vrbadev/Gloves-Equipped-with-Motion-Sensors-Bachelor-Project-HW-FW-SW/Firmware/uVision/lib_sensors/src/LPS22HBSensor.c

/**
 ******************************************************************************
 * @file    LPS22HBSensor.cpp
 * @author  AST
 * @version V1.0.0
 * @date    7 September 2017
 * @brief   Implementation of a LPS22HB Pressure sensor.
 ******************************************************************************
 * @attention
 *
 * <h2><center>&copy; COPYRIGHT(c) 2017 STMicroelectronics</center></h2>
 *
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
 ******************************************************************************
 */


/* Includes ------------------------------------------------------------------*/

#include "../inc/LPS22HBSensor.h"

/* Private functions */
LPS22HBStatusTypeDef LPS22HBSensor_SetODR_When_Enabled  (float odr);
LPS22HBStatusTypeDef LPS22HBSensor_SetODR_When_Disabled (float odr);

/* Private sensor data 
[0] -> isEnabled
[1] -> Last_ODR
*/
extern uint32_t* selected_sensor_private_data;

/* Class Implementation ------------------------------------------------------*/

/** Constructor
 * @param i2c object of an helper class which handles the I2C peripheral
 * @param address the address of the component's instance
 */
LPS22HBStatusTypeDef LPS22HBSensor_Init(void)
{
  if ( LPS22HB_Set_PowerMode( LPS22HB_LowPower) == LPS22HB_ERROR )
  {
    return LPS22HB_STATUS_ERROR;
  }

  /* Power down the device */
  if ( LPS22HB_Set_Odr( LPS22HB_ODR_ONE_SHOT ) == LPS22HB_ERROR )
  {
    return LPS22HB_STATUS_ERROR;
  }

  /* Disable low-pass filter on LPS22HB pressure data */
  if( LPS22HB_Set_LowPassFilter( LPS22HB_DISABLE) == LPS22HB_ERROR )
  {
    return LPS22HB_STATUS_ERROR;
  }

  /* Set low-pass filter cutoff configuration*/
  if( LPS22HB_Set_LowPassFilterCutoff( LPS22HB_ODR_9) == LPS22HB_ERROR )
  {
    return LPS22HB_STATUS_ERROR;
  }

  /* Set block data update mode */
  if ( LPS22HB_Set_Bdu( LPS22HB_BDU_NO_UPDATE ) == LPS22HB_ERROR )
  {
    return LPS22HB_STATUS_ERROR;
  }

  /* Set automatic increment for multi-byte read/write */
  if( LPS22HB_Set_AutomaticIncrementRegAddress( LPS22HB_ENABLE) == LPS22HB_ERROR )
  {
    return LPS22HB_STATUS_ERROR;
  }

  selected_sensor_private_data[0] = 0;
  *((float*) &(selected_sensor_private_data[1])) = 25.0f;
  
  /* Enable the sensor */
  return LPS22HBSensor_Enable();
};



/**
 * @brief  Enable LPS22HB
 * @retval LPS22HB_STATUS_OK in case of success, an error code otherwise
 */
LPS22HBStatusTypeDef LPS22HBSensor_Enable(void)
{
  /* Check if the component is already enabled */
  if ( selected_sensor_private_data[0] == 1 )
  {
    return LPS22HB_STATUS_OK;
  }

  if(LPS22HBSensor_SetODR_When_Enabled(*((float*) &(selected_sensor_private_data[1]))) == LPS22HB_STATUS_ERROR)
  {
    return LPS22HB_STATUS_ERROR;
  }

  selected_sensor_private_data[0] = 1;

  return LPS22HB_STATUS_OK;
}

/**
 * @brief  Disable LPS22HB
 * @retval LPS22HB_STATUS_OK in case of success, an error code otherwise
 */
LPS22HBStatusTypeDef LPS22HBSensor_Disable(void)
{
  /* Check if the component is already disabled */
  if ( selected_sensor_private_data[0] == 0 )
  {
    return LPS22HB_STATUS_OK;
  }

  /* Power down the device */
  if ( LPS22HB_Set_Odr( LPS22HB_ODR_ONE_SHOT ) == LPS22HB_ERROR )
  {
    return LPS22HB_STATUS_ERROR;
  }

  selected_sensor_private_data[0] = 0;

  return LPS22HB_STATUS_OK;
}

/**
 * @brief  Read ID address of LPS22HB
 * @param  ht_id the pointer where the ID of the device is stored
 * @retval LPS22HB_STATUS_OK in case of success, an error code otherwise
 */
LPS22HBStatusTypeDef LPS22HBSensor_ReadID(uint8_t *p_id)
{
  if(!p_id)
  {
    return LPS22HB_STATUS_ERROR;
  }

  /* Read WHO AM I register */
  if ( LPS22HB_Get_DeviceID( p_id ) == LPS22HB_ERROR )
  {
    return LPS22HB_STATUS_ERROR;
  }

  return LPS22HB_STATUS_OK;
}

/**
 * @brief  Reboot memory content of LPS22HB
 * @param  None
 * @retval LPS22HB_STATUS_OK in case of success, an error code otherwise
 */
LPS22HBStatusTypeDef LPS22HBSensor_Reset(void)
{
  /* Read WHO AM I register */
  if ( LPS22HB_MemoryBoot() == LPS22HB_ERROR )
  {
    return LPS22HB_STATUS_ERROR;
  }

  return LPS22HB_STATUS_OK;
}

/**
 * @brief  Read LPS22HB output register, and calculate the pressure in mbar
 * @param  pfData the pressure value in mbar
 * @retval LPS22HB_STATUS_OK in case of success, an error code otherwise
 */
LPS22HBStatusTypeDef LPS22HBSensor_GetPressure(float* pfData)
{
  int32_t int32data = 0;

  /* Read data from LPS22HB. */
  if ( LPS22HB_Get_Pressure( &int32data ) == LPS22HB_ERROR )
  {
    return LPS22HB_STATUS_ERROR;
  }

  *pfData = ( float )int32data / 100.0f;

  return LPS22HB_STATUS_OK;
}

/**
 * @brief  Read LPS22HB output register, and calculate the temperature
 * @param  pfData the temperature value
 * @retval LPS22HB_STATUS_OK in case of success, an error code otherwise
 */
LPS22HBStatusTypeDef LPS22HBSensor_GetTemperature(float *pfData)
{
  int16_t int16data = 0;

  /* Read data from LPS22HB. */
  if ( LPS22HB_Get_Temperature( &int16data ) == LPS22HB_ERROR )
  {
    return LPS22HB_STATUS_ERROR;
  }

  *pfData = ( float )int16data / 10.0f;

  return LPS22HB_STATUS_OK;
}

/**
 * @brief  Read LPS22HB output data rate
 * @param  odr the pointer to the output data rate
 * @retval LPS22HB_STATUS_OK in case of success, an error code otherwise
 */
LPS22HBStatusTypeDef LPS22HBSensor_GetODR(float* odr)
{
  LPS22HB_Odr_et odr_low_level;

  if ( LPS22HB_Get_Odr( &odr_low_level ) == LPS22HB_ERROR )
  {
    return LPS22HB_STATUS_ERROR;
  }

  switch( odr_low_level )
  {
    case LPS22HB_ODR_ONE_SHOT:
      *odr = 0.0f;
      break;
    case LPS22HB_ODR_1HZ:
      *odr = 1.0f;
      break;
    case LPS22HB_ODR_10HZ:
      *odr = 10.0f;
      break;
    case LPS22HB_ODR_25HZ:
      *odr = 25.0f;
      break;
    case LPS22HB_ODR_50HZ:
      *odr = 50.0f;
      break;
    case LPS22HB_ODR_75HZ:
      *odr = 75.0f;
      break;
    default:
      *odr = -1.0f;
      return LPS22HB_STATUS_ERROR;
  }

  return LPS22HB_STATUS_OK;
}

/**
 * @brief  Set ODR
 * @param  odr the output data rate to be set
 * @retval LPS22HB_STATUS_OK in case of success, an error code otherwise
 */
LPS22HBStatusTypeDef LPS22HBSensor_SetODR(float odr)
{
  if(selected_sensor_private_data[0] == 1)
  {
    if(LPS22HBSensor_SetODR_When_Enabled(odr) == LPS22HB_STATUS_ERROR)
    {
      return LPS22HB_STATUS_ERROR;
    }
  }
  else
  {
    if(LPS22HBSensor_SetODR_When_Disabled(odr) == LPS22HB_STATUS_ERROR)
    {
      return LPS22HB_STATUS_ERROR;
    }
  }

  return LPS22HB_STATUS_OK;
}


/**
 * @brief Set the LPS22HB sensor output data rate when enabled
 * @param odr the functional output data rate to be set
 * @retval LPS22HB_STATUS_OK in case of success
 * @retval LPS22HB_STATUS_ERROR in case of failure
 */
LPS22HBStatusTypeDef LPS22HBSensor_SetODR_When_Enabled( float odr )
{
  LPS22HB_Odr_et new_odr;

  new_odr = ( odr <=  1.0f ) ? LPS22HB_ODR_1HZ
          : ( odr <= 10.0f ) ? LPS22HB_ODR_10HZ
          : ( odr <= 25.0f ) ? LPS22HB_ODR_25HZ
          : ( odr <= 50.0f ) ? LPS22HB_ODR_50HZ
          :                    LPS22HB_ODR_75HZ;

  if ( LPS22HB_Set_Odr( new_odr ) == LPS22HB_ERROR )
  {
    return LPS22HB_STATUS_ERROR;
  }

  if ( LPS22HBSensor_GetODR( &*((float*) &(selected_sensor_private_data[1])) ) == LPS22HB_STATUS_ERROR )
  {
    return LPS22HB_STATUS_ERROR;
  }

  return LPS22HB_STATUS_OK;
}

/**
 * @brief Set the LPS22HB sensor output data rate when disabled
 * @param odr the functional output data rate to be set
 * @retval LPS22HB_STATUS_OK in case of success
 * @retval LPS22HB_STATUS_ERROR in case of failure
 */
LPS22HBStatusTypeDef LPS22HBSensor_SetODR_When_Disabled( float odr )
{
  *((float*) &(selected_sensor_private_data[1])) = ( odr <=  1.0f ) ? 1.0f
           : ( odr <= 10.0f ) ? 10.0f
           : ( odr <= 25.0f ) ? 25.0f
           : ( odr <= 50.0f ) ? 50.0f
           :                    75.0f;

  return LPS22HB_STATUS_OK;
}


/**
 * @brief Read the data from register
 * @param reg register address
 * @param data register data
 * @retval LPS22HB_STATUS_OK in case of success
 * @retval LPS22HB_STATUS_ERROR in case of failure
 */
LPS22HBStatusTypeDef LPS22HBSensor_ReadReg( uint8_t reg, uint8_t *data )
{

  if ( LPS22HB_ReadReg( reg, 1, data ) == LPS22HB_ERROR )
  {
    return LPS22HB_STATUS_ERROR;
  }

  return LPS22HB_STATUS_OK;
}

/**
 * @brief Write the data to register
 * @param reg register address
 * @param data register data
 * @retval LPS22HB_STATUS_OK in case of success
 * @retval LPS22HB_STATUS_ERROR in case of failure
 */
LPS22HBStatusTypeDef LPS22HBSensor_WriteReg( uint8_t reg, uint8_t data )
{

  if ( LPS22HB_WriteReg( reg, 1, &data ) == LPS22HB_ERROR )
  {
    return LPS22HB_STATUS_ERROR;
  }

  return LPS22HB_STATUS_OK;
}
