vrbadev/Gloves-Equipped-with-Motion-Sensors-Bachelor-Project-HW-FW-SW/Firmware/uVision/lib_sensors/src/LSM6DSL_ACC_GYRO_Driver.c

/**
 ******************************************************************************
 * @file    LSM6DSL_ACC_GYRO_driver.c
 * @author  MEMS Application Team
 * @version V1.5
 * @date    17-May-2016
 * @brief   LSM6DSL driver file
 ******************************************************************************
 * @attention
 *
 * <h2><center>&copy; COPYRIGHT(c) 2017 STMicroelectronics</center></h2>
 *
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
 ******************************************************************************
 */

/* Includes ------------------------------------------------------------------*/
#include "../inc/LSM6DSL_ACC_GYRO_Driver.h"   

/* Imported function prototypes ----------------------------------------------*/
extern int i2c_write(uint8_t reg, uint8_t* data, uint8_t len);
extern int i2c_read(uint8_t reg, uint8_t* data, uint8_t len);

/* Private typedef -----------------------------------------------------------*/

/* Private define ------------------------------------------------------------*/

/* Private macro -------------------------------------------------------------*/

/* Private variables ---------------------------------------------------------*/

/* Private functions ---------------------------------------------------------*/

/* Exported functions ---------------------------------------------------------*/

/************** Generic Function  *******************/

/*******************************************************************************
* Function Name		: LSM6DSL_ACC_GYRO_ReadReg
* Description		: Generic Reading function. It must be fullfilled with either
*					: I2C or SPI reading functions
* Input				: Register Address, length of buffer
* Output			: Data REad
* Return			: None
*******************************************************************************/
mems_status_t LSM6DSL_ACC_GYRO_ReadReg(uint8_t Reg, uint8_t* Data, uint16_t len)
{
  if (i2c_read(Reg, Data, len))
  {
    return MEMS_ERROR;
  }
  else
  {
    return MEMS_SUCCESS;
  }
}

/*******************************************************************************
* Function Name		: LSM6DSL_ACC_GYRO_WriteReg
* Description		: Generic Writing function. It must be fullfilled with either
*					: I2C or SPI writing function
* Input				: Register Address, Data to be written, length of buffer
* Output			: None
* Return			: None
*******************************************************************************/
mems_status_t LSM6DSL_ACC_GYRO_WriteReg(uint8_t Reg, uint8_t *Data, uint16_t len)
{
  if (i2c_write(Reg, Data, len))
  {
    return MEMS_ERROR;
  }
  else
  {
    return MEMS_SUCCESS;
  }
}

/**************** Base Function  *******************/

/*******************************************************************************
* Function Name  : LSM6DSL_ACC_GYRO_R_WHO_AM_I
* Description    : Read WHO_AM_I_BIT
* Input          : Pointer to uint8_t
* Output         : Status of WHO_AM_I_BIT
* Return         : Status [MEMS_ERROR, MEMS_SUCCESS]
*******************************************************************************/
mems_status_t LSM6DSL_ACC_GYRO_R_WHO_AM_I(uint8_t *value)
{
 if( !LSM6DSL_ACC_GYRO_ReadReg(LSM6DSL_ACC_GYRO_WHO_AM_I_REG, (uint8_t *)value, 1))
    return MEMS_ERROR;

  *value &= LSM6DSL_ACC_GYRO_WHO_AM_I_BIT_MASK; //coerce
  *value = *value >> LSM6DSL_ACC_GYRO_WHO_AM_I_BIT_POSITION; //mask

  return MEMS_SUCCESS;
}

/*******************************************************************************
* Function Name  : LSM6DSL_ACC_GYRO_W_BDU
* Description    : Write BDU
* Input          : LSM6DSL_ACC_GYRO_BDU_t
* Output         : None
* Return         : Status [MEMS_ERROR, MEMS_SUCCESS]
*******************************************************************************/
mems_status_t  LSM6DSL_ACC_GYRO_W_BDU(LSM6DSL_ACC_GYRO_BDU_t newValue)
{
  uint8_t value;

  if( !LSM6DSL_ACC_GYRO_ReadReg(LSM6DSL_ACC_GYRO_CTRL3_C, &value, 1))
    return MEMS_ERROR;

  value &= ~LSM6DSL_ACC_GYRO_BDU_MASK;
  value |= newValue;

  if( !LSM6DSL_ACC_GYRO_WriteReg(LSM6DSL_ACC_GYRO_CTRL3_C, &value, 1) )
    return MEMS_ERROR;

  return MEMS_SUCCESS;
}

/*******************************************************************************
* Function Name  : LSM6DSL_ACC_GYRO_R_BDU
* Description    : Read BDU
* Input          : Pointer to LSM6DSL_ACC_GYRO_BDU_t
* Output         : Status of BDU see LSM6DSL_ACC_GYRO_BDU_t
* Return         : Status [MEMS_ERROR, MEMS_SUCCESS]
*******************************************************************************/
mems_status_t LSM6DSL_ACC_GYRO_R_BDU(LSM6DSL_ACC_GYRO_BDU_t *value)
{
 if( !LSM6DSL_ACC_GYRO_ReadReg(LSM6DSL_ACC_GYRO_CTRL3_C, (uint8_t *)value, 1))
    return MEMS_ERROR;

  *value &= LSM6DSL_ACC_GYRO_BDU_MASK; //mask

  return MEMS_SUCCESS;
}

/*******************************************************************************
* Function Name  : LSM6DSL_ACC_GYRO_W_FS_XL
* Description    : Write FS_XL
* Input          : LSM6DSL_ACC_GYRO_FS_XL_t
* Output         : None
* Return         : Status [MEMS_ERROR, MEMS_SUCCESS]
*******************************************************************************/
mems_status_t  LSM6DSL_ACC_GYRO_W_FS_XL(LSM6DSL_ACC_GYRO_FS_XL_t newValue)
{
  uint8_t value;

  if( !LSM6DSL_ACC_GYRO_ReadReg(LSM6DSL_ACC_GYRO_CTRL1_XL, &value, 1))
    return MEMS_ERROR;

  value &= ~LSM6DSL_ACC_GYRO_FS_XL_MASK;
  value |= newValue;

  if( !LSM6DSL_ACC_GYRO_WriteReg(LSM6DSL_ACC_GYRO_CTRL1_XL, &value, 1) )
    return MEMS_ERROR;

  return MEMS_SUCCESS;
}

/*******************************************************************************
* Function Name  : LSM6DSL_ACC_GYRO_R_FS_XL
* Description    : Read FS_XL
* Input          : Pointer to LSM6DSL_ACC_GYRO_FS_XL_t
* Output         : Status of FS_XL see LSM6DSL_ACC_GYRO_FS_XL_t
* Return         : Status [MEMS_ERROR, MEMS_SUCCESS]
*******************************************************************************/
mems_status_t LSM6DSL_ACC_GYRO_R_FS_XL(LSM6DSL_ACC_GYRO_FS_XL_t *value)
{
 if( !LSM6DSL_ACC_GYRO_ReadReg(LSM6DSL_ACC_GYRO_CTRL1_XL, (uint8_t *)value, 1))
    return MEMS_ERROR;

  *value &= LSM6DSL_ACC_GYRO_FS_XL_MASK; //mask

  return MEMS_SUCCESS;
}

/*******************************************************************************
* Function Name  : mems_status_t LSM6DSL_ACC_GYRO_GetRawAccData(uint8_t *buff)
* Description    : Read GetAccData output register
* Input          : pointer to [uint8_t]
* Output         : GetAccData buffer uint8_t
* Return         : Status [MEMS_ERROR, MEMS_SUCCESS]
*******************************************************************************/
mems_status_t LSM6DSL_ACC_GYRO_GetRawAccData(uint8_t *buff)
{
  uint8_t i, j, k;
  uint8_t numberOfByteForDimension;

  numberOfByteForDimension=6/3;

  k=0;
  for (i=0; i<3;i++ )
  {
	for (j=0; j<numberOfByteForDimension;j++ )
	{
		if( !LSM6DSL_ACC_GYRO_ReadReg(LSM6DSL_ACC_GYRO_OUTX_L_XL+k, &buff[k], 1))
		  return MEMS_ERROR;
		k++;
	}
  }

  return MEMS_SUCCESS;
}

/*******************************************************************************
* Function Name  : mems_status_t LSM6DSL_ACC_Get_Acceleration(int *buff, uint8_t from_fifo)
* Description    : Read GetAccData output register
* Input          : pointer to [uint8_t]
* Output         : values are expressed in mg
* Return         : Status [MEMS_ERROR, MEMS_SUCCESS]
*******************************************************************************/
/*
 * Following is the table of sensitivity values for each case.
 * Values are expressed in ug/digit.
 */
static const long long LSM6DSL_ACC_Sensitivity_List[4] = {
      61,	/* FS @2g */
      122,	/* FS @4g */
      244,	/* FS @8g */
      488,	/* FS @16g */
};
mems_status_t LSM6DSL_ACC_Get_Acceleration(int *buff, uint8_t from_fifo)
{
  LSM6DSL_ACC_GYRO_FS_XL_t fs;
  long long sensitivity = 0;
  Type3Axis16bit_U raw_data_tmp;

  /* Read out current odr, fs, hf setting */
  LSM6DSL_ACC_GYRO_R_FS_XL(&fs);

  /* Determine the sensitivity according to fs */
  switch(fs) {
  case LSM6DSL_ACC_GYRO_FS_XL_2g:
    sensitivity = LSM6DSL_ACC_Sensitivity_List[0];
    break;

  case LSM6DSL_ACC_GYRO_FS_XL_4g:
    sensitivity = LSM6DSL_ACC_Sensitivity_List[1];
    break;

  case LSM6DSL_ACC_GYRO_FS_XL_8g:
    sensitivity = LSM6DSL_ACC_Sensitivity_List[2];
    break;

  case LSM6DSL_ACC_GYRO_FS_XL_16g:
    sensitivity = LSM6DSL_ACC_Sensitivity_List[3];
    break;
  }

  /* Read out raw accelerometer samples */
  if (from_fifo) {
    uint8_t i;

    /* read all 3 axis from FIFO */
    for(i = 0; i < 3; i++)
      LSM6DSL_ACC_GYRO_Get_GetFIFOData(raw_data_tmp.u8bit + 2*i);
  } else
    LSM6DSL_ACC_GYRO_GetRawAccData(raw_data_tmp.u8bit);

  /* Apply proper shift and sensitivity */
  buff[0] = (raw_data_tmp.i16bit[0] * sensitivity + 500)/1000;
  buff[1] = (raw_data_tmp.i16bit[1] * sensitivity + 500)/1000;
  buff[2] = (raw_data_tmp.i16bit[2] * sensitivity + 500)/1000;

  return MEMS_SUCCESS;
}

/*******************************************************************************
* Function Name  : LSM6DSL_ACC_GYRO_W_ODR_XL
* Description    : Write ODR_XL
* Input          : LSM6DSL_ACC_GYRO_ODR_XL_t
* Output         : None
* Return         : Status [MEMS_ERROR, MEMS_SUCCESS]
*******************************************************************************/
mems_status_t  LSM6DSL_ACC_GYRO_W_ODR_XL(LSM6DSL_ACC_GYRO_ODR_XL_t newValue)
{
  uint8_t value;

  if( !LSM6DSL_ACC_GYRO_ReadReg(LSM6DSL_ACC_GYRO_CTRL1_XL, &value, 1))
    return MEMS_ERROR;

  value &= ~LSM6DSL_ACC_GYRO_ODR_XL_MASK;
  value |= newValue;

  if( !LSM6DSL_ACC_GYRO_WriteReg(LSM6DSL_ACC_GYRO_CTRL1_XL, &value, 1) )
    return MEMS_ERROR;

  return MEMS_SUCCESS;
}

/*******************************************************************************
* Function Name  : LSM6DSL_ACC_GYRO_R_ODR_XL
* Description    : Read ODR_XL
* Input          : Pointer to LSM6DSL_ACC_GYRO_ODR_XL_t
* Output         : Status of ODR_XL see LSM6DSL_ACC_GYRO_ODR_XL_t
* Return         : Status [MEMS_ERROR, MEMS_SUCCESS]
*******************************************************************************/
mems_status_t LSM6DSL_ACC_GYRO_R_ODR_XL(LSM6DSL_ACC_GYRO_ODR_XL_t *value)
{
 if( !LSM6DSL_ACC_GYRO_ReadReg(LSM6DSL_ACC_GYRO_CTRL1_XL, (uint8_t *)value, 1))
    return MEMS_ERROR;

  *value &= LSM6DSL_ACC_GYRO_ODR_XL_MASK; //mask

  return MEMS_SUCCESS;
}

/*******************************************************************************
* Function Name  : LSM6DSL_ACC_GYRO_translate_ODR_XL
* Description    : Read ODR_XL
* Input          : LSM6DSL_ACC_GYRO_ODR_XL_t
* Output         : The ODR value in Hz
* Return         : Status [MEMS_ERROR, MEMS_SUCCESS]
*******************************************************************************/
mems_status_t LSM6DSL_ACC_GYRO_translate_ODR_XL(LSM6DSL_ACC_GYRO_ODR_XL_t value, uint16_t *odr_hz_val)
{
  switch(value) {
  case LSM6DSL_ACC_GYRO_ODR_XL_POWER_DOWN:
    *odr_hz_val = 0;
    break;

  case LSM6DSL_ACC_GYRO_ODR_XL_13Hz:
    *odr_hz_val = 13;
    break;

  case LSM6DSL_ACC_GYRO_ODR_XL_26Hz:
    *odr_hz_val = 26;
    break;

  case LSM6DSL_ACC_GYRO_ODR_XL_52Hz:
    *odr_hz_val = 52;
    break;

  case LSM6DSL_ACC_GYRO_ODR_XL_104Hz:
    *odr_hz_val = 104;
    break;

  case LSM6DSL_ACC_GYRO_ODR_XL_208Hz:
    *odr_hz_val = 208;
    break;

  case LSM6DSL_ACC_GYRO_ODR_XL_416Hz:
    *odr_hz_val = 416;
    break;

  case LSM6DSL_ACC_GYRO_ODR_XL_833Hz:
    *odr_hz_val = 833;
    break;

  case LSM6DSL_ACC_GYRO_ODR_XL_1660Hz:
    *odr_hz_val = 1660;
    break;

  default:
    return MEMS_ERROR;
  }

  return MEMS_SUCCESS;
}

/*******************************************************************************
* Function Name  : LSM6DSL_ACC_GYRO_W_FS_G
* Description    : Write FS_G
* Input          : LSM6DSL_ACC_GYRO_FS_G_t
* Output         : None
* Return         : Status [MEMS_ERROR, MEMS_SUCCESS]
*******************************************************************************/
mems_status_t  LSM6DSL_ACC_GYRO_W_FS_G(LSM6DSL_ACC_GYRO_FS_G_t newValue)
{
  uint8_t value;

  if( !LSM6DSL_ACC_GYRO_ReadReg(LSM6DSL_ACC_GYRO_CTRL2_G, &value, 1))
    return MEMS_ERROR;

  value &= ~LSM6DSL_ACC_GYRO_FS_G_MASK;
  value |= newValue;

  if( !LSM6DSL_ACC_GYRO_WriteReg(LSM6DSL_ACC_GYRO_CTRL2_G, &value, 1) )
    return MEMS_ERROR;

  return MEMS_SUCCESS;
}

/*******************************************************************************
* Function Name  : LSM6DSL_ACC_GYRO_R_FS_G
* Description    : Read FS_G
* Input          : Pointer to LSM6DSL_ACC_GYRO_FS_G_t
* Output         : Status of FS_G see LSM6DSL_ACC_GYRO_FS_G_t
* Return         : Status [MEMS_ERROR, MEMS_SUCCESS]
*******************************************************************************/
mems_status_t LSM6DSL_ACC_GYRO_R_FS_G(LSM6DSL_ACC_GYRO_FS_G_t *value)
{
 if( !LSM6DSL_ACC_GYRO_ReadReg(LSM6DSL_ACC_GYRO_CTRL2_G, (uint8_t *)value, 1))
    return MEMS_ERROR;

  *value &= LSM6DSL_ACC_GYRO_FS_G_MASK; //mask

  return MEMS_SUCCESS;
}

/*******************************************************************************
* Function Name  : mems_status_t LSM6DSL_ACC_GYRO_GetRawGyroData(uint8_t *buff)
* Description    : Read GetGyroData output register
* Input          : pointer to [uint8_t]
* Output         : GetGyroData buffer uint8_t
* Return         : Status [MEMS_ERROR, MEMS_SUCCESS]
*******************************************************************************/
mems_status_t LSM6DSL_ACC_GYRO_GetRawGyroData(uint8_t *buff)
{
  uint8_t i, j, k;
  uint8_t numberOfByteForDimension;

  numberOfByteForDimension=6/3;

  k=0;
  for (i=0; i<3;i++ )
  {
	for (j=0; j<numberOfByteForDimension;j++ )
	{
		if( !LSM6DSL_ACC_GYRO_ReadReg(LSM6DSL_ACC_GYRO_OUTX_L_G+k, &buff[k], 1))
		  return MEMS_ERROR;
		k++;
	}
  }

  return MEMS_SUCCESS;
}

/*******************************************************************************
* Function Name  : mems_status_t LSM6DSL_ACC_Get_AngularRate(uint8_t *buff)
* Description    : Read GetGyroData output register
* Input          : pointer to [uint8_t]
* Output         : Returned values are espressed in mdps
* Return         : Status [MEMS_ERROR, MEMS_SUCCESS]
*******************************************************************************/
/*
 * Following is the table of sensitivity values for each case.
 * Values are espressed in udps/digit.
 */
static const long long LSM6DSL_GYRO_Sensitivity_List[5] = {
      4375,	/* FS @125 */
      8750,	/* FS @245 */
      17500,	/* FS @500 */
      35000,	/* FS @1000 */
      70000,	/* FS @2000 */
};
mems_status_t LSM6DSL_ACC_Get_AngularRate(int *buff, uint8_t from_fifo)
{
  LSM6DSL_ACC_GYRO_FS_125_t fs_125;
  LSM6DSL_ACC_GYRO_FS_G_t fs;
  long long sensitivity = 0;
  Type3Axis16bit_U raw_data_tmp;

  /* Read out current odr, fs, hf setting */
  LSM6DSL_ACC_GYRO_R_FS_125(&fs_125);
  if (fs_125 == LSM6DSL_ACC_GYRO_FS_125_ENABLED) {
    sensitivity = LSM6DSL_GYRO_Sensitivity_List[0];
  } else {
    LSM6DSL_ACC_GYRO_R_FS_G(&fs);

    /* Determine the sensitivity according to fs */
    switch(fs) {
    case LSM6DSL_ACC_GYRO_FS_G_245dps:
      sensitivity = LSM6DSL_GYRO_Sensitivity_List[1];
      break;

    case LSM6DSL_ACC_GYRO_FS_G_500dps:
      sensitivity = LSM6DSL_GYRO_Sensitivity_List[2];
      break;

    case LSM6DSL_ACC_GYRO_FS_G_1000dps:
      sensitivity = LSM6DSL_GYRO_Sensitivity_List[3];
      break;

    case LSM6DSL_ACC_GYRO_FS_G_2000dps:
      sensitivity = LSM6DSL_GYRO_Sensitivity_List[4];
      break;
    }
  }

  /* Read out raw accelerometer samples */
  if (from_fifo) {
    uint8_t i;

    /* read all 3 axis from FIFO */
    for(i = 0; i < 3; i++)
      LSM6DSL_ACC_GYRO_Get_GetFIFOData(raw_data_tmp.u8bit + 2*i);
  } else
    LSM6DSL_ACC_GYRO_GetRawGyroData(raw_data_tmp.u8bit);

  /* Apply proper shift and sensitivity */
  buff[0] = (raw_data_tmp.i16bit[0] * sensitivity + 500)/1000;
  buff[1] = (raw_data_tmp.i16bit[1] * sensitivity + 500)/1000;
  buff[2] = (raw_data_tmp.i16bit[2] * sensitivity + 500)/1000;

  return MEMS_SUCCESS;
}

/*******************************************************************************
* Function Name  : LSM6DSL_ACC_GYRO_W_ODR_G
* Description    : Write ODR_G
* Input          : LSM6DSL_ACC_GYRO_ODR_G_t
* Output         : None
* Return         : Status [MEMS_ERROR, MEMS_SUCCESS]
*******************************************************************************/
mems_status_t  LSM6DSL_ACC_GYRO_W_ODR_G(LSM6DSL_ACC_GYRO_ODR_G_t newValue)
{
  uint8_t value;

  if( !LSM6DSL_ACC_GYRO_ReadReg(LSM6DSL_ACC_GYRO_CTRL2_G, &value, 1))
    return MEMS_ERROR;

  value &= ~LSM6DSL_ACC_GYRO_ODR_G_MASK;
  value |= newValue;

  if( !LSM6DSL_ACC_GYRO_WriteReg(LSM6DSL_ACC_GYRO_CTRL2_G, &value, 1) )
    return MEMS_ERROR;

  return MEMS_SUCCESS;
}

/*******************************************************************************
* Function Name  : LSM6DSL_ACC_GYRO_R_ODR_G
* Description    : Read ODR_G
* Input          : Pointer to LSM6DSL_ACC_GYRO_ODR_G_t
* Output         : Status of ODR_G see LSM6DSL_ACC_GYRO_ODR_G_t
* Return         : Status [MEMS_ERROR, MEMS_SUCCESS]
*******************************************************************************/
mems_status_t LSM6DSL_ACC_GYRO_R_ODR_G(LSM6DSL_ACC_GYRO_ODR_G_t *value)
{
 if( !LSM6DSL_ACC_GYRO_ReadReg(LSM6DSL_ACC_GYRO_CTRL2_G, (uint8_t *)value, 1))
    return MEMS_ERROR;

  *value &= LSM6DSL_ACC_GYRO_ODR_G_MASK; //mask

  return MEMS_SUCCESS;
}

/*******************************************************************************
* Function Name  : LSM6DSL_ACC_GYRO_translate_ODR_G
* Description    : Read ODR_G
* Input          : LSM6DSL_ACC_GYRO_ODR_G_t
* Output         : The ODR value in Hz
* Return         : Status [MEMS_ERROR, MEMS_SUCCESS]
*******************************************************************************/
mems_status_t LSM6DSL_ACC_GYRO_translate_ODR_G(LSM6DSL_ACC_GYRO_ODR_G_t value, uint16_t *odr_hz_val)
{
  switch(value) {
  case LSM6DSL_ACC_GYRO_ODR_G_POWER_DOWN:
    *odr_hz_val = 0;
    break;

  case LSM6DSL_ACC_GYRO_ODR_G_13Hz:
    *odr_hz_val = 13;
    break;

  case LSM6DSL_ACC_GYRO_ODR_G_26Hz:
    *odr_hz_val = 26;
    break;

  case LSM6DSL_ACC_GYRO_ODR_G_52Hz:
    *odr_hz_val = 52;
    break;

  case LSM6DSL_ACC_GYRO_ODR_G_104Hz:
    *odr_hz_val = 104;
    break;

  case LSM6DSL_ACC_GYRO_ODR_G_208Hz:
    *odr_hz_val = 208;
    break;

  case LSM6DSL_ACC_GYRO_ODR_G_416Hz:
    *odr_hz_val = 416;
    break;

  case LSM6DSL_ACC_GYRO_ODR_G_833Hz:
    *odr_hz_val = 833;
    break;

  case LSM6DSL_ACC_GYRO_ODR_G_1660Hz:
    *odr_hz_val = 1660;
    break;

  default:
    return MEMS_ERROR;
  }

  return MEMS_SUCCESS;
}

/*******************************************************************************
* Function Name  : LSM6DSL_ACC_GYRO_W_FS_125
* Description    : Write FS_125
* Input          : LSM6DSL_ACC_GYRO_FS_125_t
* Output         : None
* Return         : Status [MEMS_ERROR, MEMS_SUCCESS]
*******************************************************************************/
mems_status_t  LSM6DSL_ACC_GYRO_W_FS_125(LSM6DSL_ACC_GYRO_FS_125_t newValue)
{
  uint8_t value;

  if( !LSM6DSL_ACC_GYRO_ReadReg(LSM6DSL_ACC_GYRO_CTRL2_G, &value, 1))
    return MEMS_ERROR;

  value &= ~LSM6DSL_ACC_GYRO_FS_125_MASK;
  value |= newValue;

  if( !LSM6DSL_ACC_GYRO_WriteReg(LSM6DSL_ACC_GYRO_CTRL2_G, &value, 1) )
    return MEMS_ERROR;

  return MEMS_SUCCESS;
}

/*******************************************************************************
* Function Name  : LSM6DSL_ACC_GYRO_R_FS_125
* Description    : Read FS_125
* Input          : Pointer to LSM6DSL_ACC_GYRO_FS_125_t
* Output         : Status of FS_125 see LSM6DSL_ACC_GYRO_FS_125_t
* Return         : Status [MEMS_ERROR, MEMS_SUCCESS]
*******************************************************************************/
mems_status_t LSM6DSL_ACC_GYRO_R_FS_125(LSM6DSL_ACC_GYRO_FS_125_t *value)
{
 if( !LSM6DSL_ACC_GYRO_ReadReg(LSM6DSL_ACC_GYRO_CTRL2_G, (uint8_t *)value, 1))
    return MEMS_ERROR;

  *value &= LSM6DSL_ACC_GYRO_FS_125_MASK; //mask

  return MEMS_SUCCESS;
}

/**************** Advanced Function  *******************/

/*******************************************************************************
* Function Name  : LSM6DSL_ACC_GYRO_W_BW_SEL
* Description    : Write BW_SEL
* Input          : LSM6DSL_ACC_GYRO_BW_SEL_t
* Output         : None
* Return         : Status [MEMS_ERROR, MEMS_SUCCESS]
*******************************************************************************/
mems_status_t  LSM6DSL_ACC_GYRO_W_BW_SEL(LSM6DSL_ACC_GYRO_BW_SEL_t newValue)
{
  uint8_t value;

  if( !LSM6DSL_ACC_GYRO_ReadReg(LSM6DSL_ACC_GYRO_CTRL1_XL, &value, 1))
    return MEMS_ERROR;

  value &= ~LSM6DSL_ACC_GYRO_BW_SEL_MASK;
  value |= newValue;

  if( !LSM6DSL_ACC_GYRO_WriteReg(LSM6DSL_ACC_GYRO_CTRL1_XL, &value, 1) )
    return MEMS_ERROR;

  return MEMS_SUCCESS;
}

/*******************************************************************************
* Function Name  : LSM6DSL_ACC_GYRO_R_BW_SEL
* Description    : Read BW_SEL
* Input          : Pointer to LSM6DSL_ACC_GYRO_BW_SEL_t
* Output         : Status of BW_SEL see LSM6DSL_ACC_GYRO_BW_SEL_t
* Return         : Status [MEMS_ERROR, MEMS_SUCCESS]
*******************************************************************************/
mems_status_t LSM6DSL_ACC_GYRO_R_BW_SEL(LSM6DSL_ACC_GYRO_BW_SEL_t *value)
{
 if( !LSM6DSL_ACC_GYRO_ReadReg(LSM6DSL_ACC_GYRO_CTRL1_XL, (uint8_t *)value, 1))
    return MEMS_ERROR;

  *value &= LSM6DSL_ACC_GYRO_BW_SEL_MASK; //mask

  return MEMS_SUCCESS;
}

/*******************************************************************************
* Function Name  : LSM6DSL_ACC_GYRO_W_BLE
* Description    : Write BLE
* Input          : LSM6DSL_ACC_GYRO_BLE_t
* Output         : None
* Return         : Status [MEMS_ERROR, MEMS_SUCCESS]
*******************************************************************************/
mems_status_t  LSM6DSL_ACC_GYRO_W_BLE(LSM6DSL_ACC_GYRO_BLE_t newValue)
{
  uint8_t value;

  if( !LSM6DSL_ACC_GYRO_ReadReg(LSM6DSL_ACC_GYRO_CTRL3_C, &value, 1))
    return MEMS_ERROR;

  value &= ~LSM6DSL_ACC_GYRO_BLE_MASK;
  value |= newValue;

  if( !LSM6DSL_ACC_GYRO_WriteReg(LSM6DSL_ACC_GYRO_CTRL3_C, &value, 1) )
    return MEMS_ERROR;

  return MEMS_SUCCESS;
}

/*******************************************************************************
* Function Name  : LSM6DSL_ACC_GYRO_R_BLE
* Description    : Read BLE
* Input          : Pointer to LSM6DSL_ACC_GYRO_BLE_t
* Output         : Status of BLE see LSM6DSL_ACC_GYRO_BLE_t
* Return         : Status [MEMS_ERROR, MEMS_SUCCESS]
*******************************************************************************/
mems_status_t LSM6DSL_ACC_GYRO_R_BLE(LSM6DSL_ACC_GYRO_BLE_t *value)
{
 if( !LSM6DSL_ACC_GYRO_ReadReg(LSM6DSL_ACC_GYRO_CTRL3_C, (uint8_t *)value, 1))
    return MEMS_ERROR;

  *value &= LSM6DSL_ACC_GYRO_BLE_MASK; //mask

  return MEMS_SUCCESS;
}

/*******************************************************************************
* Function Name  : LSM6DSL_ACC_GYRO_W_EmbeddedAccess
* Description    : Write EMB_ACC
* Input          : LSM6DSL_ACC_GYRO_EMB_ACC_t
* Output         : None
* Return         : Status [MEMS_ERROR, MEMS_SUCCESS]
*******************************************************************************/
mems_status_t  LSM6DSL_ACC_GYRO_W_EmbeddedAccess(LSM6DSL_ACC_GYRO_EMB_ACC_t newValue)
{
  uint8_t value;

  if( !LSM6DSL_ACC_GYRO_ReadReg(LSM6DSL_ACC_GYRO_FUNC_CFG_ACCESS, &value, 1) )
    return MEMS_ERROR;

  value &= ~LSM6DSL_ACC_GYRO_EMB_ACC_MASK;
  value |= newValue;

  if( !LSM6DSL_ACC_GYRO_WriteReg(LSM6DSL_ACC_GYRO_FUNC_CFG_ACCESS, &value, 1) )
    return MEMS_ERROR;

  return MEMS_SUCCESS;
}

/*******************************************************************************
* Function Name  : LSM6DSL_ACC_GYRO_R_EmbeddedAccess
* Description    : Read EMB_ACC
* Input          : Pointer to LSM6DSL_ACC_GYRO_EMB_ACC_t
* Output         : Status of EMB_ACC see LSM6DSL_ACC_GYRO_EMB_ACC_t
* Return         : Status [MEMS_ERROR, MEMS_SUCCESS]
*******************************************************************************/
mems_status_t LSM6DSL_ACC_GYRO_R_EmbeddedAccess(LSM6DSL_ACC_GYRO_EMB_ACC_t *value)
{
 if( !LSM6DSL_ACC_GYRO_ReadReg(LSM6DSL_ACC_GYRO_FUNC_CFG_ACCESS, (uint8_t *)value, 1) )
    return MEMS_ERROR;

  *value &= LSM6DSL_ACC_GYRO_EMB_ACC_MASK; //mask

  return MEMS_SUCCESS;
}

/*******************************************************************************
* Function Name  : LSM6DSL_ACC_GYRO_W_SYNC_RES_RATIO
* Description    : Write RR
* Input          : LSM6DSL_ACC_GYRO_SYNC_RES_RATIO_t
* Output         : None
* Return         : Status [MEMS_ERROR, MEMS_SUCCESS]
*******************************************************************************/
mems_status_t  LSM6DSL_ACC_GYRO_W_SYNC_RES_RATIO(LSM6DSL_ACC_GYRO_SYNC_RES_RATIO_t newValue)
{
  uint8_t value;

  if( !LSM6DSL_ACC_GYRO_ReadReg(LSM6DSL_ACC_GYRO_SENSOR_RES_RATIO, &value, 1) )
    return MEMS_ERROR;

  value &= ~LSM6DSL_ACC_GYRO_SYNC_RES_RATIO_MASK;
  value |= newValue;

  if( !LSM6DSL_ACC_GYRO_WriteReg(LSM6DSL_ACC_GYRO_SENSOR_RES_RATIO, &value, 1) )
    return MEMS_ERROR;

  return MEMS_SUCCESS;
}

/*******************************************************************************
* Function Name  : LSM6DSL_ACC_GYRO_R_SYNC_RES_RATIO
* Description    : Read RR
* Input          : Pointer to LSM6DSL_ACC_GYRO_SYNC_RES_RATIO_t
* Output         : Status of RR see LSM6DSL_ACC_GYRO_SYNC_RES_RATIO_t
* Return         : Status [MEMS_ERROR, MEMS_SUCCESS]
*******************************************************************************/
mems_status_t LSM6DSL_ACC_GYRO_R_SYNC_RES_RATIO(LSM6DSL_ACC_GYRO_SYNC_RES_RATIO_t *value)
{
 if( !LSM6DSL_ACC_GYRO_ReadReg(LSM6DSL_ACC_GYRO_SENSOR_RES_RATIO, (uint8_t *)value, 1) )
    return MEMS_ERROR;

  *value &= LSM6DSL_ACC_GYRO_SYNC_RES_RATIO_MASK; //mask

  return MEMS_SUCCESS;
}

/*******************************************************************************
* Function Name  : LSM6DSL_ACC_GYRO_W_Stamping_Time_Frame
* Description    : Write TPH
* Input          : uint8_t
* Output         : None
* Return         : Status [MEMS_ERROR, MEMS_SUCCESS]
*******************************************************************************/
mems_status_t  LSM6DSL_ACC_GYRO_W_Stamping_Time_Frame(uint8_t newValue)
{
  uint8_t value;

  newValue = newValue << LSM6DSL_ACC_GYRO_TPH_POSITION; //mask
  newValue &= LSM6DSL_ACC_GYRO_TPH_MASK; //coerce

  if( !LSM6DSL_ACC_GYRO_ReadReg(LSM6DSL_ACC_GYRO_SENSOR_SYNC_TIME, &value, 1) )
    return MEMS_ERROR;

  value &= (uint8_t)~LSM6DSL_ACC_GYRO_TPH_MASK;
  value |= newValue;

  if( !LSM6DSL_ACC_GYRO_WriteReg(LSM6DSL_ACC_GYRO_SENSOR_SYNC_TIME, &value, 1) )
    return MEMS_ERROR;

  return MEMS_SUCCESS;
}

/*******************************************************************************
* Function Name  : LSM6DSL_ACC_GYRO_R_Stamping_Time_Frame
* Description    : Read TPH
* Input          : Pointer to uint8_t
* Output         : Status of TPH
* Return         : Status [MEMS_ERROR, MEMS_SUCCESS]
*******************************************************************************/
mems_status_t LSM6DSL_ACC_GYRO_R_Stamping_Time_Frame(uint8_t *value)
{
 if( !LSM6DSL_ACC_GYRO_ReadReg(LSM6DSL_ACC_GYRO_SENSOR_SYNC_TIME, (uint8_t *)value, 1) )
    return MEMS_ERROR;

  *value &= LSM6DSL_ACC_GYRO_TPH_MASK; //coerce
  *value = *value >> LSM6DSL_ACC_GYRO_TPH_POSITION; //mask

  return MEMS_SUCCESS;
}

/*******************************************************************************
* Function Name  : LSM6DSL_ACC_GYRO_W_FIFO_Watermark
* Description    : Write WTM_FIFO
* Input          : uint16_t
* Output         : None
* Return         : Status [MEMS_ERROR, MEMS_SUCCESS]
*******************************************************************************/
mems_status_t  LSM6DSL_ACC_GYRO_W_FIFO_Watermark(uint16_t newValue)
{
  uint8_t valueH, valueL;
  uint8_t value;

  valueL = newValue & 0xFF;
  valueH = (newValue >> 8) & 0xFF;

  /* Low part goes in FIFO_CTRL1 */
  valueL = valueL << LSM6DSL_ACC_GYRO_WTM_FIFO_CTRL1_POSITION; //mask
  valueL &= LSM6DSL_ACC_GYRO_WTM_FIFO_CTRL1_MASK; //coerce

  if( !LSM6DSL_ACC_GYRO_ReadReg(LSM6DSL_ACC_GYRO_FIFO_CTRL1, &value, 1) )
    return MEMS_ERROR;

  value &= (uint8_t)~LSM6DSL_ACC_GYRO_WTM_FIFO_CTRL1_MASK;
  value |= valueL;

  if( !LSM6DSL_ACC_GYRO_WriteReg(LSM6DSL_ACC_GYRO_FIFO_CTRL1, &value, 1) )
    return MEMS_ERROR;

  /* High part goes in FIFO_CTRL2 */
  valueH = valueH << LSM6DSL_ACC_GYRO_WTM_FIFO_CTRL2_POSITION; //mask
  valueH &= LSM6DSL_ACC_GYRO_WTM_FIFO_CTRL2_MASK; //coerce

  if( !LSM6DSL_ACC_GYRO_ReadReg(LSM6DSL_ACC_GYRO_FIFO_CTRL2, &value, 1) )
    return MEMS_ERROR;

  value &= ~LSM6DSL_ACC_GYRO_WTM_FIFO_CTRL2_MASK;
  value |= valueH;

  if( !LSM6DSL_ACC_GYRO_WriteReg(LSM6DSL_ACC_GYRO_FIFO_CTRL2, &value, 1) )
    return MEMS_ERROR;

  return MEMS_SUCCESS;
}

/*******************************************************************************
* Function Name  : LSM6DSL_ACC_GYRO_R_FIFO_Watermark
* Description    : Read WTM_FIFO
* Input          : Pointer to uint16_t
* Output         : Status of WTM_FIFO
* Return         : Status [MEMS_ERROR, MEMS_SUCCESS]
*******************************************************************************/
mems_status_t LSM6DSL_ACC_GYRO_R_FIFO_Watermark(uint16_t *value)
{
  uint8_t valueH, valueL;

  /* Low part from FIFO_CTRL1 */
 if( !LSM6DSL_ACC_GYRO_ReadReg(LSM6DSL_ACC_GYRO_FIFO_CTRL1, (uint8_t *)&valueL, 1) )
    return MEMS_ERROR;

  valueL &= LSM6DSL_ACC_GYRO_WTM_FIFO_CTRL1_MASK; //coerce
  valueL = valueL >> LSM6DSL_ACC_GYRO_WTM_FIFO_CTRL1_POSITION; //mask

  /* High part from FIFO_CTRL2 */
 if( !LSM6DSL_ACC_GYRO_ReadReg(LSM6DSL_ACC_GYRO_FIFO_CTRL2, (uint8_t *)&valueH, 1) )
    return MEMS_ERROR;

  valueH &= LSM6DSL_ACC_GYRO_WTM_FIFO_CTRL2_MASK; //coerce
  valueH = valueH >> LSM6DSL_ACC_GYRO_WTM_FIFO_CTRL2_POSITION; //mask

  *value = ((valueH << 8) & 0xFF00) | valueL;

  return MEMS_SUCCESS;
}

/*******************************************************************************
* Function Name  : LSM6DSL_ACC_GYRO_W_FIFO_TEMP
* Description    : Write FIFO_TEMP_EN
* Input          : LSM6DSL_ACC_GYRO_FIFO_TEMP_t
* Output         : None
* Return         : Status [MEMS_ERROR, MEMS_SUCCESS]
*******************************************************************************/
mems_status_t  LSM6DSL_ACC_GYRO_W_FIFO_TEMP(LSM6DSL_ACC_GYRO_FIFO_TEMP_t newValue)
{
  uint8_t value;

  if( !LSM6DSL_ACC_GYRO_ReadReg(LSM6DSL_ACC_GYRO_FIFO_CTRL2, &value, 1) )
    return MEMS_ERROR;

  value &= ~LSM6DSL_ACC_GYRO_FIFO_TEMP_MASK;
  value |= newValue;

  if( !LSM6DSL_ACC_GYRO_WriteReg(LSM6DSL_ACC_GYRO_FIFO_CTRL2, &value, 1) )
    return MEMS_ERROR;

  return MEMS_SUCCESS;
}

/*******************************************************************************
* Function Name  : LSM6DSL_ACC_GYRO_R_FIFO_TEMP
* Description    : Read FIFO_TEMP_EN
* Input          : Pointer to LSM6DSL_ACC_GYRO_FIFO_TEMP_t
* Output         : Status of FIFO_TEMP_EN see LSM6DSL_ACC_GYRO_FIFO_TEMP_t
* Return         : Status [MEMS_ERROR, MEMS_SUCCESS]
*******************************************************************************/
mems_status_t LSM6DSL_ACC_GYRO_R_FIFO_TEMP(LSM6DSL_ACC_GYRO_FIFO_TEMP_t *value)
{
 if( !LSM6DSL_ACC_GYRO_ReadReg(LSM6DSL_ACC_GYRO_FIFO_CTRL2, (uint8_t *)value, 1) )
    return MEMS_ERROR;

  *value &= LSM6DSL_ACC_GYRO_FIFO_TEMP_MASK; //mask

  return MEMS_SUCCESS;
}

/*******************************************************************************
* Function Name  : LSM6DSL_ACC_GYRO_W_TIM_PEDO_FIFO_Write_En
* Description    : Write TIM_PEDO_FIFO_DRDY
* Input          : LSM6DSL_ACC_GYRO_TIM_PEDO_FIFO_DRDY_t
* Output         : None
* Return         : Status [MEMS_ERROR, MEMS_SUCCESS]
*******************************************************************************/
mems_status_t  LSM6DSL_ACC_GYRO_W_TIM_PEDO_FIFO_Write_En(LSM6DSL_ACC_GYRO_TIM_PEDO_FIFO_DRDY_t newValue)
{
  uint8_t value;

  if( !LSM6DSL_ACC_GYRO_ReadReg(LSM6DSL_ACC_GYRO_FIFO_CTRL2, &value, 1) )
    return MEMS_ERROR;

  value &= ~LSM6DSL_ACC_GYRO_TIM_PEDO_FIFO_DRDY_MASK;
  value |= newValue;

  if( !LSM6DSL_ACC_GYRO_WriteReg(LSM6DSL_ACC_GYRO_FIFO_CTRL2, &value, 1) )
    return MEMS_ERROR;

  return MEMS_SUCCESS;
}

/*******************************************************************************
* Function Name  : LSM6DSL_ACC_GYRO_R_TIM_PEDO_FIFO_Write_En
* Description    : Read TIM_PEDO_FIFO_DRDY
* Input          : Pointer to LSM6DSL_ACC_GYRO_TIM_PEDO_FIFO_DRDY_t
* Output         : Status of TIM_PEDO_FIFO_DRDY see LSM6DSL_ACC_GYRO_TIM_PEDO_FIFO_DRDY_t
* Return         : Status [MEMS_ERROR, MEMS_SUCCESS]
*******************************************************************************/
mems_status_t LSM6DSL_ACC_GYRO_R_TIM_PEDO_FIFO_Write_En(LSM6DSL_ACC_GYRO_TIM_PEDO_FIFO_DRDY_t *value)
{
 if( !LSM6DSL_ACC_GYRO_ReadReg(LSM6DSL_ACC_GYRO_FIFO_CTRL2, (uint8_t *)value, 1) )
    return MEMS_ERROR;

  *value &= LSM6DSL_ACC_GYRO_TIM_PEDO_FIFO_DRDY_MASK; //mask

  return MEMS_SUCCESS;
}

/*******************************************************************************
* Function Name  : LSM6DSL_ACC_GYRO_W_TIM_PEDO_FIFO_En
* Description    : Write TIM_PEDO_FIFO_EN
* Input          : LSM6DSL_ACC_GYRO_TIM_PEDO_FIFO_EN_t
* Output         : None
* Return         : Status [MEMS_ERROR, MEMS_SUCCESS]
*******************************************************************************/
mems_status_t  LSM6DSL_ACC_GYRO_W_TIM_PEDO_FIFO_En(LSM6DSL_ACC_GYRO_TIM_PEDO_FIFO_EN_t newValue)
{
  uint8_t value;

  if( !LSM6DSL_ACC_GYRO_ReadReg(LSM6DSL_ACC_GYRO_FIFO_CTRL2, &value, 1) )
    return MEMS_ERROR;

  value &= ~LSM6DSL_ACC_GYRO_TIM_PEDO_FIFO_EN_MASK;
  value |= newValue;

  if( !LSM6DSL_ACC_GYRO_WriteReg(LSM6DSL_ACC_GYRO_FIFO_CTRL2, &value, 1) )
    return MEMS_ERROR;

  return MEMS_SUCCESS;
}

/*******************************************************************************
* Function Name  : LSM6DSL_ACC_GYRO_R_TIM_PEDO_FIFO_En
* Description    : Read TIM_PEDO_FIFO_EN
* Input          : Pointer to LSM6DSL_ACC_GYRO_TIM_PEDO_FIFO_EN_t
* Output         : Status of TIM_PEDO_FIFO_EN see LSM6DSL_ACC_GYRO_TIM_PEDO_FIFO_EN_t
* Return         : Status [MEMS_ERROR, MEMS_SUCCESS]
*******************************************************************************/
mems_status_t LSM6DSL_ACC_GYRO_R_TIM_PEDO_FIFO_En(LSM6DSL_ACC_GYRO_TIM_PEDO_FIFO_EN_t *value)
{
 if( !LSM6DSL_ACC_GYRO_ReadReg(LSM6DSL_ACC_GYRO_FIFO_CTRL2, (uint8_t *)value, 1) )
    return MEMS_ERROR;

  *value &= LSM6DSL_ACC_GYRO_TIM_PEDO_FIFO_EN_MASK; //mask

  return MEMS_SUCCESS;
}
/*******************************************************************************
* Function Name  : LSM6DSL_ACC_GYRO_W_DEC_FIFO_XL
* Description    : Write DEC_FIFO_XL
* Input          : LSM6DSL_ACC_GYRO_DEC_FIFO_XL_t
* Output         : None
* Return         : Status [MEMS_ERROR, MEMS_SUCCESS]
*******************************************************************************/
mems_status_t  LSM6DSL_ACC_GYRO_W_DEC_FIFO_XL(LSM6DSL_ACC_GYRO_DEC_FIFO_XL_t newValue)
{
  uint8_t value;

  if( !LSM6DSL_ACC_GYRO_ReadReg(LSM6DSL_ACC_GYRO_FIFO_CTRL3, &value, 1) )
    return MEMS_ERROR;

  value &= ~LSM6DSL_ACC_GYRO_DEC_FIFO_XL_MASK;
  value |= newValue;

  if( !LSM6DSL_ACC_GYRO_WriteReg(LSM6DSL_ACC_GYRO_FIFO_CTRL3, &value, 1) )
    return MEMS_ERROR;

  return MEMS_SUCCESS;
}

/*******************************************************************************
* Function Name  : LSM6DSL_ACC_GYRO_W_DEC_FIFO_XL_val
* Description    : Write DEC_FIFO_XL
* Input          : uint16_t
* Output         : Program XL decimation value from unsigned short
* Return         : Status [MEMS_ERROR, MEMS_SUCCESS]
*******************************************************************************/
mems_status_t  LSM6DSL_ACC_GYRO_W_DEC_FIFO_XL_val(uint16_t newValue)
{
  switch(newValue) {
  case 0:
    LSM6DSL_ACC_GYRO_W_DEC_FIFO_XL(LSM6DSL_ACC_GYRO_DEC_FIFO_XL_DATA_NOT_IN_FIFO);
    break;

  case 1:
    LSM6DSL_ACC_GYRO_W_DEC_FIFO_XL(LSM6DSL_ACC_GYRO_DEC_FIFO_XL_NO_DECIMATION);
    break;

  case 2:
    LSM6DSL_ACC_GYRO_W_DEC_FIFO_XL(LSM6DSL_ACC_GYRO_DEC_FIFO_XL_DECIMATION_BY_2);
    break;

  case 3:
    LSM6DSL_ACC_GYRO_W_DEC_FIFO_XL(LSM6DSL_ACC_GYRO_DEC_FIFO_XL_DECIMATION_BY_3);
    break;

  case 4:
    LSM6DSL_ACC_GYRO_W_DEC_FIFO_XL(LSM6DSL_ACC_GYRO_DEC_FIFO_XL_DECIMATION_BY_4);
    break;

  case 8:
    LSM6DSL_ACC_GYRO_W_DEC_FIFO_XL(LSM6DSL_ACC_GYRO_DEC_FIFO_XL_DECIMATION_BY_8);
    break;

  case 16:
    LSM6DSL_ACC_GYRO_W_DEC_FIFO_XL(LSM6DSL_ACC_GYRO_DEC_FIFO_XL_DECIMATION_BY_16);
    break;

  case 32:
    LSM6DSL_ACC_GYRO_W_DEC_FIFO_XL(LSM6DSL_ACC_GYRO_DEC_FIFO_XL_DECIMATION_BY_32);
    break;

  default:
    return MEMS_ERROR;
  }

  return MEMS_SUCCESS;
}

/*******************************************************************************
* Function Name  : LSM6DSL_ACC_GYRO_R_DEC_FIFO_XL
* Description    : Read DEC_FIFO_XL
* Input          : Pointer to LSM6DSL_ACC_GYRO_DEC_FIFO_XL_t
* Output         : Status of DEC_FIFO_XL see LSM6DSL_ACC_GYRO_DEC_FIFO_XL_t
* Return         : Status [MEMS_ERROR, MEMS_SUCCESS]
*******************************************************************************/
mems_status_t LSM6DSL_ACC_GYRO_R_DEC_FIFO_XL(LSM6DSL_ACC_GYRO_DEC_FIFO_XL_t *value)
{
 if( !LSM6DSL_ACC_GYRO_ReadReg(LSM6DSL_ACC_GYRO_FIFO_CTRL3, (uint8_t *)value, 1) )
    return MEMS_ERROR;

  *value &= LSM6DSL_ACC_GYRO_DEC_FIFO_XL_MASK; //mask

  return MEMS_SUCCESS;
}

/*******************************************************************************
* Function Name  : LSM6DSL_ACC_GYRO_W_DEC_FIFO_G
* Description    : Write DEC_FIFO_G
* Input          : LSM6DSL_ACC_GYRO_DEC_FIFO_G_t
* Output         : None
* Return         : Status [MEMS_ERROR, MEMS_SUCCESS]
*******************************************************************************/
mems_status_t  LSM6DSL_ACC_GYRO_W_DEC_FIFO_G(LSM6DSL_ACC_GYRO_DEC_FIFO_G_t newValue)
{
  uint8_t value;

  if( !LSM6DSL_ACC_GYRO_ReadReg(LSM6DSL_ACC_GYRO_FIFO_CTRL3, &value, 1))
    return MEMS_ERROR;

  value &= ~LSM6DSL_ACC_GYRO_DEC_FIFO_G_MASK;
  value |= newValue;

  if( !LSM6DSL_ACC_GYRO_WriteReg(LSM6DSL_ACC_GYRO_FIFO_CTRL3, &value, 1) )
    return MEMS_ERROR;

  return MEMS_SUCCESS;
}

/*******************************************************************************
* Function Name  : LSM6DSL_ACC_GYRO_W_DEC_FIFO_G_val
* Description    : Write DEC_FIFO_G
* Input          : uint16_t
* Output         : Program G decimation value from unsigned short
* Return         : Status [MEMS_ERROR, MEMS_SUCCESS]
*******************************************************************************/
mems_status_t  LSM6DSL_ACC_GYRO_W_DEC_FIFO_G_val(uint16_t newValue)
{
  switch(newValue) {
  case 0:
    LSM6DSL_ACC_GYRO_W_DEC_FIFO_G(LSM6DSL_ACC_GYRO_DEC_FIFO_G_DATA_NOT_IN_FIFO);
    break;

  case 1:
    LSM6DSL_ACC_GYRO_W_DEC_FIFO_G(LSM6DSL_ACC_GYRO_DEC_FIFO_G_NO_DECIMATION);
    break;

  case 2:
    LSM6DSL_ACC_GYRO_W_DEC_FIFO_G(LSM6DSL_ACC_GYRO_DEC_FIFO_G_DECIMATION_BY_2);
    break;

  case 3:
    LSM6DSL_ACC_GYRO_W_DEC_FIFO_G(LSM6DSL_ACC_GYRO_DEC_FIFO_G_DECIMATION_BY_3);
    break;

  case 4:
    LSM6DSL_ACC_GYRO_W_DEC_FIFO_G(LSM6DSL_ACC_GYRO_DEC_FIFO_G_DECIMATION_BY_4);
    break;

  case 8:
    LSM6DSL_ACC_GYRO_W_DEC_FIFO_G(LSM6DSL_ACC_GYRO_DEC_FIFO_G_DECIMATION_BY_8);
    break;

  case 16:
    LSM6DSL_ACC_GYRO_W_DEC_FIFO_G(LSM6DSL_ACC_GYRO_DEC_FIFO_G_DECIMATION_BY_16);
    break;

  case 32:
    LSM6DSL_ACC_GYRO_W_DEC_FIFO_G(LSM6DSL_ACC_GYRO_DEC_FIFO_G_DECIMATION_BY_32);
    break;

  default:
    return MEMS_ERROR;
  }

  return MEMS_SUCCESS;
}

/*******************************************************************************
* Function Name  : LSM6DSL_ACC_GYRO_R_DEC_FIFO_G
* Description    : Read DEC_FIFO_G
* Input          : Pointer to LSM6DSL_ACC_GYRO_DEC_FIFO_G_t
* Output         : Status of DEC_FIFO_G see LSM6DSL_ACC_GYRO_DEC_FIFO_G_t
* Return         : Status [MEMS_ERROR, MEMS_SUCCESS]
*******************************************************************************/
mems_status_t LSM6DSL_ACC_GYRO_R_DEC_FIFO_G(LSM6DSL_ACC_GYRO_DEC_FIFO_G_t *value)
{
 if( !LSM6DSL_ACC_GYRO_ReadReg(LSM6DSL_ACC_GYRO_FIFO_CTRL3, (uint8_t *)value, 1))
    return MEMS_ERROR;

  *value &= LSM6DSL_ACC_GYRO_DEC_FIFO_G_MASK; //mask

  return MEMS_SUCCESS;
}

/*******************************************************************************
* Function Name  : LSM6DSL_ACC_GYRO_W_DEC_FIFO_DS3
* Description    : Write DEC_DS3_FIFO
* Input          : LSM6DSL_ACC_GYRO_DEC_FIFO_DS3_t
* Output         : None
* Return         : Status [MEMS_ERROR, MEMS_SUCCESS]
*******************************************************************************/
mems_status_t  LSM6DSL_ACC_GYRO_W_DEC_FIFO_DS3(LSM6DSL_ACC_GYRO_DEC_FIFO_DS3_t newValue)
{
  uint8_t value;

  if( !LSM6DSL_ACC_GYRO_ReadReg(LSM6DSL_ACC_GYRO_FIFO_CTRL4, &value, 1))
    return MEMS_ERROR;

  value &= ~LSM6DSL_ACC_GYRO_DEC_FIFO_DS3_MASK;
  value |= newValue;

  if( !LSM6DSL_ACC_GYRO_WriteReg(LSM6DSL_ACC_GYRO_FIFO_CTRL4, &value, 1) )
    return MEMS_ERROR;

  return MEMS_SUCCESS;
}

/*******************************************************************************
* Function Name  : LSM6DSL_ACC_GYRO_R_DEC_FIFO_DS3
* Description    : Read DEC_DS3_FIFO
* Input          : Pointer to LSM6DSL_ACC_GYRO_DEC_FIFO_DS3_t
* Output         : Status of DEC_DS3_FIFO see LSM6DSL_ACC_GYRO_DEC_FIFO_DS3_t
* Return         : Status [MEMS_ERROR, MEMS_SUCCESS]
*******************************************************************************/
mems_status_t LSM6DSL_ACC_GYRO_R_DEC_FIFO_DS3(LSM6DSL_ACC_GYRO_DEC_FIFO_DS3_t *value)
{
 if( !LSM6DSL_ACC_GYRO_ReadReg(LSM6DSL_ACC_GYRO_FIFO_CTRL4, (uint8_t *)value, 1))
    return MEMS_ERROR;

  *value &= LSM6DSL_ACC_GYRO_DEC_FIFO_DS3_MASK; //mask

  return MEMS_SUCCESS;
}

/*******************************************************************************
* Function Name  : LSM6DSL_ACC_GYRO_W_DEC_FIFO_DS4
* Description    : Write DEC_DS4_FIFO
* Input          : LSM6DSL_ACC_GYRO_DEC_FIFO_DS4_t
* Output         : None
* Return         : Status [MEMS_ERROR, MEMS_SUCCESS]
*******************************************************************************/
mems_status_t  LSM6DSL_ACC_GYRO_W_DEC_FIFO_DS4(LSM6DSL_ACC_GYRO_DEC_FIFO_DS4_t newValue)
{
  uint8_t value;

  if( !LSM6DSL_ACC_GYRO_ReadReg(LSM6DSL_ACC_GYRO_FIFO_CTRL4, &value, 1))
    return MEMS_ERROR;

  value &= ~LSM6DSL_ACC_GYRO_DEC_FIFO_DS4_MASK;
  value |= newValue;

  if( !LSM6DSL_ACC_GYRO_WriteReg(LSM6DSL_ACC_GYRO_FIFO_CTRL4, &value, 1) )
    return MEMS_ERROR;

  return MEMS_SUCCESS;
}

/*******************************************************************************
* Function Name  : LSM6DSL_ACC_GYRO_R_DEC_FIFO_DS4
* Description    : Read DEC_DS4_FIFO
* Input          : Pointer to LSM6DSL_ACC_GYRO_DEC_FIFO_DS4_t
* Output         : Status of DEC_DS4_FIFO see LSM6DSL_ACC_GYRO_DEC_FIFO_DS4_t
* Return         : Status [MEMS_ERROR, MEMS_SUCCESS]
*******************************************************************************/
mems_status_t LSM6DSL_ACC_GYRO_R_DEC_FIFO_DS4(LSM6DSL_ACC_GYRO_DEC_FIFO_DS4_t *value)
{
 if( !LSM6DSL_ACC_GYRO_ReadReg(LSM6DSL_ACC_GYRO_FIFO_CTRL4, (uint8_t *)value, 1))
    return MEMS_ERROR;

  *value &= LSM6DSL_ACC_GYRO_DEC_FIFO_DS4_MASK; //mask

  return MEMS_SUCCESS;
}

/*******************************************************************************
* Function Name  : LSM6DSL_ACC_GYRO_W_HI_DATA_ONLY
* Description    : Write HI_DATA_ONLY
* Input          : LSM6DSL_ACC_GYRO_HI_DATA_ONLY_t
* Output         : None
* Return         : Status [MEMS_ERROR, MEMS_SUCCESS]
*******************************************************************************/
mems_status_t  LSM6DSL_ACC_GYRO_W_HI_DATA_ONLY(LSM6DSL_ACC_GYRO_HI_DATA_ONLY_t newValue)
{
  uint8_t value;

  if( !LSM6DSL_ACC_GYRO_ReadReg(LSM6DSL_ACC_GYRO_FIFO_CTRL4, &value, 1))
    return MEMS_ERROR;

  value &= ~LSM6DSL_ACC_GYRO_HI_DATA_ONLY_MASK;
  value |= newValue;

  if( !LSM6DSL_ACC_GYRO_WriteReg(LSM6DSL_ACC_GYRO_FIFO_CTRL4, &value, 1) )
    return MEMS_ERROR;

  return MEMS_SUCCESS;
}

/*******************************************************************************
* Function Name  : LSM6DSL_ACC_GYRO_R_HI_DATA_ONLY
* Description    : Read HI_DATA_ONLY
* Input          : Pointer to LSM6DSL_ACC_GYRO_HI_DATA_ONLY_t
* Output         : Status of HI_DATA_ONLY see LSM6DSL_ACC_GYRO_HI_DATA_ONLY_t
* Return         : Status [MEMS_ERROR, MEMS_SUCCESS]
*******************************************************************************/
mems_status_t LSM6DSL_ACC_GYRO_R_HI_DATA_ONLY(LSM6DSL_ACC_GYRO_HI_DATA_ONLY_t *value)
{
 if( !LSM6DSL_ACC_GYRO_ReadReg(LSM6DSL_ACC_GYRO_FIFO_CTRL4, (uint8_t *)value, 1))
    return MEMS_ERROR;

  *value &= LSM6DSL_ACC_GYRO_HI_DATA_ONLY_MASK; //mask

  return MEMS_SUCCESS;
}

/*******************************************************************************
* Function Name  : LSM6DSL_ACC_GYRO_W_STOP_ON_FTH
* Description    : Write STOP_ON_FTH
* Input          : LSM6DSL_ACC_GYRO_STOP_ON_FTH_t
* Output         : None
* Return         : Status [MEMS_ERROR, MEMS_SUCCESS]
*******************************************************************************/
mems_status_t  LSM6DSL_ACC_GYRO_W_STOP_ON_FTH(LSM6DSL_ACC_GYRO_STOP_ON_FTH_t newValue)
{
  uint8_t value;

  if( !LSM6DSL_ACC_GYRO_ReadReg(LSM6DSL_ACC_GYRO_FIFO_CTRL4, &value, 1))
    return MEMS_ERROR;

  value &= ~LSM6DSL_ACC_GYRO_STOP_ON_FTH_MASK;
  value |= newValue;

  if( !LSM6DSL_ACC_GYRO_WriteReg(LSM6DSL_ACC_GYRO_FIFO_CTRL4, &value, 1) )
    return MEMS_ERROR;

  return MEMS_SUCCESS;
}

/*******************************************************************************
* Function Name  : LSM6DSL_ACC_GYRO_R_STOP_ON_FTH
* Description    : Read STOP_ON_FTH
* Input          : Pointer to LSM6DSL_ACC_GYRO_STOP_ON_FTH_t
* Output         : Status of STOP_ON_FTH see LSM6DSL_ACC_GYRO_STOP_ON_FTH_t
* Return         : Status [MEMS_ERROR, MEMS_SUCCESS]
*******************************************************************************/
mems_status_t LSM6DSL_ACC_GYRO_R_STOP_ON_FTH(LSM6DSL_ACC_GYRO_STOP_ON_FTH_t *value)
{
 if( !LSM6DSL_ACC_GYRO_ReadReg(LSM6DSL_ACC_GYRO_FIFO_CTRL4, (uint8_t *)value, 1))
    return MEMS_ERROR;

  *value &= LSM6DSL_ACC_GYRO_STOP_ON_FTH_MASK; //mask

  return MEMS_SUCCESS;
}

/*******************************************************************************
* Function Name  : LSM6DSL_ACC_GYRO_W_FIFO_MODE
* Description    : Write FIFO_MODE
* Input          : LSM6DSL_ACC_GYRO_FIFO_MODE_t
* Output         : None
* Return         : Status [MEMS_ERROR, MEMS_SUCCESS]
*******************************************************************************/
mems_status_t  LSM6DSL_ACC_GYRO_W_FIFO_MODE(LSM6DSL_ACC_GYRO_FIFO_MODE_t newValue)
{
  uint8_t value;

  if( !LSM6DSL_ACC_GYRO_ReadReg(LSM6DSL_ACC_GYRO_FIFO_CTRL5, &value, 1))
    return MEMS_ERROR;

  value &= ~LSM6DSL_ACC_GYRO_FIFO_MODE_MASK;
  value |= newValue;

  if( !LSM6DSL_ACC_GYRO_WriteReg(LSM6DSL_ACC_GYRO_FIFO_CTRL5, &value, 1) )
    return MEMS_ERROR;

  return MEMS_SUCCESS;
}

/*******************************************************************************
* Function Name  : LSM6DSL_ACC_GYRO_R_FIFO_MODE
* Description    : Read FIFO_MODE
* Input          : Pointer to LSM6DSL_ACC_GYRO_FIFO_MODE_t
* Output         : Status of FIFO_MODE see LSM6DSL_ACC_GYRO_FIFO_MODE_t
* Return         : Status [MEMS_ERROR, MEMS_SUCCESS]
*******************************************************************************/
mems_status_t LSM6DSL_ACC_GYRO_R_FIFO_MODE(LSM6DSL_ACC_GYRO_FIFO_MODE_t *value)
{
 if( !LSM6DSL_ACC_GYRO_ReadReg(LSM6DSL_ACC_GYRO_FIFO_CTRL5, (uint8_t *)value, 1))
    return MEMS_ERROR;

  *value &= LSM6DSL_ACC_GYRO_FIFO_MODE_MASK; //mask

  return MEMS_SUCCESS;
}

/*******************************************************************************
* Function Name  : LSM6DSL_ACC_GYRO_W_ODR_FIFO
* Description    : Write ODR_FIFO
* Input          : LSM6DSL_ACC_GYRO_ODR_FIFO_t
* Output         : None
* Return         : Status [MEMS_ERROR, MEMS_SUCCESS]
*******************************************************************************/
mems_status_t  LSM6DSL_ACC_GYRO_W_ODR_FIFO(LSM6DSL_ACC_GYRO_ODR_FIFO_t newValue)
{
  uint8_t value;

  if( !LSM6DSL_ACC_GYRO_ReadReg(LSM6DSL_ACC_GYRO_FIFO_CTRL5, &value, 1))
    return MEMS_ERROR;

  value &= ~LSM6DSL_ACC_GYRO_ODR_FIFO_MASK;
  value |= newValue;

  if( !LSM6DSL_ACC_GYRO_WriteReg(LSM6DSL_ACC_GYRO_FIFO_CTRL5, &value, 1) )
    return MEMS_ERROR;

  return MEMS_SUCCESS;
}

/*******************************************************************************
* Function Name  : LSM6DSL_ACC_GYRO_R_ODR_FIFO
* Description    : Read ODR_FIFO
* Input          : Pointer to LSM6DSL_ACC_GYRO_ODR_FIFO_t
* Output         : Status of ODR_FIFO see LSM6DSL_ACC_GYRO_ODR_FIFO_t
* Return         : Status [MEMS_ERROR, MEMS_SUCCESS]
*******************************************************************************/
mems_status_t LSM6DSL_ACC_GYRO_R_ODR_FIFO(LSM6DSL_ACC_GYRO_ODR_FIFO_t *value)
{
 if( !LSM6DSL_ACC_GYRO_ReadReg(LSM6DSL_ACC_GYRO_FIFO_CTRL5, (uint8_t *)value, 1))
    return MEMS_ERROR;

  *value &= LSM6DSL_ACC_GYRO_ODR_FIFO_MASK; //mask

  return MEMS_SUCCESS;
}

/*******************************************************************************
* Function Name  : LSM6DSL_ACC_GYRO_W_DRDY_PULSE
* Description    : Write DRDY_PULSE
* Input          : LSM6DSL_ACC_GYRO_DRDY_PULSE_t
* Output         : None
* Return         : Status [MEMS_ERROR, MEMS_SUCCESS]
*******************************************************************************/
mems_status_t  LSM6DSL_ACC_GYRO_W_DRDY_PULSE(LSM6DSL_ACC_GYRO_DRDY_PULSE_t newValue)
{
  uint8_t value;

  if( !LSM6DSL_ACC_GYRO_ReadReg(LSM6DSL_ACC_GYRO_DRDY_PULSE_CFG_G, &value, 1))
    return MEMS_ERROR;

  value &= ~LSM6DSL_ACC_GYRO_DRDY_PULSE_MASK;
  value |= newValue;

  if( !LSM6DSL_ACC_GYRO_WriteReg(LSM6DSL_ACC_GYRO_DRDY_PULSE_CFG_G, &value, 1) )
    return MEMS_ERROR;

  return MEMS_SUCCESS;
}

/*******************************************************************************
* Function Name  : LSM6DSL_ACC_GYRO_R_DRDY_PULSE
* Description    : Read DRDY_PULSE
* Input          : Pointer to LSM6DSL_ACC_GYRO_DRDY_PULSE_t
* Output         : Status of DRDY_PULSE see LSM6DSL_ACC_GYRO_DRDY_PULSE_t
* Return         : Status [MEMS_ERROR, MEMS_SUCCESS]
*******************************************************************************/
mems_status_t LSM6DSL_ACC_GYRO_R_DRDY_PULSE(LSM6DSL_ACC_GYRO_DRDY_PULSE_t *value)
{
 if( !LSM6DSL_ACC_GYRO_ReadReg(LSM6DSL_ACC_GYRO_DRDY_PULSE_CFG_G, (uint8_t *)value, 1))
    return MEMS_ERROR;

  *value &= LSM6DSL_ACC_GYRO_DRDY_PULSE_MASK; //mask

  return MEMS_SUCCESS;
}

/*******************************************************************************
* Function Name  : LSM6DSL_ACC_GYRO_W_DRDY_XL_on_INT1
* Description    : Write INT1_DRDY_XL
* Input          : LSM6DSL_ACC_GYRO_INT1_DRDY_XL_t
* Output         : None
* Return         : Status [MEMS_ERROR, MEMS_SUCCESS]
*******************************************************************************/
mems_status_t  LSM6DSL_ACC_GYRO_W_DRDY_XL_on_INT1(LSM6DSL_ACC_GYRO_INT1_DRDY_XL_t newValue)
{
  uint8_t value;

  if( !LSM6DSL_ACC_GYRO_ReadReg(LSM6DSL_ACC_GYRO_INT1_CTRL, &value, 1))
    return MEMS_ERROR;

  value &= ~LSM6DSL_ACC_GYRO_INT1_DRDY_XL_MASK;
  value |= newValue;

  if( !LSM6DSL_ACC_GYRO_WriteReg(LSM6DSL_ACC_GYRO_INT1_CTRL, &value, 1) )
    return MEMS_ERROR;

  return MEMS_SUCCESS;
}

/*******************************************************************************
* Function Name  : LSM6DSL_ACC_GYRO_R_DRDY_XL_on_INT1
* Description    : Read INT1_DRDY_XL
* Input          : Pointer to LSM6DSL_ACC_GYRO_INT1_DRDY_XL_t
* Output         : Status of INT1_DRDY_XL see LSM6DSL_ACC_GYRO_INT1_DRDY_XL_t
* Return         : Status [MEMS_ERROR, MEMS_SUCCESS]
*******************************************************************************/
mems_status_t LSM6DSL_ACC_GYRO_R_DRDY_XL_on_INT1(LSM6DSL_ACC_GYRO_INT1_DRDY_XL_t *value)
{
 if( !LSM6DSL_ACC_GYRO_ReadReg(LSM6DSL_ACC_GYRO_INT1_CTRL, (uint8_t *)value, 1))
    return MEMS_ERROR;

  *value &= LSM6DSL_ACC_GYRO_INT1_DRDY_XL_MASK; //mask

  return MEMS_SUCCESS;
}

/*******************************************************************************
* Function Name  : LSM6DSL_ACC_GYRO_W_DRDY_G_on_INT1
* Description    : Write INT1_DRDY_G
* Input          : LSM6DSL_ACC_GYRO_INT1_DRDY_G_t
* Output         : None
* Return         : Status [MEMS_ERROR, MEMS_SUCCESS]
*******************************************************************************/
mems_status_t  LSM6DSL_ACC_GYRO_W_DRDY_G_on_INT1(LSM6DSL_ACC_GYRO_INT1_DRDY_G_t newValue)
{
  uint8_t value;

  if( !LSM6DSL_ACC_GYRO_ReadReg(LSM6DSL_ACC_GYRO_INT1_CTRL, &value, 1))
    return MEMS_ERROR;

  value &= ~LSM6DSL_ACC_GYRO_INT1_DRDY_G_MASK;
  value |= newValue;

  if( !LSM6DSL_ACC_GYRO_WriteReg(LSM6DSL_ACC_GYRO_INT1_CTRL, &value, 1) )
    return MEMS_ERROR;

  return MEMS_SUCCESS;
}

/*******************************************************************************
* Function Name  : LSM6DSL_ACC_GYRO_R_DRDY_G_on_INT1
* Description    : Read INT1_DRDY_G
* Input          : Pointer to LSM6DSL_ACC_GYRO_INT1_DRDY_G_t
* Output         : Status of INT1_DRDY_G see LSM6DSL_ACC_GYRO_INT1_DRDY_G_t
* Return         : Status [MEMS_ERROR, MEMS_SUCCESS]
*******************************************************************************/
mems_status_t LSM6DSL_ACC_GYRO_R_DRDY_G_on_INT1(LSM6DSL_ACC_GYRO_INT1_DRDY_G_t *value)
{
 if( !LSM6DSL_ACC_GYRO_ReadReg(LSM6DSL_ACC_GYRO_INT1_CTRL, (uint8_t *)value, 1))
    return MEMS_ERROR;

  *value &= LSM6DSL_ACC_GYRO_INT1_DRDY_G_MASK; //mask

  return MEMS_SUCCESS;
}

/*******************************************************************************
* Function Name  : LSM6DSL_ACC_GYRO_W_BOOT_on_INT1
* Description    : Write INT1_BOOT
* Input          : LSM6DSL_ACC_GYRO_INT1_BOOT_t
* Output         : None
* Return         : Status [MEMS_ERROR, MEMS_SUCCESS]
*******************************************************************************/
mems_status_t  LSM6DSL_ACC_GYRO_W_BOOT_on_INT1(LSM6DSL_ACC_GYRO_INT1_BOOT_t newValue)
{
  uint8_t value;

  if( !LSM6DSL_ACC_GYRO_ReadReg(LSM6DSL_ACC_GYRO_INT1_CTRL, &value, 1))
    return MEMS_ERROR;

  value &= ~LSM6DSL_ACC_GYRO_INT1_BOOT_MASK;
  value |= newValue;

  if( !LSM6DSL_ACC_GYRO_WriteReg(LSM6DSL_ACC_GYRO_INT1_CTRL, &value, 1) )
    return MEMS_ERROR;

  return MEMS_SUCCESS;
}

/*******************************************************************************
* Function Name  : LSM6DSL_ACC_GYRO_R_BOOT_on_INT1
* Description    : Read INT1_BOOT
* Input          : Pointer to LSM6DSL_ACC_GYRO_INT1_BOOT_t
* Output         : Status of INT1_BOOT see LSM6DSL_ACC_GYRO_INT1_BOOT_t
* Return         : Status [MEMS_ERROR, MEMS_SUCCESS]
*******************************************************************************/
mems_status_t LSM6DSL_ACC_GYRO_R_BOOT_on_INT1(LSM6DSL_ACC_GYRO_INT1_BOOT_t *value)
{
 if( !LSM6DSL_ACC_GYRO_ReadReg(LSM6DSL_ACC_GYRO_INT1_CTRL, (uint8_t *)value, 1))
    return MEMS_ERROR;

  *value &= LSM6DSL_ACC_GYRO_INT1_BOOT_MASK; //mask

  return MEMS_SUCCESS;
}

/*******************************************************************************
* Function Name  : LSM6DSL_ACC_GYRO_W_FIFO_TSHLD_on_INT1
* Description    : Write INT1_FTH
* Input          : LSM6DSL_ACC_GYRO_INT1_FTH_t
* Output         : None
* Return         : Status [MEMS_ERROR, MEMS_SUCCESS]
*******************************************************************************/
mems_status_t  LSM6DSL_ACC_GYRO_W_FIFO_TSHLD_on_INT1(LSM6DSL_ACC_GYRO_INT1_FTH_t newValue)
{
  uint8_t value;

  if( !LSM6DSL_ACC_GYRO_ReadReg(LSM6DSL_ACC_GYRO_INT1_CTRL, &value, 1) )
    return MEMS_ERROR;

  value &= ~LSM6DSL_ACC_GYRO_INT1_FTH_MASK;
  value |= newValue;

  if( !LSM6DSL_ACC_GYRO_WriteReg(LSM6DSL_ACC_GYRO_INT1_CTRL, &value, 1) )
    return MEMS_ERROR;

  return MEMS_SUCCESS;
}

/*******************************************************************************
* Function Name  : LSM6DSL_ACC_GYRO_R_FIFO_TSHLD_on_INT1
* Description    : Read INT1_FTH
* Input          : Pointer to LSM6DSL_ACC_GYRO_INT1_FTH_t
* Output         : Status of INT1_FTH see LSM6DSL_ACC_GYRO_INT1_FTH_t
* Return         : Status [MEMS_ERROR, MEMS_SUCCESS]
*******************************************************************************/
mems_status_t LSM6DSL_ACC_GYRO_R_FIFO_TSHLD_on_INT1(LSM6DSL_ACC_GYRO_INT1_FTH_t *value)
{
 if( !LSM6DSL_ACC_GYRO_ReadReg(LSM6DSL_ACC_GYRO_INT1_CTRL, (uint8_t *)value, 1))
    return MEMS_ERROR;

  *value &= LSM6DSL_ACC_GYRO_INT1_FTH_MASK; //mask

  return MEMS_SUCCESS;
}

/*******************************************************************************
* Function Name  : LSM6DSL_ACC_GYRO_W_OVERRUN_on_INT1
* Description    : Write INT1_OVR
* Input          : LSM6DSL_ACC_GYRO_INT1_OVR_t
* Output         : None
* Return         : Status [MEMS_ERROR, MEMS_SUCCESS]
*******************************************************************************/
mems_status_t  LSM6DSL_ACC_GYRO_W_OVERRUN_on_INT1(LSM6DSL_ACC_GYRO_INT1_OVR_t newValue)
{
  uint8_t value;

  if( !LSM6DSL_ACC_GYRO_ReadReg(LSM6DSL_ACC_GYRO_INT1_CTRL, &value, 1))
    return MEMS_ERROR;

  value &= ~LSM6DSL_ACC_GYRO_INT1_OVR_MASK;
  value |= newValue;

  if( !LSM6DSL_ACC_GYRO_WriteReg(LSM6DSL_ACC_GYRO_INT1_CTRL, &value, 1))
    return MEMS_ERROR;

  return MEMS_SUCCESS;
}

/*******************************************************************************
* Function Name  : LSM6DSL_ACC_GYRO_R_OVERRUN_on_INT1
* Description    : Read INT1_OVR
* Input          : Pointer to LSM6DSL_ACC_GYRO_INT1_OVR_t
* Output         : Status of INT1_OVR see LSM6DSL_ACC_GYRO_INT1_OVR_t
* Return         : Status [MEMS_ERROR, MEMS_SUCCESS]
*******************************************************************************/
mems_status_t LSM6DSL_ACC_GYRO_R_OVERRUN_on_INT1(LSM6DSL_ACC_GYRO_INT1_OVR_t *value)
{
 if( !LSM6DSL_ACC_GYRO_ReadReg(LSM6DSL_ACC_GYRO_INT1_CTRL, (uint8_t *)value, 1))
    return MEMS_ERROR;

  *value &= LSM6DSL_ACC_GYRO_INT1_OVR_MASK; //mask

  return MEMS_SUCCESS;
}

/*******************************************************************************
* Function Name  : LSM6DSL_ACC_GYRO_W_FULL_FLAG_on_INT1
* Description    : Write INT1_FULL_FLAG
* Input          : LSM6DSL_ACC_GYRO_INT1_FULL_FLAG_t
* Output         : None
* Return         : Status [MEMS_ERROR, MEMS_SUCCESS]
*******************************************************************************/
mems_status_t  LSM6DSL_ACC_GYRO_W_FULL_FLAG_on_INT1(LSM6DSL_ACC_GYRO_INT1_FULL_FLAG_t newValue)
{
  uint8_t value;

  if( !LSM6DSL_ACC_GYRO_ReadReg(LSM6DSL_ACC_GYRO_INT1_CTRL, &value, 1))
    return MEMS_ERROR;

  value &= ~LSM6DSL_ACC_GYRO_INT1_FULL_FLAG_MASK;
  value |= newValue;

  if( !LSM6DSL_ACC_GYRO_WriteReg(LSM6DSL_ACC_GYRO_INT1_CTRL, &value, 1) )
    return MEMS_ERROR;

  return MEMS_SUCCESS;
}

/*******************************************************************************
* Function Name  : LSM6DSL_ACC_GYRO_R_FULL_FLAG_on_INT1
* Description    : Read INT1_FULL_FLAG
* Input          : Pointer to LSM6DSL_ACC_GYRO_INT1_FULL_FLAG_t
* Output         : Status of INT1_FULL_FLAG see LSM6DSL_ACC_GYRO_INT1_FULL_FLAG_t
* Return         : Status [MEMS_ERROR, MEMS_SUCCESS]
*******************************************************************************/
mems_status_t LSM6DSL_ACC_GYRO_R_FULL_FLAG_on_INT1(LSM6DSL_ACC_GYRO_INT1_FULL_FLAG_t *value)
{
 if( !LSM6DSL_ACC_GYRO_ReadReg(LSM6DSL_ACC_GYRO_INT1_CTRL, (uint8_t *)value, 1))
    return MEMS_ERROR;

  *value &= LSM6DSL_ACC_GYRO_INT1_FULL_FLAG_MASK; //mask

  return MEMS_SUCCESS;
}

/*******************************************************************************
* Function Name  : LSM6DSL_ACC_GYRO_W_SIGN_MOT_on_INT1
* Description    : Write INT1_SIGN_MOT
* Input          : LSM6DSL_ACC_GYRO_INT1_SIGN_MOT_t
* Output         : None
* Return         : Status [MEMS_ERROR, MEMS_SUCCESS]
*******************************************************************************/
mems_status_t  LSM6DSL_ACC_GYRO_W_SIGN_MOT_on_INT1(LSM6DSL_ACC_GYRO_INT1_SIGN_MOT_t newValue)
{
  uint8_t value;

  if( !LSM6DSL_ACC_GYRO_ReadReg(LSM6DSL_ACC_GYRO_INT1_CTRL, &value, 1))
    return MEMS_ERROR;

  value &= ~LSM6DSL_ACC_GYRO_INT1_SIGN_MOT_MASK;
  value |= newValue;

  if( !LSM6DSL_ACC_GYRO_WriteReg(LSM6DSL_ACC_GYRO_INT1_CTRL, &value, 1) )
    return MEMS_ERROR;

  return MEMS_SUCCESS;
}

/*******************************************************************************
* Function Name  : LSM6DSL_ACC_GYRO_R_SIGN_MOT_on_INT1
* Description    : Read INT1_SIGN_MOT
* Input          : Pointer to LSM6DSL_ACC_GYRO_INT1_SIGN_MOT_t
* Output         : Status of INT1_SIGN_MOT see LSM6DSL_ACC_GYRO_INT1_SIGN_MOT_t
* Return         : Status [MEMS_ERROR, MEMS_SUCCESS]
*******************************************************************************/
mems_status_t LSM6DSL_ACC_GYRO_R_SIGN_MOT_on_INT1(LSM6DSL_ACC_GYRO_INT1_SIGN_MOT_t *value)
{
 if( !LSM6DSL_ACC_GYRO_ReadReg(LSM6DSL_ACC_GYRO_INT1_CTRL, (uint8_t *)value, 1))
    return MEMS_ERROR;

  *value &= LSM6DSL_ACC_GYRO_INT1_SIGN_MOT_MASK; //mask

  return MEMS_SUCCESS;
}

/*******************************************************************************
* Function Name  : LSM6DSL_ACC_GYRO_W_STEP_DET_on_INT1
* Description    : Write INT1_PEDO
* Input          : LSM6DSL_ACC_GYRO_INT1_PEDO_t
* Output         : None
* Return         : Status [MEMS_ERROR, MEMS_SUCCESS]
*******************************************************************************/
mems_status_t  LSM6DSL_ACC_GYRO_W_STEP_DET_on_INT1(LSM6DSL_ACC_GYRO_INT1_PEDO_t newValue)
{
  uint8_t value;

  if( !LSM6DSL_ACC_GYRO_ReadReg(LSM6DSL_ACC_GYRO_INT1_CTRL, &value, 1))
    return MEMS_ERROR;

  value &= ~LSM6DSL_ACC_GYRO_INT1_PEDO_MASK;
  value |= newValue;

  if( !LSM6DSL_ACC_GYRO_WriteReg(LSM6DSL_ACC_GYRO_INT1_CTRL, &value, 1) )
    return MEMS_ERROR;

  return MEMS_SUCCESS;
}

/*******************************************************************************
* Function Name  : LSM6DSL_ACC_GYRO_R_STEP_DET_on_INT1
* Description    : Read INT1_PEDO
* Input          : Pointer to LSM6DSL_ACC_GYRO_INT1_PEDO_t
* Output         : Status of INT1_PEDO see LSM6DSL_ACC_GYRO_INT1_PEDO_t
* Return         : Status [MEMS_ERROR, MEMS_SUCCESS]
*******************************************************************************/
mems_status_t LSM6DSL_ACC_GYRO_R_STEP_DET_on_INT1(LSM6DSL_ACC_GYRO_INT1_PEDO_t *value)
{
 if( !LSM6DSL_ACC_GYRO_ReadReg(LSM6DSL_ACC_GYRO_INT1_CTRL, (uint8_t *)value, 1))
    return MEMS_ERROR;

  *value &= LSM6DSL_ACC_GYRO_INT1_PEDO_MASK; //mask

  return MEMS_SUCCESS;
}

/*******************************************************************************
* Function Name  : LSM6DSL_ACC_GYRO_W_DRDY_XL_on_INT2
* Description    : Write INT2_DRDY_XL
* Input          : LSM6DSL_ACC_GYRO_INT2_DRDY_XL_t
* Output         : None
* Return         : Status [MEMS_ERROR, MEMS_SUCCESS]
*******************************************************************************/
mems_status_t  LSM6DSL_ACC_GYRO_W_DRDY_XL_on_INT2(LSM6DSL_ACC_GYRO_INT2_DRDY_XL_t newValue)
{
  uint8_t value;

  if( !LSM6DSL_ACC_GYRO_ReadReg(LSM6DSL_ACC_GYRO_INT2_CTRL, &value, 1))
    return MEMS_ERROR;

  value &= ~LSM6DSL_ACC_GYRO_INT2_DRDY_XL_MASK;
  value |= newValue;

  if( !LSM6DSL_ACC_GYRO_WriteReg(LSM6DSL_ACC_GYRO_INT2_CTRL, &value, 1) )
    return MEMS_ERROR;

  return MEMS_SUCCESS;
}

/*******************************************************************************
* Function Name  : LSM6DSL_ACC_GYRO_R_DRDY_XL_on_INT2
* Description    : Read INT2_DRDY_XL
* Input          : Pointer to LSM6DSL_ACC_GYRO_INT2_DRDY_XL_t
* Output         : Status of INT2_DRDY_XL see LSM6DSL_ACC_GYRO_INT2_DRDY_XL_t
* Return         : Status [MEMS_ERROR, MEMS_SUCCESS]
*******************************************************************************/
mems_status_t LSM6DSL_ACC_GYRO_R_DRDY_XL_on_INT2(LSM6DSL_ACC_GYRO_INT2_DRDY_XL_t *value)
{
 if( !LSM6DSL_ACC_GYRO_ReadReg(LSM6DSL_ACC_GYRO_INT2_CTRL, (uint8_t *)value, 1))
    return MEMS_ERROR;

  *value &= LSM6DSL_ACC_GYRO_INT2_DRDY_XL_MASK; //mask

  return MEMS_SUCCESS;
}

/*******************************************************************************
* Function Name  : LSM6DSL_ACC_GYRO_W_DRDY_G_on_INT2
* Description    : Write INT2_DRDY_G
* Input          : LSM6DSL_ACC_GYRO_INT2_DRDY_G_t
* Output         : None
* Return         : Status [MEMS_ERROR, MEMS_SUCCESS]
*******************************************************************************/
mems_status_t  LSM6DSL_ACC_GYRO_W_DRDY_G_on_INT2(LSM6DSL_ACC_GYRO_INT2_DRDY_G_t newValue)
{
  uint8_t value;

  if( !LSM6DSL_ACC_GYRO_ReadReg(LSM6DSL_ACC_GYRO_INT2_CTRL, &value, 1))
    return MEMS_ERROR;

  value &= ~LSM6DSL_ACC_GYRO_INT2_DRDY_G_MASK;
  value |= newValue;

  if( !LSM6DSL_ACC_GYRO_WriteReg(LSM6DSL_ACC_GYRO_INT2_CTRL, &value, 1) )
    return MEMS_ERROR;

  return MEMS_SUCCESS;
}

/*******************************************************************************
* Function Name  : LSM6DSL_ACC_GYRO_R_DRDY_G_on_INT2
* Description    : Read INT2_DRDY_G
* Input          : Pointer to LSM6DSL_ACC_GYRO_INT2_DRDY_G_t
* Output         : Status of INT2_DRDY_G see LSM6DSL_ACC_GYRO_INT2_DRDY_G_t
* Return         : Status [MEMS_ERROR, MEMS_SUCCESS]
*******************************************************************************/
mems_status_t LSM6DSL_ACC_GYRO_R_DRDY_G_on_INT2(LSM6DSL_ACC_GYRO_INT2_DRDY_G_t *value)
{
 if( !LSM6DSL_ACC_GYRO_ReadReg(LSM6DSL_ACC_GYRO_INT2_CTRL, (uint8_t *)value, 1))
    return MEMS_ERROR;

  *value &= LSM6DSL_ACC_GYRO_INT2_DRDY_G_MASK; //mask

  return MEMS_SUCCESS;
}

/*******************************************************************************
* Function Name  : LSM6DSL_ACC_GYRO_W_DRDY_TEMP_on_INT2
* Description    : Write INT2_DRDY_TEMP
* Input          : LSM6DSL_ACC_GYRO_INT2_DRDY_TEMP_t
* Output         : None
* Return         : Status [MEMS_ERROR, MEMS_SUCCESS]
*******************************************************************************/
mems_status_t  LSM6DSL_ACC_GYRO_W_DRDY_TEMP_on_INT2(LSM6DSL_ACC_GYRO_INT2_DRDY_TEMP_t newValue)
{
  uint8_t value;

  if( !LSM6DSL_ACC_GYRO_ReadReg(LSM6DSL_ACC_GYRO_INT2_CTRL, &value, 1))
    return MEMS_ERROR;

  value &= ~LSM6DSL_ACC_GYRO_INT2_DRDY_TEMP_MASK;
  value |= newValue;

  if( !LSM6DSL_ACC_GYRO_WriteReg(LSM6DSL_ACC_GYRO_INT2_CTRL, &value, 1) )
    return MEMS_ERROR;

  return MEMS_SUCCESS;
}

/*******************************************************************************
* Function Name  : LSM6DSL_ACC_GYRO_R_DRDY_TEMP_on_INT2
* Description    : Read INT2_DRDY_TEMP
* Input          : Pointer to LSM6DSL_ACC_GYRO_INT2_DRDY_TEMP_t
* Output         : Status of INT2_DRDY_TEMP see LSM6DSL_ACC_GYRO_INT2_DRDY_TEMP_t
* Return         : Status [MEMS_ERROR, MEMS_SUCCESS]
*******************************************************************************/
mems_status_t LSM6DSL_ACC_GYRO_R_DRDY_TEMP_on_INT2(LSM6DSL_ACC_GYRO_INT2_DRDY_TEMP_t *value)
{
 if( !LSM6DSL_ACC_GYRO_ReadReg(LSM6DSL_ACC_GYRO_INT2_CTRL, (uint8_t *)value, 1))
    return MEMS_ERROR;

  *value &= LSM6DSL_ACC_GYRO_INT2_DRDY_TEMP_MASK; //mask

  return MEMS_SUCCESS;
}

/*******************************************************************************
* Function Name  : LSM6DSL_ACC_GYRO_W_FIFO_TSHLD_on_INT2
* Description    : Write INT2_FTH
* Input          : LSM6DSL_ACC_GYRO_INT2_FTH_t
* Output         : None
* Return         : Status [MEMS_ERROR, MEMS_SUCCESS]
*******************************************************************************/
mems_status_t  LSM6DSL_ACC_GYRO_W_FIFO_TSHLD_on_INT2(LSM6DSL_ACC_GYRO_INT2_FTH_t newValue)
{
  uint8_t value;

  if( !LSM6DSL_ACC_GYRO_ReadReg(LSM6DSL_ACC_GYRO_INT2_CTRL, &value, 1))
    return MEMS_ERROR;

  value &= ~LSM6DSL_ACC_GYRO_INT2_FTH_MASK;
  value |= newValue;

  if( !LSM6DSL_ACC_GYRO_WriteReg(LSM6DSL_ACC_GYRO_INT2_CTRL, &value, 1) )
    return MEMS_ERROR;

  return MEMS_SUCCESS;
}

/*******************************************************************************
* Function Name  : LSM6DSL_ACC_GYRO_R_FIFO_TSHLD_on_INT2
* Description    : Read INT2_FTH
* Input          : Pointer to LSM6DSL_ACC_GYRO_INT2_FTH_t
* Output         : Status of INT2_FTH see LSM6DSL_ACC_GYRO_INT2_FTH_t
* Return         : Status [MEMS_ERROR, MEMS_SUCCESS]
*******************************************************************************/
mems_status_t LSM6DSL_ACC_GYRO_R_FIFO_TSHLD_on_INT2(LSM6DSL_ACC_GYRO_INT2_FTH_t *value)
{
 if( !LSM6DSL_ACC_GYRO_ReadReg(LSM6DSL_ACC_GYRO_INT2_CTRL, (uint8_t *)value, 1))
    return MEMS_ERROR;

  *value &= LSM6DSL_ACC_GYRO_INT2_FTH_MASK; //mask

  return MEMS_SUCCESS;
}

/*******************************************************************************
* Function Name  : LSM6DSL_ACC_GYRO_W_OVERRUN_on_INT2
* Description    : Write INT2_OVR
* Input          : LSM6DSL_ACC_GYRO_INT2_OVR_t
* Output         : None
* Return         : Status [MEMS_ERROR, MEMS_SUCCESS]
*******************************************************************************/
mems_status_t  LSM6DSL_ACC_GYRO_W_OVERRUN_on_INT2(LSM6DSL_ACC_GYRO_INT2_OVR_t newValue)
{
  uint8_t value;

  if( !LSM6DSL_ACC_GYRO_ReadReg(LSM6DSL_ACC_GYRO_INT2_CTRL, &value, 1))
    return MEMS_ERROR;

  value &= ~LSM6DSL_ACC_GYRO_INT2_OVR_MASK;
  value |= newValue;

  if( !LSM6DSL_ACC_GYRO_WriteReg(LSM6DSL_ACC_GYRO_INT2_CTRL, &value, 1) )
    return MEMS_ERROR;

  return MEMS_SUCCESS;
}

/*******************************************************************************
* Function Name  : LSM6DSL_ACC_GYRO_R_OVERRUN_on_INT2
* Description    : Read INT2_OVR
* Input          : Pointer to LSM6DSL_ACC_GYRO_INT2_OVR_t
* Output         : Status of INT2_OVR see LSM6DSL_ACC_GYRO_INT2_OVR_t
* Return         : Status [MEMS_ERROR, MEMS_SUCCESS]
*******************************************************************************/
mems_status_t LSM6DSL_ACC_GYRO_R_OVERRUN_on_INT2(LSM6DSL_ACC_GYRO_INT2_OVR_t *value)
{
 if( !LSM6DSL_ACC_GYRO_ReadReg(LSM6DSL_ACC_GYRO_INT2_CTRL, (uint8_t *)value, 1))
    return MEMS_ERROR;

  *value &= LSM6DSL_ACC_GYRO_INT2_OVR_MASK; //mask

  return MEMS_SUCCESS;
}

/*******************************************************************************
* Function Name  : LSM6DSL_ACC_GYRO_W_FULL_FLAG_on_INT2
* Description    : Write INT2_FULL_FLAG
* Input          : LSM6DSL_ACC_GYRO_INT2_FULL_FLAG_t
* Output         : None
* Return         : Status [MEMS_ERROR, MEMS_SUCCESS]
*******************************************************************************/
mems_status_t  LSM6DSL_ACC_GYRO_W_FULL_FLAG_on_INT2(LSM6DSL_ACC_GYRO_INT2_FULL_FLAG_t newValue)
{
  uint8_t value;

  if( !LSM6DSL_ACC_GYRO_ReadReg(LSM6DSL_ACC_GYRO_INT2_CTRL, &value, 1))
    return MEMS_ERROR;

  value &= ~LSM6DSL_ACC_GYRO_INT2_FULL_FLAG_MASK;
  value |= newValue;

  if( !LSM6DSL_ACC_GYRO_WriteReg(LSM6DSL_ACC_GYRO_INT2_CTRL, &value, 1) )
    return MEMS_ERROR;

  return MEMS_SUCCESS;
}

/*******************************************************************************
* Function Name  : LSM6DSL_ACC_GYRO_R_FULL_FLAG_on_INT2
* Description    : Read INT2_FULL_FLAG
* Input          : Pointer to LSM6DSL_ACC_GYRO_INT2_FULL_FLAG_t
* Output         : Status of INT2_FULL_FLAG see LSM6DSL_ACC_GYRO_INT2_FULL_FLAG_t
* Return         : Status [MEMS_ERROR, MEMS_SUCCESS]
*******************************************************************************/
mems_status_t LSM6DSL_ACC_GYRO_R_FULL_FLAG_on_INT2(LSM6DSL_ACC_GYRO_INT2_FULL_FLAG_t *value)
{
 if( !LSM6DSL_ACC_GYRO_ReadReg(LSM6DSL_ACC_GYRO_INT2_CTRL, (uint8_t *)value, 1))
    return MEMS_ERROR;

  *value &= LSM6DSL_ACC_GYRO_INT2_FULL_FLAG_MASK; //mask

  return MEMS_SUCCESS;
}

/*******************************************************************************
* Function Name  : LSM6DSL_ACC_GYRO_W_STEP_COUNT_OV_on_INT2
* Description    : Write INT2_STEP_COUNT_OV
* Input          : LSM6DSL_ACC_GYRO_INT2_STEP_COUNT_OV_t
* Output         : None
* Return         : Status [MEMS_ERROR, MEMS_SUCCESS]
*******************************************************************************/
mems_status_t  LSM6DSL_ACC_GYRO_W_STEP_COUNT_OV_on_INT2(LSM6DSL_ACC_GYRO_INT2_STEP_COUNT_OV_t newValue)
{
  uint8_t value;

  if( !LSM6DSL_ACC_GYRO_ReadReg(LSM6DSL_ACC_GYRO_INT2_CTRL, &value, 1))
    return MEMS_ERROR;

  value &= ~LSM6DSL_ACC_GYRO_INT2_STEP_COUNT_OV_MASK;
  value |= newValue;

  if( !LSM6DSL_ACC_GYRO_WriteReg(LSM6DSL_ACC_GYRO_INT2_CTRL, &value, 1) )
    return MEMS_ERROR;

  return MEMS_SUCCESS;
}

/*******************************************************************************
* Function Name  : LSM6DSL_ACC_GYRO_R_STEP_COUNT_OV_on_INT2
* Description    : Read INT2_STEP_COUNT_OV
* Input          : Pointer to LSM6DSL_ACC_GYRO_INT2_STEP_COUNT_OV_t
* Output         : Status of INT2_STEP_COUNT_OV see LSM6DSL_ACC_GYRO_INT2_STEP_COUNT_OV_t
* Return         : Status [MEMS_ERROR, MEMS_SUCCESS]
*******************************************************************************/
mems_status_t LSM6DSL_ACC_GYRO_R_STEP_COUNT_OV_on_INT2(LSM6DSL_ACC_GYRO_INT2_STEP_COUNT_OV_t *value)
{
 if( !LSM6DSL_ACC_GYRO_ReadReg(LSM6DSL_ACC_GYRO_INT2_CTRL, (uint8_t *)value, 1))
    return MEMS_ERROR;

  *value &= LSM6DSL_ACC_GYRO_INT2_STEP_COUNT_OV_MASK; //mask

  return MEMS_SUCCESS;
}

/*******************************************************************************
* Function Name  : LSM6DSL_ACC_GYRO_W_STEP_DELTA_on_INT2
* Description    : Write INT2_STEP_DELTA
* Input          : LSM6DSL_ACC_GYRO_INT2_STEP_DELTA_t
* Output         : None
* Return         : Status [MEMS_ERROR, MEMS_SUCCESS]
*******************************************************************************/
mems_status_t  LSM6DSL_ACC_GYRO_W_STEP_DELTA_on_INT2(LSM6DSL_ACC_GYRO_INT2_STEP_DELTA_t newValue)
{
  uint8_t value;

  if( !LSM6DSL_ACC_GYRO_ReadReg(LSM6DSL_ACC_GYRO_INT2_CTRL, &value, 1))
    return MEMS_ERROR;

  value &= ~LSM6DSL_ACC_GYRO_INT2_STEP_DELTA_MASK;
  value |= newValue;

  if( !LSM6DSL_ACC_GYRO_WriteReg(LSM6DSL_ACC_GYRO_INT2_CTRL, &value, 1) )
    return MEMS_ERROR;

  return MEMS_SUCCESS;
}

/*******************************************************************************
* Function Name  : LSM6DSL_ACC_GYRO_R_STEP_DELTA_on_INT2
* Description    : Read INT2_STEP_DELTA
* Input          : Pointer to LSM6DSL_ACC_GYRO_INT2_STEP_DELTA_t
* Output         : Status of INT2_STEP_DELTA see LSM6DSL_ACC_GYRO_INT2_STEP_DELTA_t
* Return         : Status [MEMS_ERROR, MEMS_SUCCESS]
*******************************************************************************/
mems_status_t LSM6DSL_ACC_GYRO_R_STEP_DELTA_on_INT2(LSM6DSL_ACC_GYRO_INT2_STEP_DELTA_t *value)
{
 if( !LSM6DSL_ACC_GYRO_ReadReg(LSM6DSL_ACC_GYRO_INT2_CTRL, (uint8_t *)value, 1))
    return MEMS_ERROR;

  *value &= LSM6DSL_ACC_GYRO_INT2_STEP_DELTA_MASK; //mask

  return MEMS_SUCCESS;
}

/*******************************************************************************
* Function Name  : LSM6DSL_ACC_GYRO_W_SW_RESET
* Description    : Write SW_RESET
* Input          : LSM6DSL_ACC_GYRO_SW_RESET_t
* Output         : None
* Return         : Status [MEMS_ERROR, MEMS_SUCCESS]
*******************************************************************************/
mems_status_t  LSM6DSL_ACC_GYRO_W_SW_RESET(LSM6DSL_ACC_GYRO_SW_RESET_t newValue)
{
  uint8_t value;

  if( !LSM6DSL_ACC_GYRO_ReadReg(LSM6DSL_ACC_GYRO_CTRL3_C, &value, 1))
    return MEMS_ERROR;

  value &= ~LSM6DSL_ACC_GYRO_SW_RESET_MASK;
  value |= newValue;

  if( !LSM6DSL_ACC_GYRO_WriteReg(LSM6DSL_ACC_GYRO_CTRL3_C, &value, 1) )
    return MEMS_ERROR;

  return MEMS_SUCCESS;
}

/*******************************************************************************
* Function Name  : LSM6DSL_ACC_GYRO_R_SW_RESET
* Description    : Read SW_RESET
* Input          : Pointer to LSM6DSL_ACC_GYRO_SW_RESET_t
* Output         : Status of SW_RESET see LSM6DSL_ACC_GYRO_SW_RESET_t
* Return         : Status [MEMS_ERROR, MEMS_SUCCESS]
*******************************************************************************/
mems_status_t LSM6DSL_ACC_GYRO_R_SW_RESET(LSM6DSL_ACC_GYRO_SW_RESET_t *value)
{
 if( !LSM6DSL_ACC_GYRO_ReadReg(LSM6DSL_ACC_GYRO_CTRL3_C, (uint8_t *)value, 1))
    return MEMS_ERROR;

  *value &= LSM6DSL_ACC_GYRO_SW_RESET_MASK; //mask

  return MEMS_SUCCESS;
}

/*******************************************************************************
* Function Name  : LSM6DSL_ACC_GYRO_W_IF_Addr_Incr
* Description    : Write IF_INC
* Input          : LSM6DSL_ACC_GYRO_IF_INC_t
* Output         : None
* Return         : Status [MEMS_ERROR, MEMS_SUCCESS]
*******************************************************************************/
mems_status_t  LSM6DSL_ACC_GYRO_W_IF_Addr_Incr(LSM6DSL_ACC_GYRO_IF_INC_t newValue)
{
  uint8_t value;

  if( !LSM6DSL_ACC_GYRO_ReadReg(LSM6DSL_ACC_GYRO_CTRL3_C, &value, 1))
    return MEMS_ERROR;

  value &= ~LSM6DSL_ACC_GYRO_IF_INC_MASK;
  value |= newValue;

  if( !LSM6DSL_ACC_GYRO_WriteReg(LSM6DSL_ACC_GYRO_CTRL3_C, &value, 1) )
    return MEMS_ERROR;

  return MEMS_SUCCESS;
}

/*******************************************************************************
* Function Name  : LSM6DSL_ACC_GYRO_R_IF_Addr_Incr
* Description    : Read IF_INC
* Input          : Pointer to LSM6DSL_ACC_GYRO_IF_INC_t
* Output         : Status of IF_INC see LSM6DSL_ACC_GYRO_IF_INC_t
* Return         : Status [MEMS_ERROR, MEMS_SUCCESS]
*******************************************************************************/
mems_status_t LSM6DSL_ACC_GYRO_R_IF_Addr_Incr(LSM6DSL_ACC_GYRO_IF_INC_t *value)
{
 if( !LSM6DSL_ACC_GYRO_ReadReg(LSM6DSL_ACC_GYRO_CTRL3_C, (uint8_t *)value, 1) )
    return MEMS_ERROR;

  *value &= LSM6DSL_ACC_GYRO_IF_INC_MASK; //mask

  return MEMS_SUCCESS;
}

/*******************************************************************************
* Function Name  : LSM6DSL_ACC_GYRO_W_SPI_Mode
* Description    : Write SIM
* Input          : LSM6DSL_ACC_GYRO_SIM_t
* Output         : None
* Return         : Status [MEMS_ERROR, MEMS_SUCCESS]
*******************************************************************************/
mems_status_t  LSM6DSL_ACC_GYRO_W_SPI_Mode(LSM6DSL_ACC_GYRO_SIM_t newValue)
{
  uint8_t value;

  if( !LSM6DSL_ACC_GYRO_ReadReg(LSM6DSL_ACC_GYRO_CTRL3_C, &value, 1))
    return MEMS_ERROR;

  value &= ~LSM6DSL_ACC_GYRO_SIM_MASK;
  value |= newValue;

  if( !LSM6DSL_ACC_GYRO_WriteReg(LSM6DSL_ACC_GYRO_CTRL3_C, &value, 1) )
    return MEMS_ERROR;

  return MEMS_SUCCESS;
}

/*******************************************************************************
* Function Name  : LSM6DSL_ACC_GYRO_R_SPI_Mode
* Description    : Read SIM
* Input          : Pointer to LSM6DSL_ACC_GYRO_SIM_t
* Output         : Status of SIM see LSM6DSL_ACC_GYRO_SIM_t
* Return         : Status [MEMS_ERROR, MEMS_SUCCESS]
*******************************************************************************/
mems_status_t LSM6DSL_ACC_GYRO_R_SPI_Mode(LSM6DSL_ACC_GYRO_SIM_t *value)
{
 if( !LSM6DSL_ACC_GYRO_ReadReg(LSM6DSL_ACC_GYRO_CTRL3_C, (uint8_t *)value, 1))
    return MEMS_ERROR;

  *value &= LSM6DSL_ACC_GYRO_SIM_MASK; //mask

  return MEMS_SUCCESS;
}

/*******************************************************************************
* Function Name  : LSM6DSL_ACC_GYRO_W_PadSel
* Description    : Write PP_OD
* Input          : LSM6DSL_ACC_GYRO_PP_OD_t
* Output         : None
* Return         : Status [MEMS_ERROR, MEMS_SUCCESS]
*******************************************************************************/
mems_status_t  LSM6DSL_ACC_GYRO_W_PadSel(LSM6DSL_ACC_GYRO_PP_OD_t newValue)
{
  uint8_t value;

  if( !LSM6DSL_ACC_GYRO_ReadReg(LSM6DSL_ACC_GYRO_CTRL3_C, &value, 1))
    return MEMS_ERROR;

  value &= ~LSM6DSL_ACC_GYRO_PP_OD_MASK;
  value |= newValue;

  if( !LSM6DSL_ACC_GYRO_WriteReg(LSM6DSL_ACC_GYRO_CTRL3_C, &value, 1) )
    return MEMS_ERROR;

  return MEMS_SUCCESS;
}

/*******************************************************************************
* Function Name  : LSM6DSL_ACC_GYRO_R_PadSel
* Description    : Read PP_OD
* Input          : Pointer to LSM6DSL_ACC_GYRO_PP_OD_t
* Output         : Status of PP_OD see LSM6DSL_ACC_GYRO_PP_OD_t
* Return         : Status [MEMS_ERROR, MEMS_SUCCESS]
*******************************************************************************/
mems_status_t LSM6DSL_ACC_GYRO_R_PadSel(LSM6DSL_ACC_GYRO_PP_OD_t *value)
{
 if( !LSM6DSL_ACC_GYRO_ReadReg(LSM6DSL_ACC_GYRO_CTRL3_C, (uint8_t *)value, 1) )
    return MEMS_ERROR;

  *value &= LSM6DSL_ACC_GYRO_PP_OD_MASK; //mask

  return MEMS_SUCCESS;
}

/*******************************************************************************
* Function Name  : LSM6DSL_ACC_GYRO_W_INT_ACT_LEVEL
* Description    : Write INT_ACT_LEVEL
* Input          : LSM6DSL_ACC_GYRO_INT_ACT_LEVEL_t
* Output         : None
* Return         : Status [MEMS_ERROR, MEMS_SUCCESS]
*******************************************************************************/
mems_status_t  LSM6DSL_ACC_GYRO_W_INT_ACT_LEVEL(LSM6DSL_ACC_GYRO_INT_ACT_LEVEL_t newValue)
{
  uint8_t value;

  if( !LSM6DSL_ACC_GYRO_ReadReg(LSM6DSL_ACC_GYRO_CTRL3_C, &value, 1))
    return MEMS_ERROR;

  value &= ~LSM6DSL_ACC_GYRO_INT_ACT_LEVEL_MASK;
  value |= newValue;

  if( !LSM6DSL_ACC_GYRO_WriteReg(LSM6DSL_ACC_GYRO_CTRL3_C, &value, 1) )
    return MEMS_ERROR;

  return MEMS_SUCCESS;
}

/*******************************************************************************
* Function Name  : LSM6DSL_ACC_GYRO_R_INT_ACT_LEVEL
* Description    : Read INT_ACT_LEVEL
* Input          : Pointer to LSM6DSL_ACC_GYRO_INT_ACT_LEVEL_t
* Output         : Status of INT_ACT_LEVEL see LSM6DSL_ACC_GYRO_INT_ACT_LEVEL_t
* Return         : Status [MEMS_ERROR, MEMS_SUCCESS]
*******************************************************************************/
mems_status_t LSM6DSL_ACC_GYRO_R_INT_ACT_LEVEL(LSM6DSL_ACC_GYRO_INT_ACT_LEVEL_t *value)
{
 if( !LSM6DSL_ACC_GYRO_ReadReg(LSM6DSL_ACC_GYRO_CTRL3_C, (uint8_t *)value, 1))
    return MEMS_ERROR;

  *value &= LSM6DSL_ACC_GYRO_INT_ACT_LEVEL_MASK; //mask

  return MEMS_SUCCESS;
}

/*******************************************************************************
* Function Name  : LSM6DSL_ACC_GYRO_W_BOOT
* Description    : Write BOOT
* Input          : LSM6DSL_ACC_GYRO_BOOT_t
* Output         : None
* Return         : Status [MEMS_ERROR, MEMS_SUCCESS]
*******************************************************************************/
mems_status_t  LSM6DSL_ACC_GYRO_W_BOOT(LSM6DSL_ACC_GYRO_BOOT_t newValue)
{
  uint8_t value;

  if( !LSM6DSL_ACC_GYRO_ReadReg(LSM6DSL_ACC_GYRO_CTRL3_C, &value, 1))
    return MEMS_ERROR;

  value &= ~LSM6DSL_ACC_GYRO_BOOT_MASK;
  value |= newValue;

  if( !LSM6DSL_ACC_GYRO_WriteReg(LSM6DSL_ACC_GYRO_CTRL3_C, &value, 1) )
    return MEMS_ERROR;

  return MEMS_SUCCESS;
}

/*******************************************************************************
* Function Name  : LSM6DSL_ACC_GYRO_R_BOOT
* Description    : Read BOOT
* Input          : Pointer to LSM6DSL_ACC_GYRO_BOOT_t
* Output         : Status of BOOT see LSM6DSL_ACC_GYRO_BOOT_t
* Return         : Status [MEMS_ERROR, MEMS_SUCCESS]
*******************************************************************************/
mems_status_t LSM6DSL_ACC_GYRO_R_BOOT(LSM6DSL_ACC_GYRO_BOOT_t *value)
{
 if( !LSM6DSL_ACC_GYRO_ReadReg(LSM6DSL_ACC_GYRO_CTRL3_C, (uint8_t *)value, 1) )
    return MEMS_ERROR;

  *value &= LSM6DSL_ACC_GYRO_BOOT_MASK; //mask

  return MEMS_SUCCESS;
}

/*******************************************************************************
* Function Name  : LSM6DSL_ACC_GYRO_LPF1_SEL_G
* Description    : Write LPF1_SEL_G
* Input          : LSM6DSL_ACC_GYRO_LPF1_SEL_G_t
* Output         : None
* Return         : Status [MEMS_ERROR, MEMS_SUCCESS]
*******************************************************************************/
mems_status_t  LSM6DSL_ACC_GYRO_W_LPF1_SEL_G(LSM6DSL_ACC_GYRO_LPF1_SEL_G_t newValue)
{
  uint8_t value;

  if( !LSM6DSL_ACC_GYRO_ReadReg(LSM6DSL_ACC_GYRO_CTRL4_C, &value, 1))
    return MEMS_ERROR;

  value &= ~LSM6DSL_ACC_GYRO_LPF1_SEL_G_MASK;
  value |= newValue;

  if( !LSM6DSL_ACC_GYRO_WriteReg(LSM6DSL_ACC_GYRO_CTRL4_C, &value, 1) )
    return MEMS_ERROR;

  return MEMS_SUCCESS;
}

/*******************************************************************************
* Function Name  : LSM6DSL_ACC_GYRO_LPF1_SEL_G
* Description    : Read LPF1_SEL_G
* Input          : Pointer to LSM6DSL_ACC_GYRO_LPF1_SEL_G_t
* Output         : Status of LPF1_SEL_G see LSM6DSL_ACC_GYRO_LPF1_SEL_G_t
* Return         : Status [MEMS_ERROR, MEMS_SUCCESS]
*******************************************************************************/
mems_status_t LSM6DSL_ACC_GYRO_R_LPF1_SEL_G(LSM6DSL_ACC_GYRO_LPF1_SEL_G_t *value)
{
 if( !LSM6DSL_ACC_GYRO_ReadReg(LSM6DSL_ACC_GYRO_CTRL4_C, (uint8_t *)value, 1) )
    return MEMS_ERROR;

  *value &= LSM6DSL_ACC_GYRO_LPF1_SEL_G_MASK; //mask

  return MEMS_SUCCESS;
}

/*******************************************************************************
* Function Name  : LSM6DSL_ACC_GYRO_W_I2C_DISABLE
* Description    : Write I2C_DISABLE
* Input          : LSM6DSL_ACC_GYRO_I2C_DISABLE_t
* Output         : None
* Return         : Status [MEMS_ERROR, MEMS_SUCCESS]
*******************************************************************************/
mems_status_t  LSM6DSL_ACC_GYRO_W_I2C_DISABLE(LSM6DSL_ACC_GYRO_I2C_DISABLE_t newValue)
{
  uint8_t value;

  if( !LSM6DSL_ACC_GYRO_ReadReg(LSM6DSL_ACC_GYRO_CTRL4_C, &value, 1))
    return MEMS_ERROR;

  value &= ~LSM6DSL_ACC_GYRO_I2C_DISABLE_MASK;
  value |= newValue;

  if( !LSM6DSL_ACC_GYRO_WriteReg(LSM6DSL_ACC_GYRO_CTRL4_C, &value, 1) )
    return MEMS_ERROR;

  return MEMS_SUCCESS;
}

/*******************************************************************************
* Function Name  : LSM6DSL_ACC_GYRO_R_I2C_DISABLE
* Description    : Read I2C_DISABLE
* Input          : Pointer to LSM6DSL_ACC_GYRO_I2C_DISABLE_t
* Output         : Status of I2C_DISABLE see LSM6DSL_ACC_GYRO_I2C_DISABLE_t
* Return         : Status [MEMS_ERROR, MEMS_SUCCESS]
*******************************************************************************/
mems_status_t LSM6DSL_ACC_GYRO_R_I2C_DISABLE(LSM6DSL_ACC_GYRO_I2C_DISABLE_t *value)
{
 if( !LSM6DSL_ACC_GYRO_ReadReg(LSM6DSL_ACC_GYRO_CTRL4_C, (uint8_t *)value, 1) )
    return MEMS_ERROR;

  *value &= LSM6DSL_ACC_GYRO_I2C_DISABLE_MASK; //mask

  return MEMS_SUCCESS;
}

/*******************************************************************************
* Function Name  : LSM6DSL_ACC_GYRO_W_DRDY_MSK
* Description    : Write DRDY_MSK
* Input          : LSM6DSL_ACC_GYRO_DRDY_MSK_t
* Output         : None
* Return         : Status [MEMS_ERROR, MEMS_SUCCESS]
*******************************************************************************/
mems_status_t  LSM6DSL_ACC_GYRO_W_DRDY_MSK(LSM6DSL_ACC_GYRO_DRDY_MSK_t newValue)
{
  uint8_t value;

  if( !LSM6DSL_ACC_GYRO_ReadReg(LSM6DSL_ACC_GYRO_CTRL4_C, &value, 1))
    return MEMS_ERROR;

  value &= ~LSM6DSL_ACC_GYRO_DRDY_MSK_MASK;
  value |= newValue;

  if( !LSM6DSL_ACC_GYRO_WriteReg(LSM6DSL_ACC_GYRO_CTRL4_C, &value, 1) )
    return MEMS_ERROR;

  return MEMS_SUCCESS;
}

/*******************************************************************************
* Function Name  : LSM6DSL_ACC_GYRO_R_DRDY_MSK
* Description    : Read DRDY_MSK
* Input          : Pointer to LSM6DSL_ACC_GYRO_DRDY_MSK_t
* Output         : Status of DRDY_MSK see LSM6DSL_ACC_GYRO_DRDY_MSK_t
* Return         : Status [MEMS_ERROR, MEMS_SUCCESS]
*******************************************************************************/
mems_status_t LSM6DSL_ACC_GYRO_R_DRDY_MSK(LSM6DSL_ACC_GYRO_DRDY_MSK_t *value)
{
 if( !LSM6DSL_ACC_GYRO_ReadReg(LSM6DSL_ACC_GYRO_CTRL4_C, (uint8_t *)value, 1))
    return MEMS_ERROR;

  *value &= LSM6DSL_ACC_GYRO_DRDY_MSK_MASK; //mask

  return MEMS_SUCCESS;
}

/*******************************************************************************
* Function Name  : LSM6DSL_ACC_GYRO_W_INT2_ON_INT1
* Description    : Write INT2_ON_INT1
* Input          : LSM6DSL_ACC_GYRO_INT2_ON_INT1_t
* Output         : None
* Return         : Status [MEMS_ERROR, MEMS_SUCCESS]
*******************************************************************************/
mems_status_t  LSM6DSL_ACC_GYRO_W_INT2_ON_INT1(LSM6DSL_ACC_GYRO_INT2_ON_INT1_t newValue)
{
  uint8_t value;

  if( !LSM6DSL_ACC_GYRO_ReadReg(LSM6DSL_ACC_GYRO_CTRL4_C, &value, 1))
    return MEMS_ERROR;

  value &= ~LSM6DSL_ACC_GYRO_INT2_ON_INT1_MASK;
  value |= newValue;

  if( !LSM6DSL_ACC_GYRO_WriteReg(LSM6DSL_ACC_GYRO_CTRL4_C, &value, 1) )
    return MEMS_ERROR;

  return MEMS_SUCCESS;
}

/*******************************************************************************
* Function Name  : LSM6DSL_ACC_GYRO_R_INT2_ON_INT1
* Description    : Read INT2_ON_INT1
* Input          : Pointer to LSM6DSL_ACC_GYRO_INT2_ON_INT1_t
* Output         : Status of INT2_ON_INT1 see LSM6DSL_ACC_GYRO_INT2_ON_INT1_t
* Return         : Status [MEMS_ERROR, MEMS_SUCCESS]
*******************************************************************************/
mems_status_t LSM6DSL_ACC_GYRO_R_INT2_ON_INT1(LSM6DSL_ACC_GYRO_INT2_ON_INT1_t *value)
{
 if( !LSM6DSL_ACC_GYRO_ReadReg(LSM6DSL_ACC_GYRO_CTRL4_C, (uint8_t *)value, 1))
    return MEMS_ERROR;

  *value &= LSM6DSL_ACC_GYRO_INT2_ON_INT1_MASK; //mask

  return MEMS_SUCCESS;
}

/*******************************************************************************
* Function Name  : LSM6DSL_ACC_GYRO_W_SleepMode_G
* Description    : Write SLEEP_G
* Input          : LSM6DSL_ACC_GYRO_SLEEP_G_t
* Output         : None
* Return         : Status [MEMS_ERROR, MEMS_SUCCESS]
*******************************************************************************/
mems_status_t  LSM6DSL_ACC_GYRO_W_SleepMode_G(LSM6DSL_ACC_GYRO_SLEEP_G_t newValue)
{
  uint8_t value;

  if( !LSM6DSL_ACC_GYRO_ReadReg(LSM6DSL_ACC_GYRO_CTRL4_C, &value, 1))
    return MEMS_ERROR;

  value &= ~LSM6DSL_ACC_GYRO_SLEEP_G_MASK;
  value |= newValue;

  if( !LSM6DSL_ACC_GYRO_WriteReg(LSM6DSL_ACC_GYRO_CTRL4_C, &value, 1) )
    return MEMS_ERROR;

  return MEMS_SUCCESS;
}

/*******************************************************************************
* Function Name  : LSM6DSL_ACC_GYRO_R_SleepMode_G
* Description    : Read SLEEP_G
* Input          : Pointer to LSM6DSL_ACC_GYRO_SLEEP_G_t
* Output         : Status of SLEEP_G see LSM6DSL_ACC_GYRO_SLEEP_G_t
* Return         : Status [MEMS_ERROR, MEMS_SUCCESS]
*******************************************************************************/
mems_status_t LSM6DSL_ACC_GYRO_R_SleepMode_G(LSM6DSL_ACC_GYRO_SLEEP_G_t *value)
{
 if( !LSM6DSL_ACC_GYRO_ReadReg(LSM6DSL_ACC_GYRO_CTRL4_C, (uint8_t *)value, 1))
    return MEMS_ERROR;

  *value &= LSM6DSL_ACC_GYRO_SLEEP_G_MASK; //mask

  return MEMS_SUCCESS;
}

/*******************************************************************************
* Function Name  : LSM6DSL_ACC_GYRO_W_SelfTest_XL
* Description    : Write ST_XL
* Input          : LSM6DSL_ACC_GYRO_ST_XL_t
* Output         : None
* Return         : Status [MEMS_ERROR, MEMS_SUCCESS]
*******************************************************************************/
mems_status_t  LSM6DSL_ACC_GYRO_W_SelfTest_XL(LSM6DSL_ACC_GYRO_ST_XL_t newValue)
{
  uint8_t value;

  if( !LSM6DSL_ACC_GYRO_ReadReg(LSM6DSL_ACC_GYRO_CTRL5_C, &value, 1))
    return MEMS_ERROR;

  value &= ~LSM6DSL_ACC_GYRO_ST_XL_MASK;
  value |= newValue;

  if( !LSM6DSL_ACC_GYRO_WriteReg(LSM6DSL_ACC_GYRO_CTRL5_C, &value, 1) )
    return MEMS_ERROR;

  return MEMS_SUCCESS;
}

/*******************************************************************************
* Function Name  : LSM6DSL_ACC_GYRO_R_SelfTest_XL
* Description    : Read ST_XL
* Input          : Pointer to LSM6DSL_ACC_GYRO_ST_XL_t
* Output         : Status of ST_XL see LSM6DSL_ACC_GYRO_ST_XL_t
* Return         : Status [MEMS_ERROR, MEMS_SUCCESS]
*******************************************************************************/
mems_status_t LSM6DSL_ACC_GYRO_R_SelfTest_XL(LSM6DSL_ACC_GYRO_ST_XL_t *value)
{
 if( !LSM6DSL_ACC_GYRO_ReadReg(LSM6DSL_ACC_GYRO_CTRL5_C, (uint8_t *)value, 1))
    return MEMS_ERROR;

  *value &= LSM6DSL_ACC_GYRO_ST_XL_MASK; //mask

  return MEMS_SUCCESS;
}

/*******************************************************************************
* Function Name  : LSM6DSL_ACC_GYRO_W_SelfTest_G
* Description    : Write ST_G
* Input          : LSM6DSL_ACC_GYRO_ST_G_t
* Output         : None
* Return         : Status [MEMS_ERROR, MEMS_SUCCESS]
*******************************************************************************/
mems_status_t  LSM6DSL_ACC_GYRO_W_SelfTest_G(LSM6DSL_ACC_GYRO_ST_G_t newValue)
{
  uint8_t value;

  if( !LSM6DSL_ACC_GYRO_ReadReg(LSM6DSL_ACC_GYRO_CTRL5_C, &value, 1))
    return MEMS_ERROR;

  value &= ~LSM6DSL_ACC_GYRO_ST_G_MASK;
  value |= newValue;

  if( !LSM6DSL_ACC_GYRO_WriteReg(LSM6DSL_ACC_GYRO_CTRL5_C, &value, 1) )
    return MEMS_ERROR;

  return MEMS_SUCCESS;
}

/*******************************************************************************
* Function Name  : LSM6DSL_ACC_GYRO_R_SelfTest_G
* Description    : Read ST_G
* Input          : Pointer to LSM6DSL_ACC_GYRO_ST_G_t
* Output         : Status of ST_G see LSM6DSL_ACC_GYRO_ST_G_t
* Return         : Status [MEMS_ERROR, MEMS_SUCCESS]
*******************************************************************************/
mems_status_t LSM6DSL_ACC_GYRO_R_SelfTest_G(LSM6DSL_ACC_GYRO_ST_G_t *value)
{
 if( !LSM6DSL_ACC_GYRO_ReadReg(LSM6DSL_ACC_GYRO_CTRL5_C, (uint8_t *)value, 1))
    return MEMS_ERROR;

  *value &= LSM6DSL_ACC_GYRO_ST_G_MASK; //mask

  return MEMS_SUCCESS;
}

/*******************************************************************************
* Function Name  : LSM6DSL_ACC_GYRO_W_DEN_Polarity
* Description    : Write DEN_LH
* Input          : LSM6DSL_ACC_GYRO_DEN_LH_t
* Output         : None
* Return         : Status [MEMS_ERROR, MEMS_SUCCESS]
*******************************************************************************/
mems_status_t  LSM6DSL_ACC_GYRO_W_DEN_Polarity(LSM6DSL_ACC_GYRO_DEN_LH_t newValue)
{
  uint8_t value;

  if( !LSM6DSL_ACC_GYRO_ReadReg(LSM6DSL_ACC_GYRO_CTRL5_C, &value, 1))
    return MEMS_ERROR;

  value &= ~LSM6DSL_ACC_GYRO_DEN_LH_MASK;
  value |= newValue;

  if( !LSM6DSL_ACC_GYRO_WriteReg(LSM6DSL_ACC_GYRO_CTRL5_C, &value, 1) )
    return MEMS_ERROR;

  return MEMS_SUCCESS;
}

/*******************************************************************************
* Function Name  : LSM6DSL_ACC_GYRO_R_DEN_Polarity
* Description    : Read DEN_LH
* Input          : Pointer to LSM6DSL_ACC_GYRO_DEN_LH_t
* Output         : Status of DEN_LH see LSM6DSL_ACC_GYRO_DEN_LH_t
* Return         : Status [MEMS_ERROR, MEMS_SUCCESS]
*******************************************************************************/
mems_status_t LSM6DSL_ACC_GYRO_R_DEN_Polarity(LSM6DSL_ACC_GYRO_DEN_LH_t *value)
{
 if( !LSM6DSL_ACC_GYRO_ReadReg(LSM6DSL_ACC_GYRO_CTRL5_C, (uint8_t *)value, 1))
    return MEMS_ERROR;

  *value &= LSM6DSL_ACC_GYRO_DEN_LH_MASK; //mask

  return MEMS_SUCCESS;
}

/*******************************************************************************
* Function Name  : LSM6DSL_ACC_GYRO_W_CircularBurstMode
* Description    : Write ST_ROUNDING
* Input          : LSM6DSL_ACC_GYRO_ROUNDING_t
* Output         : None
* Return         : Status [MEMS_ERROR, MEMS_SUCCESS]
*******************************************************************************/
mems_status_t  LSM6DSL_ACC_GYRO_W_CircularBurstMode(LSM6DSL_ACC_GYRO_ROUNDING_t newValue)
{
  uint8_t value;

  if( !LSM6DSL_ACC_GYRO_ReadReg(LSM6DSL_ACC_GYRO_CTRL5_C, &value, 1))
    return MEMS_ERROR;

  value &= ~LSM6DSL_ACC_GYRO_LSM6DSL_ACC_GYRO_ROUNDING_t_MASK;
  value |= newValue;

  if( !LSM6DSL_ACC_GYRO_WriteReg(LSM6DSL_ACC_GYRO_CTRL5_C, &value, 1) )
    return MEMS_ERROR;

  return MEMS_SUCCESS;
}

/*******************************************************************************
* Function Name  : LSM6DSL_ACC_GYRO_R_CircularBurstMode
* Description    : Read ST_ROUNDING
* Input          : Pointer to LSM6DSL_ACC_GYRO_ROUNDING_t
* Output         : Status of ST_ROUNDING see LSM6DSL_ACC_GYRO_ROUNDING_t
* Return         : Status [MEMS_ERROR, MEMS_SUCCESS]
*******************************************************************************/
mems_status_t LSM6DSL_ACC_GYRO_R_CircularBurstMode(LSM6DSL_ACC_GYRO_ROUNDING_t *value)
{
 if( !LSM6DSL_ACC_GYRO_ReadReg(LSM6DSL_ACC_GYRO_CTRL5_C, (uint8_t *)value, 1))
    return MEMS_ERROR;

  *value &= LSM6DSL_ACC_GYRO_LSM6DSL_ACC_GYRO_ROUNDING_t_MASK; //mask

  return MEMS_SUCCESS;
}

/*******************************************************************************
* Function Name  : LSM6DSL_ACC_GYRO_W_LP_BW_G
* Description    : Write FTYPE
* Input          : LSM6DSL_ACC_GYRO_FTYPE_t
* Output         : None
* Return         : Status [MEMS_ERROR, MEMS_SUCCESS]
*******************************************************************************/
mems_status_t  LSM6DSL_ACC_GYRO_W_LP_BW_G(LSM6DSL_ACC_GYRO_FTYPE_t newValue)
{
  uint8_t value;

  if( !LSM6DSL_ACC_GYRO_ReadReg(LSM6DSL_ACC_GYRO_CTRL6_G, &value, 1))
    return MEMS_ERROR;

  value &= ~LSM6DSL_ACC_GYRO_FTYPE_MASK;
  value |= newValue;

  if( !LSM6DSL_ACC_GYRO_WriteReg(LSM6DSL_ACC_GYRO_CTRL6_G, &value, 1) )
    return MEMS_ERROR;

  return MEMS_SUCCESS;
}

/*******************************************************************************
* Function Name  : LSM6DSL_ACC_GYRO_R_LP_BW_G
* Description    : Read FTYPE
* Input          : Pointer to LSM6DSL_ACC_GYRO_FTYPE_t
* Output         : Status of FTYPE see LSM6DSL_ACC_GYRO_FTYPE_t
* Return         : Status [MEMS_ERROR, MEMS_SUCCESS]
*******************************************************************************/
mems_status_t LSM6DSL_ACC_GYRO_R_LP_BW_G(LSM6DSL_ACC_GYRO_FTYPE_t *value)
{
 if( !LSM6DSL_ACC_GYRO_ReadReg(LSM6DSL_ACC_GYRO_CTRL6_G, (uint8_t *)value, 1))
    return MEMS_ERROR;

  *value &= LSM6DSL_ACC_GYRO_FTYPE_MASK; //mask

  return MEMS_SUCCESS;
}

/*******************************************************************************
* Function Name  : LSM6DSL_ACC_GYRO_W_UserOffsetWeight
* Description    : Write USR_OFF_W
* Input          : LSM6DSL_ACC_GYRO_USR_OFF_W_t
* Output         : None
* Return         : Status [MEMS_ERROR, MEMS_SUCCESS]
*******************************************************************************/
mems_status_t  LSM6DSL_ACC_GYRO_W_UserOffsetWeight(LSM6DSL_ACC_GYRO_USR_OFF_W_t newValue)
{
  uint8_t value;

  if( !LSM6DSL_ACC_GYRO_ReadReg(LSM6DSL_ACC_GYRO_CTRL6_G, &value, 1))
    return MEMS_ERROR;

  value &= ~LSM6DSL_ACC_GYRO_USR_OFF_W_MASK;
  value |= newValue;

  if( !LSM6DSL_ACC_GYRO_WriteReg(LSM6DSL_ACC_GYRO_CTRL6_G, &value, 1) )
    return MEMS_ERROR;

  return MEMS_SUCCESS;
}

/*******************************************************************************
* Function Name  : LSM6DSL_ACC_GYRO_R_UserOffsetWeight
* Description    : Read USR_OFF_W
* Input          : Pointer to LSM6DSL_ACC_GYRO_USR_OFF_W_t
* Output         : Status of USR_OFF_W see LSM6DSL_ACC_GYRO_USR_OFF_W_t
* Return         : Status [MEMS_ERROR, MEMS_SUCCESS]
*******************************************************************************/
mems_status_t LSM6DSL_ACC_GYRO_R_UserOffsetWeight(LSM6DSL_ACC_GYRO_USR_OFF_W_t *value)
{
 if( !LSM6DSL_ACC_GYRO_ReadReg(LSM6DSL_ACC_GYRO_CTRL6_G, (uint8_t *)value, 1))
    return MEMS_ERROR;

  *value &= LSM6DSL_ACC_GYRO_USR_OFF_W_MASK; //mask

  return MEMS_SUCCESS;
}

/*******************************************************************************
* Function Name  : LSM6DSL_ACC_GYRO_W_LowPower_XL
* Description    : Write LP_XL
* Input          : LSM6DSL_ACC_GYRO_LP_XL_t
* Output         : None
* Return         : Status [MEMS_ERROR, MEMS_SUCCESS]
*******************************************************************************/
mems_status_t  LSM6DSL_ACC_GYRO_W_LowPower_XL(LSM6DSL_ACC_GYRO_LP_XL_t newValue)
{
  uint8_t value;

  if( !LSM6DSL_ACC_GYRO_ReadReg(LSM6DSL_ACC_GYRO_CTRL6_G, &value, 1))
    return MEMS_ERROR;

  value &= ~LSM6DSL_ACC_GYRO_LP_XL_MASK;
  value |= newValue;

  if( !LSM6DSL_ACC_GYRO_WriteReg(LSM6DSL_ACC_GYRO_CTRL6_G, &value, 1) )
    return MEMS_ERROR;

  return MEMS_SUCCESS;
}

/*******************************************************************************
* Function Name  : LSM6DSL_ACC_GYRO_R_LowPower_XL
* Description    : Read LP_XL
* Input          : Pointer to LSM6DSL_ACC_GYRO_LP_XL_t
* Output         : Status of LP_XL see LSM6DSL_ACC_GYRO_LP_XL_t
* Return         : Status [MEMS_ERROR, MEMS_SUCCESS]
*******************************************************************************/
mems_status_t LSM6DSL_ACC_GYRO_R_LowPower_XL(LSM6DSL_ACC_GYRO_LP_XL_t *value)
{
 if( !LSM6DSL_ACC_GYRO_ReadReg(LSM6DSL_ACC_GYRO_CTRL6_G, (uint8_t *)value, 1))
    return MEMS_ERROR;

  *value &= LSM6DSL_ACC_GYRO_LP_XL_MASK; //mask

  return MEMS_SUCCESS;
}
/*******************************************************************************
* Function Name  : LSM6DSL_ACC_GYRO_W_DEN_LVL2_EN
* Description    : Write DEN_LVL2_EN
* Input          : LSM6DSL_ACC_GYRO_DEN_LVL2_EN_t
* Output         : None
* Return         : Status [MEMS_ERROR, MEMS_SUCCESS]
*******************************************************************************/
mems_status_t  LSM6DSL_ACC_GYRO_W_DEN_LVL2_EN(LSM6DSL_ACC_GYRO_DEN_LVL2_EN_t newValue)
{
  uint8_t value;

  if( !LSM6DSL_ACC_GYRO_ReadReg(LSM6DSL_ACC_GYRO_CTRL6_G, &value, 1))
    return MEMS_ERROR;

  value &= ~LSM6DSL_ACC_GYRO_DEN_LVL2_EN_MASK;
  value |= newValue;

  if( !LSM6DSL_ACC_GYRO_WriteReg(LSM6DSL_ACC_GYRO_CTRL6_G, &value, 1) )
    return MEMS_ERROR;

  return MEMS_SUCCESS;
}

/*******************************************************************************
* Function Name  : LSM6DSL_ACC_GYRO_R_DEN_LVL2_EN
* Description    : Read DEN_LVL2_EN
* Input          : Pointer to LSM6DSL_ACC_GYRO_DEN_LVL2_EN_t
* Output         : Status of DEN_LVL2_EN see LSM6DSL_ACC_GYRO_DEN_LVL2_EN_t
* Return         : Status [MEMS_ERROR, MEMS_SUCCESS]
*******************************************************************************/
mems_status_t LSM6DSL_ACC_GYRO_R_DEN_LVL2_EN(LSM6DSL_ACC_GYRO_DEN_LVL2_EN_t *value)
{
 if( !LSM6DSL_ACC_GYRO_ReadReg(LSM6DSL_ACC_GYRO_CTRL6_G, (uint8_t *)value, 1))
    return MEMS_ERROR;

  *value &= LSM6DSL_ACC_GYRO_DEN_LVL2_EN_MASK; //mask

  return MEMS_SUCCESS;
}
/*******************************************************************************
* Function Name  : LSM6DSL_ACC_GYRO_W_DEN_LVL_EN
* Description    : Write DEN_LVL_EN
* Input          : LSM6DSL_ACC_GYRO_DEN_LVL_EN_t
* Output         : None
* Return         : Status [MEMS_ERROR, MEMS_SUCCESS]
*******************************************************************************/
mems_status_t  LSM6DSL_ACC_GYRO_W_DEN_LVL_EN(LSM6DSL_ACC_GYRO_DEN_LVL_EN_t newValue)
{
  uint8_t value;

  if( !LSM6DSL_ACC_GYRO_ReadReg(LSM6DSL_ACC_GYRO_CTRL6_G, &value, 1))
    return MEMS_ERROR;

  value &= ~LSM6DSL_ACC_GYRO_DEN_LVL_EN_MASK;
  value |= newValue;

  if( !LSM6DSL_ACC_GYRO_WriteReg(LSM6DSL_ACC_GYRO_CTRL6_G, &value, 1) )
    return MEMS_ERROR;

  return MEMS_SUCCESS;
}

/*******************************************************************************
* Function Name  : LSM6DSL_ACC_GYRO_R_DEN_LVL_EN
* Description    : Read DEN_LVL_EN
* Input          : Pointer to LSM6DSL_ACC_GYRO_DEN_LVL_EN_t
* Output         : Status of DEN_LVL_EN see LSM6DSL_ACC_GYRO_DEN_LVL_EN_t
* Return         : Status [MEMS_ERROR, MEMS_SUCCESS]
*******************************************************************************/
mems_status_t LSM6DSL_ACC_GYRO_R_DEN_LVL_EN(LSM6DSL_ACC_GYRO_DEN_LVL_EN_t *value)
{
 if( !LSM6DSL_ACC_GYRO_ReadReg(LSM6DSL_ACC_GYRO_CTRL6_G, (uint8_t *)value, 1) )
    return MEMS_ERROR;

  *value &= LSM6DSL_ACC_GYRO_DEN_LVL_EN_MASK; //mask

  return MEMS_SUCCESS;
}
/*******************************************************************************
* Function Name  : LSM6DSL_ACC_GYRO_W_ExternalTrigger
* Description    : Write DEN_EDGE_EN
* Input          : LSM6DSL_ACC_GYRO_DEN_EDGE_EN_t
* Output         : None
* Return         : Status [MEMS_ERROR, MEMS_SUCCESS]
*******************************************************************************/
mems_status_t  LSM6DSL_ACC_GYRO_W_ExternalTrigger(LSM6DSL_ACC_GYRO_DEN_EDGE_EN_t newValue)
{
  uint8_t value;

  if( !LSM6DSL_ACC_GYRO_ReadReg(LSM6DSL_ACC_GYRO_CTRL6_G, &value, 1) )
    return MEMS_ERROR;

  value &= ~LSM6DSL_ACC_GYRO_DEN_EDGE_EN_MASK;
  value |= newValue;

  if( !LSM6DSL_ACC_GYRO_WriteReg(LSM6DSL_ACC_GYRO_CTRL6_G, &value, 1) )
    return MEMS_ERROR;

  return MEMS_SUCCESS;
}

/*******************************************************************************
* Function Name  : LSM6DSL_ACC_GYRO_R_ExternalTrigger
* Description    : Read DEN_EDGE_EN
* Input          : Pointer to LSM6DSL_ACC_GYRO_DEN_EDGE_EN_t
* Output         : Status of DEN_EDGE_EN see LSM6DSL_ACC_GYRO_DEN_EDGE_EN_t
* Return         : Status [MEMS_ERROR, MEMS_SUCCESS]
*******************************************************************************/
mems_status_t LSM6DSL_ACC_GYRO_R_ExternalTrigger(LSM6DSL_ACC_GYRO_DEN_EDGE_EN_t *value)
{
 if( !LSM6DSL_ACC_GYRO_ReadReg(LSM6DSL_ACC_GYRO_CTRL6_G, (uint8_t *)value, 1) )
    return MEMS_ERROR;

  *value &= LSM6DSL_ACC_GYRO_DEN_EDGE_EN_MASK; //mask

  return MEMS_SUCCESS;
}

/*******************************************************************************
* Function Name  : LSM6DSL_ACC_GYRO_W_HPM_G
* Description    : Write HPM_G
* Input          : LSM6DSL_ACC_GYRO_HPM_G_t
* Output         : None
* Return         : Status [MEMS_ERROR, MEMS_SUCCESS]
*******************************************************************************/
mems_status_t  LSM6DSL_ACC_GYRO_W_HPM_G(LSM6DSL_ACC_GYRO_HPM_G_t newValue)
{
  uint8_t value;

  if( !LSM6DSL_ACC_GYRO_ReadReg(LSM6DSL_ACC_GYRO_CTRL7_G, &value, 1) )
    return MEMS_ERROR;

  value &= ~LSM6DSL_ACC_GYRO_HPM_G_MASK;
  value |= newValue;

  if( !LSM6DSL_ACC_GYRO_WriteReg(LSM6DSL_ACC_GYRO_CTRL7_G, &value, 1) )
    return MEMS_ERROR;

  return MEMS_SUCCESS;
}

/*******************************************************************************
* Function Name  : LSM6DSL_ACC_GYRO_R_HPM_G
* Description    : Read HPM_G
* Input          : Pointer to LSM6DSL_ACC_GYRO_HPM_G_t
* Output         : Status of HPM_G see LSM6DSL_ACC_GYRO_HPM_G_t
* Return         : Status [MEMS_ERROR, MEMS_SUCCESS]
*******************************************************************************/
mems_status_t LSM6DSL_ACC_GYRO_R_HPM_G(LSM6DSL_ACC_GYRO_HPM_G_t *value)
{
 if( !LSM6DSL_ACC_GYRO_ReadReg(LSM6DSL_ACC_GYRO_CTRL7_G, (uint8_t *)value, 1) )
    return MEMS_ERROR;

  *value &= LSM6DSL_ACC_GYRO_HPM_G_MASK; //mask

  return MEMS_SUCCESS;
}

/*******************************************************************************
* Function Name  : LSM6DSL_ACC_GYRO_W_RoundingOnStatusRegisters
* Description    : Write HPM_G
* Input          : LSM6DSL_ACC_GYRO_RND_STATUS_t
* Output         : None
* Return         : Status [MEMS_ERROR, MEMS_SUCCESS]
*******************************************************************************/
mems_status_t  LSM6DSL_ACC_GYRO_W_RoundingOnStatusRegisters(LSM6DSL_ACC_GYRO_RND_STATUS_t newValue)
{
  uint8_t value;

  if( !LSM6DSL_ACC_GYRO_ReadReg(LSM6DSL_ACC_GYRO_CTRL7_G, &value, 1) )
    return MEMS_ERROR;

  value &= ~LSM6DSL_ACC_GYRO_RND_STATUS_MASK;
  value |= newValue;

  if( !LSM6DSL_ACC_GYRO_WriteReg(LSM6DSL_ACC_GYRO_CTRL7_G, &value, 1) )
    return MEMS_ERROR;

  return MEMS_SUCCESS;
}

/*******************************************************************************
* Function Name  : LSM6DSL_ACC_GYRO_R_RoundingOnStatusRegisters
* Description    : Read HPM_G
* Input          : Pointer to LSM6DSL_ACC_GYRO_RND_STATUS_t
* Output         : Status of HPM_G see LSM6DSL_ACC_GYRO_RND_STATUS_t
* Return         : Status [MEMS_ERROR, MEMS_SUCCESS]
*******************************************************************************/
mems_status_t LSM6DSL_ACC_GYRO_R_RoundingOnStatusRegisters(LSM6DSL_ACC_GYRO_RND_STATUS_t *value)
{
 if( !LSM6DSL_ACC_GYRO_ReadReg(LSM6DSL_ACC_GYRO_CTRL7_G, (uint8_t *)value, 1))
    return MEMS_ERROR;

  *value &= LSM6DSL_ACC_GYRO_RND_STATUS_MASK; //mask

  return MEMS_SUCCESS;
}

/*******************************************************************************
* Function Name  : LSM6DSL_ACC_GYRO_W_HPFilter_En
* Description    : Write HP_EN
* Input          : LSM6DSL_ACC_GYRO_HP_EN_t
* Output         : None
* Return         : Status [MEMS_ERROR, MEMS_SUCCESS]
*******************************************************************************/
mems_status_t  LSM6DSL_ACC_GYRO_W_HPFilter_En(LSM6DSL_ACC_GYRO_HP_EN_t newValue)
{
  uint8_t value;

  if( !LSM6DSL_ACC_GYRO_ReadReg(LSM6DSL_ACC_GYRO_CTRL7_G, &value, 1) )
    return MEMS_ERROR;

  value &= ~LSM6DSL_ACC_GYRO_HP_EN_MASK;
  value |= newValue;

  if( !LSM6DSL_ACC_GYRO_WriteReg(LSM6DSL_ACC_GYRO_CTRL7_G, &value, 1) )
    return MEMS_ERROR;

  return MEMS_SUCCESS;
}

/*******************************************************************************
* Function Name  : LSM6DSL_ACC_GYRO_R_HPFilter_En
* Description    : Read HP_EN
* Input          : Pointer to LSM6DSL_ACC_GYRO_HP_EN_t
* Output         : Status of HP_EN see LSM6DSL_ACC_GYRO_HP_EN_t
* Return         : Status [MEMS_ERROR, MEMS_SUCCESS]
*******************************************************************************/
mems_status_t LSM6DSL_ACC_GYRO_R_HPFilter_En(LSM6DSL_ACC_GYRO_HP_EN_t *value)
{
 if( !LSM6DSL_ACC_GYRO_ReadReg(LSM6DSL_ACC_GYRO_CTRL7_G, (uint8_t *)value, 1) )
    return MEMS_ERROR;

  *value &= LSM6DSL_ACC_GYRO_HP_EN_MASK; //mask

  return MEMS_SUCCESS;
}
/*******************************************************************************
* Function Name  : LSM6DSL_ACC_GYRO_W_LP_Mode
* Description    : Write LP_EN
* Input          : LSM6DSL_ACC_GYRO_LP_EN_t
* Output         : None
* Return         : Status [MEMS_ERROR, MEMS_SUCCESS]
*******************************************************************************/
mems_status_t  LSM6DSL_ACC_GYRO_W_LP_Mode(LSM6DSL_ACC_GYRO_LP_EN_t newValue)
{
  uint8_t value;

  if( !LSM6DSL_ACC_GYRO_ReadReg(LSM6DSL_ACC_GYRO_CTRL7_G, &value, 1) )
    return MEMS_ERROR;

  value &= ~LSM6DSL_ACC_GYRO_LP_EN_MASK;
  value |= newValue;

  if( !LSM6DSL_ACC_GYRO_WriteReg(LSM6DSL_ACC_GYRO_CTRL7_G, &value, 1) )
    return MEMS_ERROR;

  return MEMS_SUCCESS;
}

/*******************************************************************************
* Function Name  : LSM6DSL_ACC_GYRO_R_LP_Mode
* Description    : Read LP_EN
* Input          : Pointer to LSM6DSL_ACC_GYRO_LP_EN_t
* Output         : Status of LP_EN see LSM6DSL_ACC_GYRO_LP_EN_t
* Return         : Status [MEMS_ERROR, MEMS_SUCCESS]
*******************************************************************************/
mems_status_t LSM6DSL_ACC_GYRO_R_LP_Mode(LSM6DSL_ACC_GYRO_LP_EN_t *value)
{
 if( !LSM6DSL_ACC_GYRO_ReadReg(LSM6DSL_ACC_GYRO_CTRL7_G, (uint8_t *)value, 1) )
    return MEMS_ERROR;

  *value &= LSM6DSL_ACC_GYRO_LP_EN_MASK; //mask

  return MEMS_SUCCESS;
}

/*******************************************************************************
* Function Name  : LSM6DSL_ACC_GYRO_W_ROUNDING_STATUS
* Description    : Write ROUNDING_STATUS
* Input          : LSM6DSL_ACC_GYRO_ROUNDING_STATUS_t
* Output         : None
* Return         : Status [MEMS_ERROR, MEMS_SUCCESS]
*******************************************************************************/
mems_status_t  LSM6DSL_ACC_GYRO_W_ROUNDING_STATUS(LSM6DSL_ACC_GYRO_ROUNDING_STATUS_t newValue)
{
  uint8_t value;

  if( !LSM6DSL_ACC_GYRO_ReadReg(LSM6DSL_ACC_GYRO_CTRL7_G, &value, 1) )
    return MEMS_ERROR;

  value &= ~LSM6DSL_ACC_GYRO_ROUNDING_STATUS_MASK;
  value |= newValue;

  if( !LSM6DSL_ACC_GYRO_WriteReg(LSM6DSL_ACC_GYRO_CTRL7_G, &value, 1) )
    return MEMS_ERROR;

  return MEMS_SUCCESS;
}

/*******************************************************************************
* Function Name  : LSM6DSL_ACC_GYRO_R_ROUNDING_STATUS
* Description    : Read ROUNDING_STATUS
* Input          : Pointer to LSM6DSL_ACC_GYRO_ROUNDING_STATUS_t
* Output         : Status of ROUNDING_STATUS see LSM6DSL_ACC_GYRO_ROUNDING_STATUS_t
* Return         : Status [MEMS_ERROR, MEMS_SUCCESS]
*******************************************************************************/
mems_status_t LSM6DSL_ACC_GYRO_R_ROUNDING_STATUS(LSM6DSL_ACC_GYRO_ROUNDING_STATUS_t *value)
{
 if( !LSM6DSL_ACC_GYRO_ReadReg(LSM6DSL_ACC_GYRO_CTRL7_G, (uint8_t *)value, 1) )
    return MEMS_ERROR;

  *value &= LSM6DSL_ACC_GYRO_ROUNDING_STATUS_MASK; //mask

  return MEMS_SUCCESS;
}

/*******************************************************************************
* Function Name  : LSM6DSL_ACC_GYRO_W_HP_G_RST
* Description    : Write HP_G_RST
* Input          : LSM6DSL_ACC_GYRO_HP_G_RST_t
* Output         : None
* Return         : Status [MEMS_ERROR, MEMS_SUCCESS]
*******************************************************************************/
mems_status_t  LSM6DSL_ACC_GYRO_W_HP_G_RST(LSM6DSL_ACC_GYRO_HP_G_RST_t newValue)
{
  uint8_t value;

  if( !LSM6DSL_ACC_GYRO_ReadReg(LSM6DSL_ACC_GYRO_CTRL7_G, &value, 1) )
    return MEMS_ERROR;

  value &= ~LSM6DSL_ACC_GYRO_HP_G_RST_MASK;
  value |= newValue;

  if( !LSM6DSL_ACC_GYRO_WriteReg(LSM6DSL_ACC_GYRO_CTRL7_G, &value, 1) )
    return MEMS_ERROR;

  return MEMS_SUCCESS;
}

/*******************************************************************************
* Function Name  : LSM6DSL_ACC_GYRO_R_HP_G_RST
* Description    : Read HP_G_RST
* Input          : Pointer to LSM6DSL_ACC_GYRO_HP_G_RST_t
* Output         : Status of HP_G_RST see LSM6DSL_ACC_GYRO_HP_G_RST_t
* Return         : Status [MEMS_ERROR, MEMS_SUCCESS]
*******************************************************************************/
mems_status_t LSM6DSL_ACC_GYRO_R_HP_G_RST(LSM6DSL_ACC_GYRO_HP_G_RST_t *value)
{
 if( !LSM6DSL_ACC_GYRO_ReadReg(LSM6DSL_ACC_GYRO_CTRL7_G, (uint8_t *)value, 1) )
    return MEMS_ERROR;

  *value &= LSM6DSL_ACC_GYRO_HP_G_RST_MASK; //mask

  return MEMS_SUCCESS;
}

/*******************************************************************************
* Function Name  : LSM6DSL_ACC_GYRO_W_InComposit
* Description    : Write INPUT_COMPOSITE
* Input          : LSM6DSL_ACC_GYRO_IN_COMP_t
* Output         : None
* Return         : Status [MEMS_ERROR, MEMS_SUCCESS]
*******************************************************************************/
mems_status_t  LSM6DSL_ACC_GYRO_W_InComposit(LSM6DSL_ACC_GYRO_IN_COMP_t newValue)
{
  uint8_t value;

  if( !LSM6DSL_ACC_GYRO_ReadReg(LSM6DSL_ACC_GYRO_CTRL8_XL, &value, 1) )
    return MEMS_ERROR;

  value &= ~LSM6DSL_ACC_GYRO_IN_COMP_MASK;
  value |= newValue;

  if( !LSM6DSL_ACC_GYRO_WriteReg(LSM6DSL_ACC_GYRO_CTRL8_XL, &value, 1) )
    return MEMS_ERROR;

  return MEMS_SUCCESS;
}

/*******************************************************************************
* Function Name  : LSM6DSL_ACC_GYRO_R_InComposit
* Description    : Read INPUT_COMPOSITE
* Input          : Pointer to LSM6DSL_ACC_GYRO_IN_COMP_t
* Output         : Status of INPUT_COMPOSITE see LSM6DSL_ACC_GYRO_IN_COMP_t
* Return         : Status [MEMS_ERROR, MEMS_SUCCESS]
*******************************************************************************/
mems_status_t LSM6DSL_ACC_GYRO_R_InComposit(LSM6DSL_ACC_GYRO_IN_COMP_t *value)
{
 if( !LSM6DSL_ACC_GYRO_ReadReg(LSM6DSL_ACC_GYRO_CTRL8_XL, (uint8_t *)value, 1) )
    return MEMS_ERROR;

  *value &= LSM6DSL_ACC_GYRO_IN_COMP_MASK; //mask

  return MEMS_SUCCESS;
}

/*******************************************************************************
* Function Name  : LSM6DSL_ACC_GYRO_W_HPfilterReference
* Description    : Write HP_REF_MODE
* Input          : LSM6DSL_ACC_GYRO_HP_REF_MODE_t
* Output         : None
* Return         : Status [MEMS_ERROR, MEMS_SUCCESS]
*******************************************************************************/
mems_status_t  LSM6DSL_ACC_GYRO_W_HPfilterReference(LSM6DSL_ACC_GYRO_HP_REF_MODE_t newValue)
{
  uint8_t value;

  if( !LSM6DSL_ACC_GYRO_ReadReg(LSM6DSL_ACC_GYRO_CTRL8_XL, &value, 1) )
    return MEMS_ERROR;

  value &= ~LSM6DSL_ACC_GYRO_HP_REF_MODE_MASK;
  value |= newValue;

  if( !LSM6DSL_ACC_GYRO_WriteReg(LSM6DSL_ACC_GYRO_CTRL8_XL, &value, 1) )
    return MEMS_ERROR;

  return MEMS_SUCCESS;
}

/*******************************************************************************
* Function Name  : LSM6DSL_ACC_GYRO_R_HPfilterReference
* Description    : Read HP_REF_MODE
* Input          : Pointer to LSM6DSL_ACC_GYRO_HP_REF_MODE_t
* Output         : Status of HP_REF_MODE see LSM6DSL_ACC_GYRO_HP_REF_MODE_t
* Return         : Status [MEMS_ERROR, MEMS_SUCCESS]
*******************************************************************************/
mems_status_t LSM6DSL_ACC_GYRO_R_HPfilterReference(LSM6DSL_ACC_GYRO_HP_REF_MODE_t *value)
{
 if( !LSM6DSL_ACC_GYRO_ReadReg(LSM6DSL_ACC_GYRO_CTRL8_XL, (uint8_t *)value, 1) )
    return MEMS_ERROR;

  *value &= LSM6DSL_ACC_GYRO_HP_REF_MODE_MASK; //mask

  return MEMS_SUCCESS;
}

/*******************************************************************************
* Function Name  : LSM6DSL_ACC_GYRO_W_HPCF_XL
* Description    : Write HPCF_XL
* Input          : LSM6DSL_ACC_GYRO_HPCF_XL_t
* Output         : None
* Return         : Status [MEMS_ERROR, MEMS_SUCCESS]
*******************************************************************************/
mems_status_t  LSM6DSL_ACC_GYRO_W_HPCF_XL(LSM6DSL_ACC_GYRO_HPCF_XL_t newValue)
{
  uint8_t value;

  if( !LSM6DSL_ACC_GYRO_ReadReg(LSM6DSL_ACC_GYRO_CTRL8_XL, &value, 1) )
    return MEMS_ERROR;

  value &= ~LSM6DSL_ACC_GYRO_HPCF_XL_MASK;
  value |= newValue;

  if( !LSM6DSL_ACC_GYRO_WriteReg(LSM6DSL_ACC_GYRO_CTRL8_XL, &value, 1) )
    return MEMS_ERROR;

  return MEMS_SUCCESS;
}

/*******************************************************************************
* Function Name  : LSM6DSL_ACC_GYRO_R_HPCF_XL
* Description    : Read HPCF_XL
* Input          : Pointer to LSM6DSL_ACC_GYRO_HPCF_XL_t
* Output         : Status of HPCF_XL see LSM6DSL_ACC_GYRO_HPCF_XL_t
* Return         : Status [MEMS_ERROR, MEMS_SUCCESS]
*******************************************************************************/
mems_status_t LSM6DSL_ACC_GYRO_R_HPCF_XL(LSM6DSL_ACC_GYRO_HPCF_XL_t *value)
{
 if( !LSM6DSL_ACC_GYRO_ReadReg(LSM6DSL_ACC_GYRO_CTRL8_XL, (uint8_t *)value, 1) )
    return MEMS_ERROR;

  *value &= LSM6DSL_ACC_GYRO_HPCF_XL_MASK; //mask

  return MEMS_SUCCESS;
}

/*******************************************************************************
* Function Name  : LSM6DSL_ACC_GYRO_W_LowPassFiltSel_XL
* Description    : Write LPF2_XL_EN
* Input          : LSM6DSL_ACC_GYRO_LPF2_XL_t
* Output         : None
* Return         : Status [MEMS_ERROR, MEMS_SUCCESS]
*******************************************************************************/
mems_status_t  LSM6DSL_ACC_GYRO_W_LowPassFiltSel_XL(LSM6DSL_ACC_GYRO_LPF2_XL_t newValue)
{
  uint8_t value;

  if( !LSM6DSL_ACC_GYRO_ReadReg(LSM6DSL_ACC_GYRO_CTRL8_XL, &value, 1) )
    return MEMS_ERROR;

  value &= ~LSM6DSL_ACC_GYRO_LPF2_XL_MASK;
  value |= newValue;

  if( !LSM6DSL_ACC_GYRO_WriteReg(LSM6DSL_ACC_GYRO_CTRL8_XL, &value, 1) )
    return MEMS_ERROR;

  return MEMS_SUCCESS;
}

/*******************************************************************************
* Function Name  : LSM6DSL_ACC_GYRO_R_LowPassFiltSel_XL
* Description    : Read LPF2_XL_EN
* Input          : Pointer to LSM6DSL_ACC_GYRO_LPF2_XL_t
* Output         : Status of LPF2_XL_EN see LSM6DSL_ACC_GYRO_LPF2_XL_t
* Return         : Status [MEMS_ERROR, MEMS_SUCCESS]
*******************************************************************************/
mems_status_t LSM6DSL_ACC_GYRO_R_LowPassFiltSel_XL(LSM6DSL_ACC_GYRO_LPF2_XL_t *value)
{
 if( !LSM6DSL_ACC_GYRO_ReadReg(LSM6DSL_ACC_GYRO_CTRL8_XL, (uint8_t *)value, 1) )
    return MEMS_ERROR;

  *value &= LSM6DSL_ACC_GYRO_LPF2_XL_MASK; //mask

  return MEMS_SUCCESS;
}
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
