vrbadev/Gloves-Equipped-with-Motion-Sensors-Bachelor-Project-HW-FW-SW/Firmware/uVision/lib_hal/src/sleep.c

/******************** (C) COPYRIGHT 2018 STMicroelectronics ********************
* File Name          : sleep.c
* Author             : AMS - RF-Application Team
* Version            : V1.2.1
* Date               : 24-October-2018
* Description        : BlueNRG Sleep management
********************************************************************************
* THE PRESENT FIRMWARE WHICH IS FOR GUIDANCE ONLY AIMS AT PROVIDING CUSTOMERS
* WITH CODING INFORMATION REGARDING THEIR PRODUCTS IN ORDER FOR THEM TO SAVE TIME.
* AS A RESULT, STMICROELECTRONICS SHALL NOT BE HELD LIABLE FOR ANY DIRECT,
* INDIRECT OR CONSEQUENTIAL DAMAGES WITH RESPECT TO ANY CLAIMS ARISING FROM THE
* CONTENT OF SUCH FIRMWARE AND/OR THE USE MADE BY CUSTOMERS OF THE CODING
* INFORMATION CONTAINED HEREIN IN CONNECTION WITH THEIR PRODUCTS.
*******************************************************************************/
#include <stdint.h>
#include <stdlib.h>
#include <string.h>
#include "BlueNRG_x_device.h"
#include "../../inc/BlueNRG1_conf.h"
#include "sleep.h"
#include "misc.h"
#include "miscutil.h"

#undef DEBUG_SLEEP_MODE
#define DEBUG_SLEEP_MODE 0

#define MIN(a,b) ((a) < (b) )? (a) : (b)

#ifndef SAVE_CONTEXT_ON_CSTACK
#define SAVE_CONTEXT_ON_CSTACK 1
#endif

#if SAVE_CONTEXT_ON_CSTACK
#define CTXT
#else
#define CTXT   static
#endif

#define ATOMIC_SECTION_BEGIN() uint32_t uwPRIMASK_Bit = __get_PRIMASK(); \
                                __disable_irq(); \
/* Must be called in the same or in a lower scope of ATOMIC_SECTION_BEGIN */
#define ATOMIC_SECTION_END() __set_PRIMASK(uwPRIMASK_Bit)

#define SHPR3_REG 0xE000ED20

#define WAKENED_FROM_BOR          0x03
#define WAKENED_FROM_POR          0x05
#define WAKENED_FROM_IO9          0x09
#define WAKENED_FROM_IO10         0x11
#define WAKENED_FROM_IO11         0x21
#define WAKENED_FROM_IO12         0x41
#define WAKENED_FROM_IO13         0x81
#define WAKENED_FROM_BLUE_TIMER1  0x101
#define WAKENED_FROM_BLUE_TIMER2  0x401

#define LOW_POWER_STANDBY  0x03

#define BLUE_CURRENT_TIME_REG 0x48000010

uint32_t cStackPreamble[CSTACK_PREAMBLE_NUMBER];
volatile uint32_t* ptr ;

#ifdef DEBUG_SLEEP_MODE
uint32_t sleepMode_selected[4]={0,};
#endif

#ifndef SLEEP_SAVE_N_RESTORE_UART
#define SLEEP_SAVE_N_RESTORE_UART 1
#endif
#ifndef SLEEP_SAVE_N_RESTORE_SPI
#define SLEEP_SAVE_N_RESTORE_SPI 1
#endif
#ifndef SLEEP_SAVE_N_RESTORE_I2C
#define SLEEP_SAVE_N_RESTORE_I2C 1
#endif
#ifndef SLEEP_SAVE_N_RESTORE_RTC
#define SLEEP_SAVE_N_RESTORE_RTC 1
#endif
#ifndef SLEEP_SAVE_N_RESTORE_MFTX1
#define SLEEP_SAVE_N_RESTORE_MFTX1 1
#endif
#ifndef SLEEP_SAVE_N_RESTORE_MFTX2
#define SLEEP_SAVE_N_RESTORE_MFTX2 1
#endif
#ifndef SLEEP_SAVE_N_RESTORE_WDG
#define SLEEP_SAVE_N_RESTORE_WDG 1
#endif
#ifndef SLEEP_SAVE_N_RESTORE_DMA
#define SLEEP_SAVE_N_RESTORE_DMA 1
#endif
#ifndef SLEEP_SAVE_N_RESTORE_ADC
#define SLEEP_SAVE_N_RESTORE_ADC 1
#endif

WEAK_FUNCTION(SleepModes App_SleepMode_Check(SleepModes sleepMode))
{
  return SLEEPMODE_NOTIMER;
}
WEAK_FUNCTION(SleepModes BlueNRG_Stack_Perform_Deep_Sleep_Check(void))
{
  return SLEEPMODE_NOTIMER;
}

#ifndef FORCE_CORE_TO_16MHZ
/* Macros to calculate the time diff between two machine times */
#define INT_ASR(X,Y)    ((X) >> (Y))
#define INT_SHIFT_R(X, Y) ((int32_t)INT_ASR((int32_t)(X),(Y)))
#define TIME24_DIFF(TA, TB)       (INT_SHIFT_R((uint32_t)((uint32_t)((TA) - (TB)) << 8), 8))


/* Function to evaluate if the application has enough time to switch the frequency */
static void frequency_switch(void)
{
  uint32_t currTimeTHR;
  int32_t time_diff = -1;
  volatile uint8_t reset_reason;

  /* Get the reset reason */
  reset_reason = SysCtrl_GetWakeupResetReason();
  
  /* If the BLE radio is NOT active or the Wakeup comes from radio transaction, the frequency switch is safe */
  if (!((reset_reason ==  RESET_BLE_WAKEUP_FROM_TIMER1) || ((__blue_RAM.BlueGlobVar.Config & 8U) == 0))) { //    ((*(volatile uint32_t*)0x200000C0 & 8U) == 0U))) {
    /* Check if the next transaction is enough in the future */
    currTimeTHR = BLUE_CTRL->CURRENT_TIME;
    time_diff = abs(TIME24_DIFF(rfTimeout, currTimeTHR));
    if (time_diff <= 32) { 
      currTimeTHR = BLUE_CTRL->CURRENT_TIME + 45;
      /* Wait 45 clock tick until the first SPI transaction is executed */
      while (BLUE_CTRL->CURRENT_TIME <= currTimeTHR);
    }
  }

  AHBUPCONV->COMMAND = 0x15;
}
#endif


static void BlueNRG_InternalSleep(SleepModes sleepMode, uint8_t gpioWakeBitMask)
{
  uint32_t savedCurrentTime, nvicPendingMask, ioValue, ioLevel, ioEnabled;
  PartInfoType partInfo;
  uint8_t i;
  
  /* Variables used to store system peripheral registers in order to restore the state after
   exit from sleep mode */

/* System Control saved */
  CTXT uint32_t SYS_Ctrl_saved;
  /* NVIC Information Saved */
  CTXT uint32_t NVIC_ISER_saved, NVIC_IPR_saved[8], PENDSV_SYSTICK_IPR_saved;
  /* CKGEN SOC Enabled */
  CTXT uint32_t CLOCK_EN_saved;
  /* GPIO Information saved */
  CTXT uint32_t GPIO_DATA_saved, GPIO_OEN_saved, GPIO_PE_saved, GPIO_DS_saved, GPIO_IS_saved, GPIO_IBE_saved;
  CTXT uint32_t GPIO_IEV_saved, GPIO_IE_saved, GPIO_MODE0_saved, GPIO_MODE1_saved, GPIO_IOSEL_MFTX_saved;
#ifdef BLUENRG2_DEVICE
  CTXT uint32_t GPIO_MODE2_saved, GPIO_MODE3_saved;
#endif
#if SLEEP_SAVE_N_RESTORE_UART
  /* UART Information saved */
  CTXT uint32_t UART_TIMEOUT_saved, UART_LCRH_RX_saved, UART_IBRD_saved, UART_FBRD_saved;
  CTXT uint32_t UART_LCRH_TX_saved, UART_CR_saved, UART_IFLS_saved, UART_IMSC_saved;
  CTXT uint32_t UART_DMACR_saved, UART_XFCR_saved, UART_XON1_saved, UART_XON2_saved;
  CTXT uint32_t UART_XOFF1_saved, UART_XOFF2_saved;
#endif
#if SLEEP_SAVE_N_RESTORE_SPI
  /* SPI Information saved */
  CTXT uint32_t SPI_CR0_saved, SPI_CR1_saved, SPI_CPSR_saved, SPI_IMSC_saved, SPI_DMACR_saved;
  CTXT uint32_t SPI_RXFRM_saved, SPI_CHN_saved, SPI_WDTXF_saved;
#endif
#if SLEEP_SAVE_N_RESTORE_I2C
  /* I2C Information saved */
  CTXT uint32_t I2C_CR_saved[2], I2C_SCR_saved[2], I2C_TFTR_saved[2], I2C_RFTR_saved[2];
  CTXT uint32_t I2C_DMAR_saved[2], I2C_BRCR_saved[2], I2C_IMSCR_saved[2], I2C_THDDAT_saved[2];
  CTXT uint32_t I2C_THDSTA_FST_STD_saved[2], I2C_TSUSTA_FST_STD_saved[2];
#endif
  /* RNG Information saved */
  CTXT uint32_t RNG_CR_saved;
  /* SysTick Information saved */
  CTXT uint32_t SYST_CSR_saved, SYST_RVR_saved;
#if SLEEP_SAVE_N_RESTORE_RTC
  /* RTC Information saved */
  CTXT uint32_t RTC_CWDMR_saved, RTC_CWDLR_saved, RTC_CWYMR_saved, RTC_CWYLR_saved, RTC_CTCR_saved;
  CTXT uint32_t RTC_IMSC_saved, RTC_TCR_saved, RTC_TLR1_saved, RTC_TLR2_saved, RTC_TPR1_saved;
  CTXT uint32_t RTC_TPR2_saved, RTC_TPR3_saved, RTC_TPR4_saved;
#endif
  /* MFTX Information saved */
#if SLEEP_SAVE_N_RESTORE_MFTX1
  CTXT uint32_t T1CRA_saved, T1CRB_saved, T1PRSC_saved, T1CKC_saved, T1MCTRL_saved, T1ICTRL_saved;
#endif
#if SLEEP_SAVE_N_RESTORE_MFTX2  
  CTXT uint32_t T2CRA_saved, T2CRB_saved, T2PRSC_saved, T2CKC_saved, T2MCTRL_saved, T2ICTRL_saved;
#endif
#if SLEEP_SAVE_N_RESTORE_WDG
  /* WDT Information saved */
  CTXT uint32_t WDG_LR_saved, WDG_CR_saved, WDG_LOCK_saved;
#endif
#if SLEEP_SAVE_N_RESTORE_DMA
  /* DMA channel [0..7] Information saved */
  CTXT uint32_t DMA_CCR_saved[8], DMA_CNDTR_saved[8], DMA_CPAR_saved[8], DMA_CMAR[8];
#endif
#if SLEEP_SAVE_N_RESTORE_ADC
  /* ADC Information saved */
  CTXT uint32_t ADC_CTRL_saved, ADC_CONF_saved, ADC_IRQMASK_saved, ADC_OFFSET_LSB_saved, ADC_OFFSET_MSB_saved;
  CTXT uint32_t ADC_THRESHOLD_HI_saved, ADC_THRESHOLD_LO_saved;
#endif
  /* FlASH Config saved */
  CTXT uint32_t FLASH_CONFIG_saved;
  /* PKA Information saved */
  CTXT uint32_t PKA_IEN_saved;

  /* Get partInfo */
  HAL_GetPartInfo(&partInfo);

  /* Save the peripherals configuration */
  /* System Control */
  SYS_Ctrl_saved = SYSTEM_CTRL->CTRL;
  /* FLASH CONFIG */
  FLASH_CONFIG_saved = FLASH->CONFIG;
  /* NVIC */
  NVIC_ISER_saved = NVIC->ISER[0];

  // Issue with Atollic compiler
//  memcpy(NVIC_IPR_saved, (void const *)NVIC->IP, sizeof(NVIC_IPR_saved));
  for (i=0; i<8; i++) {
  	NVIC_IPR_saved[i] = NVIC->IP[i];
  }


  PENDSV_SYSTICK_IPR_saved = *(volatile uint32_t *)SHPR3_REG;
  /* CKGEN SOC Enabled */
  CLOCK_EN_saved = CKGEN_SOC->CLOCK_EN;
  /* GPIO */
  GPIO_DATA_saved = GPIO->DATA;
  GPIO_OEN_saved = GPIO->OEN;
  GPIO_PE_saved = GPIO->PE;
  GPIO_DS_saved = GPIO->DS;
  GPIO_IS_saved = GPIO->IS;
  GPIO_IBE_saved = GPIO->IBE;
  GPIO_IEV_saved = GPIO->IEV;
  GPIO_IE_saved = GPIO->IE;
  GPIO_MODE0_saved = GPIO->MODE0;
  GPIO_MODE1_saved = GPIO->MODE1;
#ifdef BLUENRG2_DEVICE
  GPIO_MODE2_saved = GPIO->MODE2;
  GPIO_MODE3_saved = GPIO->MODE3;
#endif
  GPIO_IOSEL_MFTX_saved = GPIO->MFTX;
#if SLEEP_SAVE_N_RESTORE_UART
  /* UART */
  UART_TIMEOUT_saved = UART->TIMEOUT;
  UART_LCRH_RX_saved = UART->LCRH_RX;
  UART_IBRD_saved = UART->IBRD;
  UART_FBRD_saved = UART->FBRD;
  UART_LCRH_TX_saved =  UART->LCRH_TX;
  UART_CR_saved = UART->CR;
  UART_IFLS_saved = UART->IFLS;
  UART_IMSC_saved = UART->IMSC;
  UART_DMACR_saved = UART->DMACR;
  UART_XFCR_saved = UART->XFCR;
  UART_XON1_saved = UART->XON1;
  UART_XON2_saved = UART->XON2;
  UART_XOFF1_saved = UART->XOFF1;
  UART_XOFF2_saved = UART->XOFF2;
#endif
#if SLEEP_SAVE_N_RESTORE_SPI
  /* SPI */
  SPI_CR0_saved = SPI->CR0; 
  SPI_CR1_saved = SPI->CR1;
  SPI_CPSR_saved = SPI->CPSR;
  SPI_IMSC_saved = SPI->IMSC;
  SPI_DMACR_saved = SPI->DMACR;
  SPI_RXFRM_saved = SPI->RXFRM;
  SPI_CHN_saved = SPI->CHN;
  SPI_WDTXF_saved = SPI->WDTXF;
#endif
#if SLEEP_SAVE_N_RESTORE_I2C
  /* I2C */
  for (i=0; i<2; i++) {
    I2C_Type *I2Cx = (I2C_Type*)(I2C2_BASE+ 0x100000*i);
    I2C_CR_saved[i] = I2Cx->CR;
    I2C_SCR_saved[i] = I2Cx->SCR;
    I2C_TFTR_saved[i] = I2Cx->TFTR;
    I2C_RFTR_saved[i] = I2Cx->RFTR;
    I2C_DMAR_saved[i] = I2Cx->DMAR;
    I2C_BRCR_saved[i] = I2Cx->BRCR;
    I2C_IMSCR_saved[i] = I2Cx->IMSCR;
    I2C_THDDAT_saved[i] = I2Cx->THDDAT;
    I2C_THDSTA_FST_STD_saved[i] = I2Cx->THDSTA_FST_STD;
    I2C_TSUSTA_FST_STD_saved[i] = I2Cx->TSUSTA_FST_STD;
  }
#endif
  /* RNG */
  RNG_CR_saved = RNG->CR;
#if SLEEP_SAVE_N_RESTORE_RTC
  /* RTC */
  RTC_CWDMR_saved = RTC->CWDMR;
  RTC_CWDLR_saved = RTC->CWDLR;
  RTC_CWYMR_saved = RTC->CWYMR;
  RTC_CWYLR_saved = RTC->CWYLR;
  RTC_CTCR_saved = RTC->CTCR;
  RTC_IMSC_saved = RTC->IMSC;
  RTC_TCR_saved = RTC->TCR;
  RTC_TLR1_saved = RTC->TLR1;
  RTC_TLR2_saved = RTC->TLR2;
  RTC_TPR1_saved = RTC->TPR1;
  RTC_TPR2_saved = RTC->TPR2;
  RTC_TPR3_saved = RTC->TPR3;
  RTC_TPR4_saved = RTC->TPR4; 
#endif
  /* MFTX */
#if SLEEP_SAVE_N_RESTORE_MFTX1
  T1CRA_saved = MFT1->TNCRA;
  T1CRB_saved = MFT1->TNCRB;
  T1PRSC_saved = MFT1->TNPRSC;
  T1CKC_saved = MFT1->TNCKC;
  T1MCTRL_saved = MFT1->TNMCTRL;
  T1ICTRL_saved = MFT1->TNICTRL;
#endif
#if SLEEP_SAVE_N_RESTORE_MFTX2
  T2CRA_saved = MFT2->TNCRA;
  T2CRB_saved = MFT2->TNCRB;
  T2PRSC_saved = MFT2->TNPRSC;
  T2CKC_saved = MFT2->TNCKC;
  T2MCTRL_saved = MFT2->TNMCTRL;
  T2ICTRL_saved = MFT2->TNICTRL;
#endif
  /* SysTick */
  SYST_CSR_saved = SysTick->CTRL;
  SYST_RVR_saved = SysTick->LOAD;
#if SLEEP_SAVE_N_RESTORE_WDG
  /* WDT */
  WDG_LR_saved = WDG->LR;
  WDG_CR_saved = WDG->CR;
  if(WDG->LOCK == 0) {
    WDG_LOCK_saved = 0x1ACCE551;
  } else {
    WDG_LOCK_saved = 0;
  }
#endif
#if SLEEP_SAVE_N_RESTORE_DMA
  /* DMA */
  for (i=0; i<8; i++) {
    DMA_CH_Type *DMAx = (DMA_CH_Type*)(DMA_CH0_BASE+ 0x14*i);
    DMA_CNDTR_saved[i] = DMAx->CNDTR;
    DMA_CCR_saved[i] = DMAx->CCR;
    DMA_CPAR_saved[i] = DMAx->CPAR;
    DMA_CMAR[i] = DMAx->CMAR;
  }
#endif
#if SLEEP_SAVE_N_RESTORE_ADC
  /* ADC */
  ADC_CONF_saved = ADC->CONF;
  ADC_IRQMASK_saved = ADC->IRQMASK;
  ADC_OFFSET_MSB_saved = ADC->OFFSET_MSB;
  ADC_OFFSET_LSB_saved = ADC->OFFSET_LSB;
  ADC_THRESHOLD_HI_saved = ADC->THRESHOLD_HI;
  ADC_THRESHOLD_LO_saved = ADC->THRESHOLD_LO;
  ADC_CTRL_saved = ADC->CTRL;
#endif

  /* PKA */
  PKA_IEN_saved = PKA->IEN;
  
  // Enable the STANDBY mode 
  if (sleepMode == SLEEPMODE_NOTIMER) {
    BLUE_CTRL->TIMEOUT |= LOW_POWER_STANDBY<<28;
  }

  //Save the CSTACK number of words that will be restored at wakeup reset
  i = 0;
  ptr = __vector_table[0].__ptr ;
  ptr -= CSTACK_PREAMBLE_NUMBER;
  do {
    cStackPreamble[i] = *ptr;
    i++;
    ptr++;
  } while (i < CSTACK_PREAMBLE_NUMBER); 

  if (((partInfo.die_major<<4)|(partInfo.die_cut)) >= WA_DEVICE_VERSION) {
    /* Lock the flash */
    flash_sw_lock = FLASH_LOCK_WORD;
    /* Disable BOR */
    SET_BORconfigStatus(FALSE);
  }
  /* Copy of the BLUE_CTRL TIMEOUT register in RAM */
  rfTimeout = BLUE_CTRL->TIMEOUT;
 
  /* If the wakeup source is already active, we can skip the sleep to speed-up 
     the application execution */
  ioEnabled = SYSTEM_CTRL->WKP_IO_IE;
  ioLevel = SYSTEM_CTRL->WKP_IO_IS;
  ioValue = (~((GPIO->DATA>>9) ^ ioLevel)) & ioEnabled;
  if (ioValue){
    return;
  }
  
  //Enable deep sleep
  SystemSleepCmd(ENABLE);
  //The __disable_irq() used at the beginning of the BlueNRG_Sleep() function
  //masks all the interrupts. The interrupts will be enabled at the end of the 
  //context restore. Now induce a context save.
  void CS_contextSave(void);
  CS_contextSave();
    
  //Disable deep sleep, because if no reset occours for an interrrupt pending,
  //the register value remain set and if a simple CPU_HALT command is called from the
  //application the BlueNRG-1 enters in deep sleep without make a context save.
  //So, exiting from the deep sleep the context is restored with wrong random value.
  SystemSleepCmd(DISABLE);
  
  if (!wakeupFromSleepFlag) { 
    if((NVIC->ISPR[0]&(1<<BLUE_CTRL_IRQn)) == 0) { //At this stage the Blue Control Interrupt shall not be pending.
                                                   //So, if this happens means that the application has called the
                                                   //BlueNRG_Sleep() API with the wakeup source already acrive.
                                                   //In this scenario we don't need to wait the 91 us, otherwise
                                                   //the radio activity will be compromised.
      nvicPendingMask = savedNVIC_ISPR ^ NVIC->ISPR[0];
      if ((savedSHCSR != SCB->SHCSR)  ||                                                                //Verified if a SVCall Interrupt is pending
          ((savedNVIC_ISPR != NVIC->ISPR[0]) && (nvicPendingMask & NVIC->ISER[0]))  ||                  //Verified if a NVIC Interrupt is pending
          ((savedICSR & 0x10000000) != (SCB->ICSR & 0x10000000)) ||                                   // Verified if a PendSV interrupt is pending
          (((savedICSR & 0x4000000) != (SCB->ICSR & 0x4000000)) && (SysTick->CTRL & 0x02))) {       // Verified if a SysTick interrupt is pending
        savedCurrentTime = (*(volatile uint32_t *)BLUE_CURRENT_TIME_REG) >> 4;
        if (0xFFFFF >= (savedCurrentTime+3)) { //Check if the counter are wrapping
          while ((savedCurrentTime+3) > ((*(volatile uint32_t *)BLUE_CURRENT_TIME_REG) >> 4)); //Not Wrap
        } else {
          while (((*(volatile uint32_t *)BLUE_CURRENT_TIME_REG) >> 4) != (savedCurrentTime + 3 - 0xFFFFF)); //Wrap
        }
      }
    }

     
    if (((partInfo.die_major<<4)|(partInfo.die_cut)) >= WA_DEVICE_VERSION) {
      /* Restore BOR configuration */
      SET_BORconfigStatus(TRUE);
      /* Unlock the flash */
      flash_sw_lock = FLASH_UNLOCK_WORD;
    }
    
    // Disable the STANDBY mode 
    if (sleepMode == SLEEPMODE_NOTIMER) {
      BLUE_CTRL->TIMEOUT &= ~(LOW_POWER_STANDBY<<28);
    }
  } else {

    /* Start a new calibration, needed to signal if the HS is ready */
    CKGEN_BLE->CLK32K_IT = 1;
    CKGEN_BLE->CLK32K_COUNT = 0;
    CKGEN_BLE->CLK32K_PERIOD = 0;

    /* Restore the CSTACK number of words that will be saved before the sleep */
    i = 0;
    ptr = __vector_table[0].__ptr ;
    ptr -= CSTACK_PREAMBLE_NUMBER;
    do {
      *ptr = cStackPreamble[i];
      i++;
      ptr++;
    } while (i < CSTACK_PREAMBLE_NUMBER); 
    

    /* Restore the peripherals configuration */
    /* FLASH CONFIG */
    FLASH->CONFIG = FLASH_CONFIG_saved;
    /* NVIC */
    NVIC->ISER[0] = NVIC_ISER_saved;

    // Issue with Atollic compiler
//    memcpy((void *)NVIC->IP, (void*)NVIC_IPR_saved, sizeof(NVIC_IPR_saved));
    for (i=0; i<8; i++) {
    	NVIC->IP[i] = NVIC_IPR_saved[i];
    }

    *(volatile uint32_t *)SHPR3_REG = PENDSV_SYSTICK_IPR_saved;
    /* CKGEN SOC Enabled */
    CKGEN_SOC->CLOCK_EN = CLOCK_EN_saved;
    /* GPIO */
    GPIO->DATA = GPIO_DATA_saved;
    GPIO->OEN = GPIO_OEN_saved;
    GPIO->PE = GPIO_PE_saved;
    GPIO->DS = GPIO_DS_saved;
    GPIO->IEV = GPIO_IEV_saved;
    GPIO->IBE = GPIO_IBE_saved;
    GPIO->IS = GPIO_IS_saved;
    GPIO->IC = GPIO_IE_saved; 
    GPIO->IE = GPIO_IE_saved;
    GPIO->MODE0 = GPIO_MODE0_saved;
    GPIO->MODE1 = GPIO_MODE1_saved;
#ifdef BLUENRG2_DEVICE
    GPIO->MODE2 = GPIO_MODE2_saved;
    GPIO->MODE3 = GPIO_MODE3_saved;
#endif
    GPIO->MFTX = GPIO_IOSEL_MFTX_saved;
#if SLEEP_SAVE_N_RESTORE_UART
    /* UART */
    UART->TIMEOUT = UART_TIMEOUT_saved;
    UART->LCRH_RX = UART_LCRH_RX_saved;
    UART->IBRD = UART_IBRD_saved;
    UART->FBRD = UART_FBRD_saved;
    UART->LCRH_TX = UART_LCRH_TX_saved;
    UART->CR = UART_CR_saved;
    UART->IFLS = UART_IFLS_saved;
    UART->IMSC = UART_IMSC_saved;
    UART->DMACR = UART_DMACR_saved;
    UART->XFCR = UART_XFCR_saved;
    UART->XON1 = UART_XON1_saved;
    UART->XON2 = UART_XON2_saved;
    UART->XOFF1 = UART_XOFF1_saved;
    UART->XOFF2 = UART_XOFF2_saved;
#endif
#if SLEEP_SAVE_N_RESTORE_SPI
    /* SPI */
    SPI->CR0 = SPI_CR0_saved; 
    SPI->CR1 = SPI_CR1_saved;
    SPI->CPSR = SPI_CPSR_saved;
    SPI->IMSC = SPI_IMSC_saved;
    SPI->DMACR = SPI_DMACR_saved;
    SPI->RXFRM = SPI_RXFRM_saved;
    SPI->CHN = SPI_CHN_saved;
    SPI->WDTXF = SPI_WDTXF_saved;
#endif
#if SLEEP_SAVE_N_RESTORE_I2C
    /* I2C */
    for (i=0; i<2; i++) {
      I2C_Type *I2Cx = (I2C_Type*)(I2C2_BASE+ 0x100000*i);
      I2Cx->CR = I2C_CR_saved[i];
      I2Cx->SCR = I2C_SCR_saved[i];
      I2Cx->TFTR = I2C_TFTR_saved[i];
      I2Cx->RFTR = I2C_RFTR_saved[i];
      I2Cx->DMAR = I2C_DMAR_saved[i];
      I2Cx->BRCR = I2C_BRCR_saved[i];
      I2Cx->IMSCR = I2C_IMSCR_saved[i];
      I2Cx->THDDAT = I2C_THDDAT_saved[i];
      I2Cx->THDSTA_FST_STD = I2C_THDSTA_FST_STD_saved[i];
      I2Cx->TSUSTA_FST_STD = I2C_TSUSTA_FST_STD_saved[i];
    }
#endif
    /* RNG */
    RNG->CR = RNG_CR_saved;  
    /* SysTick */
    SysTick->LOAD = SYST_RVR_saved;
    SysTick->VAL = 0;
    SysTick->CTRL = SYST_CSR_saved;
#if SLEEP_SAVE_N_RESTORE_RTC
    /* RTC */
    RTC->CWDMR = RTC_CWDMR_saved;
    RTC->CWDLR = RTC_CWDLR_saved;
    RTC->CWYMR = RTC_CWYMR_saved;
    RTC->CWYLR = RTC_CWYLR_saved;
    RTC->CTCR = RTC_CTCR_saved;
    RTC->IMSC = RTC_IMSC_saved;
    RTC->TLR1 = RTC_TLR1_saved;
    RTC->TLR2 = RTC_TLR2_saved;
    RTC->TPR1 = RTC_TPR1_saved;
    RTC->TPR2 = RTC_TPR2_saved;
    RTC->TPR3 = RTC_TPR3_saved;
    RTC->TPR4 = RTC_TPR4_saved; 
    RTC->TCR = RTC_TCR_saved; /* Enable moved at the end of RTC configuration */
#endif
    /* MFTX */
#if SLEEP_SAVE_N_RESTORE_MFTX1
    MFT1->TNCRA = T1CRA_saved;
    MFT1->TNCRB = T1CRB_saved;
    MFT1->TNPRSC = T1PRSC_saved;
    MFT1->TNCKC = T1CKC_saved;
    MFT1->TNMCTRL = T1MCTRL_saved & ~((uint32_t)(1<<6));
    MFT1->TNICTRL = T1ICTRL_saved;
#endif
#if SLEEP_SAVE_N_RESTORE_MFTX2
    MFT2->TNCRA = T2CRA_saved;
    MFT2->TNCRB = T2CRB_saved;
    MFT2->TNPRSC = T2PRSC_saved;
    MFT2->TNCKC = T2CKC_saved;
    MFT2->TNMCTRL = T2MCTRL_saved & ~((uint32_t)(1<<6));
    MFT2->TNICTRL = T2ICTRL_saved;
#endif
#if SLEEP_SAVE_N_RESTORE_WDG
    /* WDT */
    WDG->LR = WDG_LR_saved;
    WDG->CR = WDG_CR_saved;
    WDG->LOCK = WDG_LOCK_saved;
#endif
#if SLEEP_SAVE_N_RESTORE_DMA
    /* DMA */
    for (i=0; i<8; i++) {
      DMA_CH_Type *DMAx = (DMA_CH_Type*)(DMA_CH0_BASE+ 0x14*i);
      DMAx->CNDTR = DMA_CNDTR_saved[i];
      DMAx->CCR = DMA_CCR_saved[i] ;
      DMAx->CPAR = DMA_CPAR_saved[i];
      DMAx->CMAR = DMA_CMAR[i];
    }
#endif
#if SLEEP_SAVE_N_RESTORE_ADC
    /* ADC */
    ADC->CONF = ADC_CONF_saved;
    ADC->IRQMASK = ADC_IRQMASK_saved;
    ADC->OFFSET_MSB = ADC_OFFSET_MSB_saved;
    ADC->OFFSET_LSB = ADC_OFFSET_LSB_saved;
    ADC->THRESHOLD_HI = ADC_THRESHOLD_HI_saved;
    ADC->THRESHOLD_LO = ADC_THRESHOLD_LO_saved;
    ADC->CTRL = ADC_CTRL_saved;
#endif
    
    /* PKA */
    PKA->IEN = PKA_IEN_saved;
    //The five IRQs are linked to a real ISR. If any of the five IRQs
    //triggered, then pend their ISR
    //Capture the wake source from the BLE_REASON_RESET register
    if ((CKGEN_SOC->REASON_RST == 0) &&
        (CKGEN_BLE->REASON_RST >= WAKENED_FROM_IO9) && 
          (CKGEN_BLE->REASON_RST <= WAKENED_FROM_IO13) && 
            gpioWakeBitMask) {
              if ((((CKGEN_BLE->REASON_RST & WAKENED_FROM_IO9) == WAKENED_FROM_IO9) && (GPIO->IE & GPIO_Pin_9))   ||
                  (((CKGEN_BLE->REASON_RST & WAKENED_FROM_IO10) == WAKENED_FROM_IO10) && (GPIO->IE & GPIO_Pin_10)) ||
                    (((CKGEN_BLE->REASON_RST & WAKENED_FROM_IO11) == WAKENED_FROM_IO11) && (GPIO->IE & GPIO_Pin_11)) ||
                      (((CKGEN_BLE->REASON_RST & WAKENED_FROM_IO12) == WAKENED_FROM_IO12) && (GPIO->IE & GPIO_Pin_12)) ||
                        (((CKGEN_BLE->REASON_RST & WAKENED_FROM_IO13) == WAKENED_FROM_IO13) && (GPIO->IE & GPIO_Pin_13))) {
                          NVIC->ISPR[0] = 1<<GPIO_IRQn;
                        }
            }

    // Disable the STANDBY mode 
    if (sleepMode == SLEEPMODE_NOTIMER) {
      BLUE_CTRL->TIMEOUT &= ~(LOW_POWER_STANDBY<<28);
    }
    
    /* Restore the System Control register to indicate which HS crystal is used */
    SYSTEM_CTRL->CTRL = SYS_Ctrl_saved;

    // Wait until the HS clock is ready.
    // If SLEEPMODE_NOTIMER is set, wait the LS clock is ready.  
    if (sleepMode == SLEEPMODE_NOTIMER) {
      DeviceConfiguration(FALSE, TRUE);
    } else {
      DeviceConfiguration(FALSE, FALSE);
    }

    /* If the HS is a 32 MHz */
    if (SYS_Ctrl_saved & 1) {
#ifndef FORCE_CORE_TO_16MHZ
      /* AHB up converter command register write*/
      frequency_switch();
#endif
    }
  }
}

uint8_t BlueNRG_Sleep(SleepModes sleepMode, 
                      uint8_t gpioWakeBitMask, 
                      uint8_t gpioWakeLevelMask)
{
  SleepModes app_sleepMode, ble_sleepMode, sleepMode_allowed;
  
  /* Mask all the interrupt */
  ATOMIC_SECTION_BEGIN();

  /* Flag to signal if a wakeup from standby or sleep occurred */
  wakeupFromSleepFlag = 0; 

  ble_sleepMode = (SleepModes)BlueNRG_Stack_Perform_Deep_Sleep_Check();
  app_sleepMode = App_SleepMode_Check(sleepMode);
  sleepMode_allowed = (SleepModes)MIN(app_sleepMode, sleepMode);
  sleepMode_allowed = (SleepModes)MIN(ble_sleepMode, sleepMode_allowed);

#ifdef DEBUG_SLEEP_MODE
  sleepMode_selected[sleepMode_allowed]++;
#endif

  if (sleepMode_allowed == SLEEPMODE_RUNNING) {
    ATOMIC_SECTION_END();
    return SUCCESS;
  }
  
  if (sleepMode_allowed == SLEEPMODE_CPU_HALT) {
    /* Store the watchdog configuration and the disable it to avoid reset during CPU halt. */
    uint32_t WDG_CR_saved = WDG->CR;
    WDG->CR = 0;
    
    /* Wait for interrupt is called: the core execution is halted until an event occurs. */
    __WFI();
    
    /* Restore the watchdog functionality. */
    WDG->CR= WDG_CR_saved;
        
    ATOMIC_SECTION_END();
    return SUCCESS;
  }

  /* Setup the Wakeup Source */
  SYSTEM_CTRL->WKP_IO_IS = gpioWakeLevelMask;
  SYSTEM_CTRL->WKP_IO_IE = gpioWakeBitMask;
    
  BlueNRG_InternalSleep(sleepMode_allowed, gpioWakeBitMask);
  
  ATOMIC_SECTION_END();
  
  return SUCCESS;
}

uint8_t BlueNRG_WakeupSource(void)
{
  if ((CKGEN_SOC->REASON_RST == 0) &&
      (CKGEN_BLE->REASON_RST >= WAKENED_FROM_IO9) && 
      (CKGEN_BLE->REASON_RST <= WAKENED_FROM_IO13)) {
    if ((CKGEN_BLE->REASON_RST & WAKENED_FROM_IO9) == WAKENED_FROM_IO9) {
      return WAKEUP_IO9;
    }
    if ((CKGEN_BLE->REASON_RST & WAKENED_FROM_IO10) == WAKENED_FROM_IO10) {
      return WAKEUP_IO10;
    }
    if ((CKGEN_BLE->REASON_RST & WAKENED_FROM_IO11) == WAKENED_FROM_IO11) {
      return WAKEUP_IO11;
    }
    if ((CKGEN_BLE->REASON_RST & WAKENED_FROM_IO12) == WAKENED_FROM_IO12) {
      return WAKEUP_IO12;
    }
    if ((CKGEN_BLE->REASON_RST & WAKENED_FROM_IO13) == WAKENED_FROM_IO13) {
      return WAKEUP_IO13;
    }
  }
  if ((CKGEN_SOC->REASON_RST == 0) &&
      ((CKGEN_BLE->REASON_RST & WAKENED_FROM_BLUE_TIMER1) == WAKENED_FROM_BLUE_TIMER1)) {
    return WAKEUP_SLEEP_TIMER1;
  }
  if ((CKGEN_SOC->REASON_RST == 0) &&
      ((CKGEN_BLE->REASON_RST & WAKENED_FROM_BLUE_TIMER2) == WAKENED_FROM_BLUE_TIMER2)) {
    return WAKEUP_SLEEP_TIMER2;
  }
  if ((CKGEN_SOC->REASON_RST == 0) &&
      ((CKGEN_BLE->REASON_RST & WAKENED_FROM_POR) == WAKENED_FROM_POR)) {
    return WAKEUP_POR;
  }
  if ((CKGEN_SOC->REASON_RST == 0) &&
      ((CKGEN_BLE->REASON_RST & WAKENED_FROM_BOR) == WAKENED_FROM_BOR)) {
    return WAKEUP_BOR;
  }
  if (CKGEN_SOC->REASON_RST == 2) {
    return WAKEUP_SYS_RESET_REQ;
  }
  if (CKGEN_SOC->REASON_RST == 4) {
    return WAKEUP_RESET_WDG;
  }

  return NO_WAKEUP_RESET;
}
