vrbadev/Gloves-Equipped-with-Motion-Sensors-Bachelor-Project-HW-FW-SW/Firmware/uVision/lib_sensors/src/lis2mdl_reg.c

/*
 ******************************************************************************
 * @file    LIS2MDLSensor_reg.c
 * @author  Sensors Software Solution Team
 * @brief   LIS2MDL driver file
 ******************************************************************************
 * @attention
 *
 * <h2><center>&copy; COPYRIGHT(c) 2018 STMicroelectronics</center></h2>
 *
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
*/
#include "../inc/lis2mdl_reg.h"

extern int i2c_write(uint8_t reg, uint8_t* data, uint8_t len);
extern int i2c_read(uint8_t reg, uint8_t* data, uint8_t len);

/**
  * @defgroup    LIS2MDL
  * @brief       This file provides a set of functions needed to drive the
  *              lis2mdl enhanced inertial module.
  * @{
  *
  */

/**
  * @defgroup    LIS2MDLSensor_Interfaces_Functions
  * @brief       This section provide a set of functions used to read and
  *              write a generic register of the device.
  *              MANDATORY: return 0 -> no Error.
  * @{
  *
  */

/**
  * @brief  Read generic device register
  *
  * @param  ctx   read / write interface definitions(ptr)
  * @param  reg   register to read
  * @param  data  pointer to buffer that store the data read(ptr)
  * @param  len   number of consecutive register to read
  * @retval       interface status (MANDATORY: return 0 -> no Error)
  *
  */
int32_t LIS2MDLSensor_read_reg(uint8_t reg, uint8_t* data,
                         uint16_t len)
{
  return i2c_read(reg, data, len);
}

/**
  * @brief  Write generic device register
  *
  * @param  ctx   read / write interface definitions(ptr)
  * @param  reg   register to write
  * @param  data  pointer to data to write in register reg(ptr)
  * @param  len   number of consecutive register to write
  * @retval       interface status (MANDATORY: return 0 -> no Error)
  *
  */
int32_t LIS2MDLSensor_write_reg(uint8_t reg, uint8_t* data,
                          uint16_t len)
{
  return i2c_write(reg, data, len);
}

/**
  * @}
  *
  */

  /**
  * @defgroup    LIS2MDLSensor_Sensitivity
  * @brief       These functions convert raw-data into engineering units.
  * @{
  *
  */
float_t LIS2MDLSensor_from_lsb_to_mgauss(int16_t lsb)
{
  return ((float_t)lsb * 1.5f);
}

float_t LIS2MDLSensor_from_lsb_to_celsius(int16_t lsb)
{
  return (((float_t)lsb / 8.0f) + 25.0f);
}

/**
  * @}
  *
  */

/**
  * @defgroup    LIS2MDLSensor_data_generation
  * @brief       This section group all the functions concerning
  *              data generation
  * @{
  *
  */

/**
  * @brief  These registers comprise a 3 group of 16-bit number and represent
  *         hard-iron offset in order to compensate environmental effects.
  *         Data format is the same of output data raw: two’s complement
  *         with 1LSb = 1.5mG. These values act on the magnetic output data
  *         value in order to delete the environmental offset.[set]
  *
  * @param  ctx   read / write interface definitions.(ptr)
  * @param  buff  buffer that contains data to write
  * @retval       interface status.(MANDATORY: return 0 -> no Error)
  *
  */
int32_t LIS2MDLSensor_mag_user_offset_set(uint8_t *buff)
{
  int32_t ret;
  ret = LIS2MDLSensor_write_reg(LIS2MDLSensor_OFFSET_X_REG_L, buff, 6);
  return ret;
}

/**
  * @brief  These registers comprise a 3 group of 16-bit number and represent
  *         hard-iron offset in order to compensate environmental effects.
  *         Data format is the same of output data raw: two’s complement
  *         with 1LSb = 1.5mG. These values act on the magnetic output data
  *         value in order to delete the environmental offset.[get]
  *
  * @param  ctx   read / write interface definitions.(ptr)
  * @param  buff  that stores data read
  * @retval       interface status.(MANDATORY: return 0 -> no Error)
  *
  */
int32_t LIS2MDLSensor_mag_user_offset_get(uint8_t *buff)
{
  int32_t ret;
  ret = LIS2MDLSensor_read_reg(LIS2MDLSensor_OFFSET_X_REG_L, buff, 6);
  return ret;
}

/**
  * @brief  Operating mode selection.[set]
  *
  * @param  ctx    read / write interface definitions.(ptr)
  * @param  val    change the values of md in reg CFG_REG_A
  * @retval        interface status.(MANDATORY: return 0 -> no Error)
  *
  */
int32_t LIS2MDLSensor_operating_mode_set(LIS2MDLSensor_md_t val)
{
  LIS2MDLSensor_cfg_reg_a_t reg;
  int32_t ret;

  ret = LIS2MDLSensor_read_reg(LIS2MDLSensor_CFG_REG_A, (uint8_t*)&reg, 1);
  
  if(ret == 0){
    reg.md = (uint8_t)val;
    ret = LIS2MDLSensor_write_reg(LIS2MDLSensor_CFG_REG_A, (uint8_t*)&reg, 1);
  }
  
  return ret;
}

/**
  * @brief  Operating mode selection.[get]
  *
  * @param  ctx   read / write interface definitions.(ptr)
  * @param  val   Get the values of md in reg CFG_REG_A.(ptr)
  * @retval       interface status.(MANDATORY: return 0 -> no Error)
  *
  */
int32_t LIS2MDLSensor_operating_mode_get(LIS2MDLSensor_md_t *val)
{
  LIS2MDLSensor_cfg_reg_a_t reg;
  int32_t ret;

  ret = LIS2MDLSensor_read_reg(LIS2MDLSensor_CFG_REG_A, (uint8_t*)&reg, 1);
  switch (reg.md){
    case LIS2MDLSensor_POWER_DOWN:
      *val = LIS2MDLSensor_POWER_DOWN;
      break;
    case LIS2MDLSensor_CONTINUOUS_MODE:
      *val = LIS2MDLSensor_CONTINUOUS_MODE;
      break;
    case LIS2MDLSensor_SINGLE_TRIGGER:
      *val = LIS2MDLSensor_SINGLE_TRIGGER;
      break;
    default:
      *val = LIS2MDLSensor_POWER_DOWN;
      break;
  }  

  return ret;
}

/**
  * @brief  Output data rate selection.[set] 
  *
  * @param  ctx   read / write interface definitions.(ptr)
  * @param  val   change the values of odr in reg CFG_REG_A
  * @retval       interface status.(MANDATORY: return 0 -> no Error)
  *
  */
int32_t LIS2MDLSensor_data_rate_set(LIS2MDLSensor_odr_t val)
{
  LIS2MDLSensor_cfg_reg_a_t reg;
  int32_t ret;

  ret = LIS2MDLSensor_read_reg(LIS2MDLSensor_CFG_REG_A, (uint8_t*)&reg, 1);
  
  if(ret == 0){
    reg.odr = (uint8_t)val;
    ret = LIS2MDLSensor_write_reg(LIS2MDLSensor_CFG_REG_A, (uint8_t*)&reg, 1);
  }
  
  return ret;
}

/**
  * @brief  Output data rate selection.[get] 
  *
  * @param  ctx   read / write interface definitions.(ptr)
  * @param  val   Get the values of odr in reg CFG_REG_A.(ptr)
  * @retval       interface status.(MANDATORY: return 0 -> no Error)
  *
  */
int32_t LIS2MDLSensor_data_rate_get(LIS2MDLSensor_odr_t *val)
{
  LIS2MDLSensor_cfg_reg_a_t reg;
  int32_t ret;

  ret = LIS2MDLSensor_read_reg(LIS2MDLSensor_CFG_REG_A, (uint8_t*)&reg, 1);
  switch (reg.odr){
    case LIS2MDLSensor_ODR_10Hz:
      *val = LIS2MDLSensor_ODR_10Hz;
      break;
    case LIS2MDLSensor_ODR_20Hz:
      *val = LIS2MDLSensor_ODR_20Hz;
      break;
    case LIS2MDLSensor_ODR_50Hz:
      *val = LIS2MDLSensor_ODR_50Hz;
      break;
    case LIS2MDLSensor_ODR_100Hz:
      *val = LIS2MDLSensor_ODR_100Hz;
      break;
    default:
      *val = LIS2MDLSensor_ODR_10Hz;
      break;
  }
  return ret;
}

/**
  * @brief  Enables high-resolution/low-power mode.[set]
  *
  * @param  ctx   read / write interface definitions.(ptr)
  * @param  val   change the values of lp in reg CFG_REG_A
  * @retval       interface status.(MANDATORY: return 0 -> no Error)
  *
  */
int32_t LIS2MDLSensor_power_mode_set(LIS2MDLSensor_lp_t val)
{
  LIS2MDLSensor_cfg_reg_a_t reg;
  int32_t ret;

  ret = LIS2MDLSensor_read_reg(LIS2MDLSensor_CFG_REG_A, (uint8_t*)&reg, 1);
  
  if(ret == 0){
    reg.lp = (uint8_t)val;
    ret = LIS2MDLSensor_write_reg(LIS2MDLSensor_CFG_REG_A, (uint8_t*)&reg, 1);
  }
  
  return ret;
}

/**
  * @brief  Enables high-resolution/low-power mode.[get]
  *
  * @param  ctx   read / write interface definitions.(ptr)
  * @param  val   Get the values of lp in reg CFG_REG_A.(ptr)
  * @retval       interface status.(MANDATORY: return 0 -> no Error)
  *
  */
int32_t LIS2MDLSensor_power_mode_get(LIS2MDLSensor_lp_t *val)
{
  LIS2MDLSensor_cfg_reg_a_t reg;
  int32_t ret;

  ret = LIS2MDLSensor_read_reg(LIS2MDLSensor_CFG_REG_A, (uint8_t*)&reg, 1);
  switch (reg.lp){
    case LIS2MDLSensor_HIGH_RESOLUTION:
      *val = LIS2MDLSensor_HIGH_RESOLUTION;
      break;
    case LIS2MDLSensor_LOW_POWER:
      *val = LIS2MDLSensor_LOW_POWER;
      break;
    default:
      *val = LIS2MDLSensor_HIGH_RESOLUTION;
      break;
  }
  return ret;
}

/**
  * @brief  Enables the magnetometer temperature compensation.[set] 
  *
  * @param  ctx   read / write interface definitions.(ptr)
  * @param  val   change the values of comp_temp_en in reg CFG_REG_A
  * @retval       interface status.(MANDATORY: return 0 -> no Error)
  *
  */
int32_t LIS2MDLSensor_offset_temp_comp_set(uint8_t val)
{
  LIS2MDLSensor_cfg_reg_a_t reg;
  int32_t ret;

  ret = LIS2MDLSensor_read_reg(LIS2MDLSensor_CFG_REG_A, (uint8_t*)&reg, 1);
  
  if(ret == 0){
    reg.comp_temp_en = val;
    ret = LIS2MDLSensor_write_reg(LIS2MDLSensor_CFG_REG_A, (uint8_t*)&reg, 1);
  }
  
  return ret;
}

/**
  * @brief  Enables the magnetometer temperature compensation.[get]
  *
  * @param  ctx   read / write interface definitions.(ptr)
  * @param  val   change the values of comp_temp_en in reg CFG_REG_A.(ptr)
  * @retval       interface status.(MANDATORY: return 0 -> no Error)
  *
  */
int32_t LIS2MDLSensor_offset_temp_comp_get(uint8_t *val)
{
  LIS2MDLSensor_cfg_reg_a_t reg;
  int32_t ret;

  ret = LIS2MDLSensor_read_reg(LIS2MDLSensor_CFG_REG_A, (uint8_t*)&reg, 1);
  *val = reg.comp_temp_en;

  return ret;
}

/**
  * @brief  Low-pass bandwidth selection.[set]
  *
  * @param  ctx   read / write interface definitions.(ptr)
  * @param  val   change the values of lpf in reg CFG_REG_B
  * @retval       interface status.(MANDATORY: return 0 -> no Error)
  *
  */
int32_t LIS2MDLSensor_low_pass_bandwidth_set(LIS2MDLSensor_lpf_t val)
{
  LIS2MDLSensor_cfg_reg_b_t reg;
  int32_t ret;

  ret = LIS2MDLSensor_read_reg(LIS2MDLSensor_CFG_REG_B, (uint8_t*)&reg, 1);
  
  if(ret == 0){
    reg.lpf = (uint8_t)val;
    ret = LIS2MDLSensor_write_reg(LIS2MDLSensor_CFG_REG_B, (uint8_t*)&reg, 1);
  }
  
  return ret;
}

/**
  * @brief  Low-pass bandwidth selection.[get]
  *
  * @param  ctx   read / write interface definitions.(ptr)
  * @param  val   Get the values of lpf in reg CFG_REG_B.(ptr)
  * @retval       interface status.(MANDATORY: return 0 -> no Error)
  *
  */
int32_t LIS2MDLSensor_low_pass_bandwidth_get(LIS2MDLSensor_lpf_t *val)
{
  LIS2MDLSensor_cfg_reg_b_t reg;
  int32_t ret;

  ret = LIS2MDLSensor_read_reg(LIS2MDLSensor_CFG_REG_B, (uint8_t*)&reg, 1);
  switch (reg.lpf){
    case LIS2MDLSensor_ODR_DIV_2:
      *val = LIS2MDLSensor_ODR_DIV_2;
      break;
    case LIS2MDLSensor_ODR_DIV_4:
      *val = LIS2MDLSensor_ODR_DIV_4;
      break;
    default:
      *val = LIS2MDLSensor_ODR_DIV_2;
      break;
  }
  return ret;
}

/**
  * @brief  Reset mode.[set]
  *
  * @param  ctx   read / write interface definitions.(ptr)
  * @param  val   change the values of set_rst in reg CFG_REG_B
  * @retval       interface status.(MANDATORY: return 0 -> no Error)
  *
  */
int32_t LIS2MDLSensor_set_rst_mode_set(LIS2MDLSensor_set_rst_t val)
{
  LIS2MDLSensor_cfg_reg_b_t reg;
  int32_t ret;

  ret = LIS2MDLSensor_read_reg(LIS2MDLSensor_CFG_REG_B, (uint8_t*)&reg, 1);
  
  if(ret == 0){
    reg.set_rst = (uint8_t)val;
    ret = LIS2MDLSensor_write_reg(LIS2MDLSensor_CFG_REG_B, (uint8_t*)&reg, 1);
  }
  
  return ret;
}

/**
  * @brief  Reset mode.[get]
  *
  * @param  ctx   read / write interface definitions.(ptr)
  * @param  val   Get the values of set_rst in reg CFG_REG_B.(ptr)
  * @retval       interface status.(MANDATORY: return 0 -> no Error)
  *
  */
int32_t LIS2MDLSensor_set_rst_mode_get(LIS2MDLSensor_set_rst_t *val)
{
  LIS2MDLSensor_cfg_reg_b_t reg;
  int32_t ret;

  ret = LIS2MDLSensor_read_reg(LIS2MDLSensor_CFG_REG_B, (uint8_t*)&reg, 1);
  switch (reg.set_rst){
    case LIS2MDLSensor_SET_SENS_ODR_DIV_63:
      *val = LIS2MDLSensor_SET_SENS_ODR_DIV_63;
      break;
    case LIS2MDLSensor_SENS_OFF_CANC_EVERY_ODR:
      *val = LIS2MDLSensor_SENS_OFF_CANC_EVERY_ODR;
      break;
    case LIS2MDLSensor_SET_SENS_ONLY_AT_POWER_ON:
      *val = LIS2MDLSensor_SET_SENS_ONLY_AT_POWER_ON;
      break;
    default:
      *val = LIS2MDLSensor_SET_SENS_ODR_DIV_63;
      break;
  }
  return ret;
}

/**
  * @brief  Enables offset cancellation in single measurement mode. 
  *         The OFF_CANC bit must be set to 1 when enabling offset
  *         cancellation in single measurement mode this means a
  *         call function: set_rst_mode(SENS_OFF_CANC_EVERY_ODR)
  *         is need.[set]
  *
  * @param  ctx   read / write interface definitions.(ptr)
  * @param  val   change the values of off_canc_one_shot in reg CFG_REG_B
  * @retval       interface status.(MANDATORY: return 0 -> no Error)
  *
  */
int32_t LIS2MDLSensor_set_rst_sensor_single_set(uint8_t val)
{
  LIS2MDLSensor_cfg_reg_b_t reg;
  int32_t ret;

  ret = LIS2MDLSensor_read_reg(LIS2MDLSensor_CFG_REG_B, (uint8_t*)&reg, 1);
  
  if(ret == 0){
    reg.off_canc_one_shot = val;
    ret = LIS2MDLSensor_write_reg(LIS2MDLSensor_CFG_REG_B, (uint8_t*)&reg, 1);
  }
  
  return ret;
}

/**
  * @brief  Enables offset cancellation in single measurement mode. 
  *         The OFF_CANC bit must be set to 1 when enabling offset
  *         cancellation in single measurement mode this means a
  *         call function: set_rst_mode(SENS_OFF_CANC_EVERY_ODR)
  *         is need.[get]
  *
  * @param  ctx   read / write interface definitions.(ptr)
  * @param  val   change the values of off_canc_one_shot in reg CFG_REG_B.(ptr)
  * @retval       interface status.(MANDATORY: return 0 -> no Error)
  *
  */
int32_t LIS2MDLSensor_set_rst_sensor_single_get(uint8_t *val)
{
  LIS2MDLSensor_cfg_reg_b_t reg;
  int32_t ret;

  ret = LIS2MDLSensor_read_reg(LIS2MDLSensor_CFG_REG_B, (uint8_t*)&reg, 1);
  *val = reg.off_canc_one_shot;

  return ret;
}

/**
  * @brief  Blockdataupdate.[set]
  *
  * @param  ctx   read / write interface definitions.(ptr)
  * @param  val   change the values of bdu in reg CFG_REG_C
  * @retval       interface status.(MANDATORY: return 0 -> no Error)
  *
  */
int32_t LIS2MDLSensor_block_data_update_set(uint8_t val)
{
  LIS2MDLSensor_cfg_reg_c_t reg;
  int32_t ret;

  ret = LIS2MDLSensor_read_reg(LIS2MDLSensor_CFG_REG_C, (uint8_t*)&reg, 1);
  
  if(ret == 0){
    reg.bdu = val;
    ret = LIS2MDLSensor_write_reg(LIS2MDLSensor_CFG_REG_C, (uint8_t*)&reg, 1);
  }
  
  return ret;
}

/**
  * @brief  Blockdataupdate.[get]
  *
  * @param  ctx   read / write interface definitions.(ptr)
  * @param  val   change the values of bdu in reg CFG_REG_C.(ptr)
  * @retval       interface status.(MANDATORY: return 0 -> no Error)
  *
  */
int32_t LIS2MDLSensor_block_data_update_get(uint8_t *val)
{
  LIS2MDLSensor_cfg_reg_c_t reg;
  int32_t ret;

  ret = LIS2MDLSensor_read_reg(LIS2MDLSensor_CFG_REG_C, (uint8_t*)&reg, 1);
  *val = reg.bdu;

  return ret;
}

/**
  * @brief  Magnetic set of data available.[get]
  *
  * @param  ctx   read / write interface definitions.(ptr)
  * @param  val   change the values of zyxda in reg STATUS_REG.(ptr)
  * @retval       interface status.(MANDATORY: return 0 -> no Error)
  *
  */
int32_t LIS2MDLSensor_mag_data_ready_get(uint8_t *val)
{
  LIS2MDLSensor_status_reg_t reg;
  int32_t ret;

  ret = LIS2MDLSensor_read_reg(LIS2MDLSensor_STATUS_REG, (uint8_t*)&reg, 1);
  *val = reg.zyxda;

  return ret;
}

/**
  * @brief  Magnetic set of data overrun.[get]
  *
  * @param  ctx   read / write interface definitions.(ptr)
  * @param  val   change the values of zyxor in reg STATUS_REG.(ptr)
  * @retval       interface status.(MANDATORY: return 0 -> no Error)
  *
  */
int32_t LIS2MDLSensor_mag_data_ovr_get(uint8_t *val)
{
  LIS2MDLSensor_status_reg_t reg;
  int32_t ret;

  ret = LIS2MDLSensor_read_reg(LIS2MDLSensor_STATUS_REG, (uint8_t*)&reg, 1);
  *val = reg.zyxor;

  return ret;
}

/**
  * @brief  Magnetic output value.[get]
  *
  * @param  ctx   read / write interface definitions.(ptr)
  * @param  buff  that stores data read
  * @retval       interface status.(MANDATORY: return 0 -> no Error)
  *
  */
int32_t LIS2MDLSensor_magnetic_raw_get(uint8_t *buff)
{
  int32_t ret;
  ret = LIS2MDLSensor_read_reg(LIS2MDLSensor_OUTX_L_REG, buff, 6);
  return ret;
}

/**
  * @brief  Temperature output value.[get]
  *
  * @param  ctx   read / write interface definitions.(ptr)
  * @param  buff  that stores data read
  * @retval       interface status.(MANDATORY: return 0 -> no Error)
  *
  */
int32_t LIS2MDLSensor_temperature_raw_get(uint8_t *buff)
{
  int32_t ret;
  ret = LIS2MDLSensor_read_reg(LIS2MDLSensor_TEMP_OUT_L_REG, buff, 2);
  return ret;
}

/**
  * @}
  *
  */

/**
  * @defgroup    LIS2MDLSensor_common
  * @brief       This section group common usefull functions
  * @{
  *
  */

/**
  * @brief  DeviceWhoamI.[get]
  *
  * @param  ctx   read / write interface definitions.(ptr)
  * @param  buff  that stores data read
  * @retval       interface status.(MANDATORY: return 0 -> no Error)
  *
  */
int32_t LIS2MDLSensor_device_id_get(uint8_t *buff)
{
  int32_t ret;
  ret = LIS2MDLSensor_read_reg(LIS2MDLSensor_WHO_AM_I, buff, 1);
  return ret;
}

/**
  * @brief  Software reset. Restore the default values in user registers.[set]
  *
  * @param  ctx   read / write interface definitions.(ptr)
  * @param  val   change the values of soft_rst in reg CFG_REG_A
  * @retval       interface status.(MANDATORY: return 0 -> no Error)
  *
  */
int32_t LIS2MDLSensor_reset_set(uint8_t val)
{
  LIS2MDLSensor_cfg_reg_a_t reg;
  int32_t ret;

  ret = LIS2MDLSensor_read_reg(LIS2MDLSensor_CFG_REG_A, (uint8_t*)&reg, 1);
  
  if(ret == 0){
    reg.soft_rst = val;
    ret = LIS2MDLSensor_write_reg(LIS2MDLSensor_CFG_REG_A, (uint8_t*)&reg, 1);
  }
  
  return ret;
}

/**
  * @brief  Software reset. Restore the default values in user registers.[get]
  *
  * @param  ctx   read / write interface definitions.(ptr)
  * @param  val   change the values of soft_rst in reg CFG_REG_A.(ptr)
  * @retval       interface status.(MANDATORY: return 0 -> no Error)
  *
  */
int32_t LIS2MDLSensor_reset_get(uint8_t *val)
{
  LIS2MDLSensor_cfg_reg_a_t reg;
  int32_t ret;

  ret = LIS2MDLSensor_read_reg(LIS2MDLSensor_CFG_REG_A, (uint8_t*)&reg, 1);
  *val = reg.soft_rst;

  return ret;
}

/**
  * @brief  Reboot memory content. Reload the calibration parameters.[set] 
  *
  * @param  ctx   read / write interface definitions.(ptr)
  * @param  val   change the values of reboot in reg CFG_REG_A
  * @retval       interface status.(MANDATORY: return 0 -> no Error)
  *
  */
int32_t LIS2MDLSensor_boot_set(uint8_t val)
{
  LIS2MDLSensor_cfg_reg_a_t reg;
  int32_t ret;

  ret = LIS2MDLSensor_read_reg(LIS2MDLSensor_CFG_REG_A, (uint8_t*)&reg, 1);
  
  if(ret == 0){
    reg.reboot = val;
    ret = LIS2MDLSensor_write_reg(LIS2MDLSensor_CFG_REG_A, (uint8_t*)&reg, 1);
  }
  
  return ret;
}

/**
  * @brief  Reboot memory content. Reload the calibration parameters.[get]
  *
  * @param  ctx   read / write interface definitions.(ptr)
  * @param  val   change the values of reboot in reg CFG_REG_A.(ptr)
  * @retval       interface status.(MANDATORY: return 0 -> no Error)
  *
  */
int32_t LIS2MDLSensor_boot_get(uint8_t *val)
{
  LIS2MDLSensor_cfg_reg_a_t reg;
  int32_t ret;

  ret = LIS2MDLSensor_read_reg(LIS2MDLSensor_CFG_REG_A, (uint8_t*)&reg, 1);
  *val = reg.reboot;

  return ret;
}

/**
  * @brief  Selftest.[set]
  *
  * @param  ctx   read / write interface definitions.(ptr)
  * @param  val   change the values of self_test in reg CFG_REG_C
  * @retval       interface status.(MANDATORY: return 0 -> no Error)
  *
  */
int32_t LIS2MDLSensor_self_test_set(uint8_t val)
{
  LIS2MDLSensor_cfg_reg_c_t reg;
  int32_t ret;

  ret = LIS2MDLSensor_read_reg(LIS2MDLSensor_CFG_REG_C, (uint8_t*)&reg, 1);
  
  if(ret == 0){
    reg.self_test = val;
    ret = LIS2MDLSensor_write_reg(LIS2MDLSensor_CFG_REG_C, (uint8_t*)&reg, 1);
  }
  
  return ret;
}

/**
  * @brief  Selftest.[get]
  *
  * @param  ctx   read / write interface definitions.(ptr)
  * @param  val   change the values of self_test in reg CFG_REG_C.(ptr)
  * @retval       interface status.(MANDATORY: return 0 -> no Error)
  *
  */
int32_t LIS2MDLSensor_self_test_get(uint8_t *val)
{
  LIS2MDLSensor_cfg_reg_c_t reg;
  int32_t ret;

  ret = LIS2MDLSensor_read_reg(LIS2MDLSensor_CFG_REG_C, (uint8_t*)&reg, 1);
  *val = reg.self_test;

  return ret;
}

/**
  * @brief  Big/Little Endian data selection.[set]
  *
  * @param  ctx   read / write interface definitions.(ptr)
  * @param  val   change the values of ble in reg CFG_REG_C
  * @retval       interface status.(MANDATORY: return 0 -> no Error)
  *
  */
int32_t LIS2MDLSensor_data_format_set(LIS2MDLSensor_ble_t val)
{
  LIS2MDLSensor_cfg_reg_c_t reg;
  int32_t ret;

  ret = LIS2MDLSensor_read_reg(LIS2MDLSensor_CFG_REG_C, (uint8_t*)&reg, 1);
  
  if(ret == 0){
    reg.ble = (uint8_t)val;
    ret = LIS2MDLSensor_write_reg(LIS2MDLSensor_CFG_REG_C, (uint8_t*)&reg, 1);
  }
  
  return ret;
}

/**
  * @brief  Big/Little Endian data selection.[get]
  *
  * @param  ctx   read / write interface definitions.(ptr)
  * @param  val   Get the values of ble in reg CFG_REG_C.(ptr)
  * @retval       interface status.(MANDATORY: return 0 -> no Error)
  *
  */
int32_t LIS2MDLSensor_data_format_get(LIS2MDLSensor_ble_t *val)
{
  LIS2MDLSensor_cfg_reg_c_t reg;
  int32_t ret;

  ret = LIS2MDLSensor_read_reg(LIS2MDLSensor_CFG_REG_C, (uint8_t*)&reg, 1);
  switch (reg.ble){
    case LIS2MDLSensor_LSB_AT_LOW_ADD:
      *val = LIS2MDLSensor_LSB_AT_LOW_ADD;
      break;
    case LIS2MDLSensor_MSB_AT_LOW_ADD:
      *val = LIS2MDLSensor_MSB_AT_LOW_ADD;
      break;
    default:
      *val = LIS2MDLSensor_LSB_AT_LOW_ADD;
      break;
  }
  return ret;
}

/**
  * @brief  Info about device status.[get]
  *
  * @param  ctx   read / write interface definitions.(ptr)
  * @param  val   registers STATUS_REG.(ptr)
  * @retval       interface status.(MANDATORY: return 0 -> no Error)
  *
  */
int32_t LIS2MDLSensor_status_get(LIS2MDLSensor_status_reg_t *val)
{
  int32_t ret;
  ret = LIS2MDLSensor_read_reg(LIS2MDLSensor_STATUS_REG, (uint8_t*) val, 1);
  return ret;
}

/**
  * @}
  *
  */

/**
  * @defgroup    LIS2MDLSensor_interrupts
  * @brief       This section group all the functions that manage interrupts
  * @{
  *
  */

/**
  * @brief  The interrupt block recognition checks data after/before the
  *         hard-iron correction to discover the interrupt.[set]
  *
  * @param  ctx   read / write interface definitions.(ptr)
  * @param  val   change the values of int_on_dataoff in reg CFG_REG_B
  * @retval       interface status.(MANDATORY: return 0 -> no Error)
  *
  */
int32_t LIS2MDLSensor_offset_int_conf_set(LIS2MDLSensor_int_on_dataoff_t val)
{
  LIS2MDLSensor_cfg_reg_b_t reg;
  int32_t ret;

  ret = LIS2MDLSensor_read_reg(LIS2MDLSensor_CFG_REG_B, (uint8_t*)&reg, 1);
  
  if(ret == 0){
    reg.int_on_dataoff = (uint8_t)val;
    ret = LIS2MDLSensor_write_reg(LIS2MDLSensor_CFG_REG_B, (uint8_t*)&reg, 1);
  }
  
  return ret;
}

/**
  * @brief  The interrupt block recognition checks data after/before the
  *         hard-iron correction to discover the interrupt.[get]
  *
  * @param  ctx   read / write interface definitions.(ptr)
  * @param  val   Get the values of int_on_dataoff in reg CFG_REG_B.(ptr)
  * @retval       interface status.(MANDATORY: return 0 -> no Error)
  *
  */
int32_t LIS2MDLSensor_offset_int_conf_get(LIS2MDLSensor_int_on_dataoff_t *val)
{
  LIS2MDLSensor_cfg_reg_b_t reg;
  int32_t ret;

  ret = LIS2MDLSensor_read_reg(LIS2MDLSensor_CFG_REG_B, (uint8_t*)&reg, 1);
  switch (reg.int_on_dataoff){
    case LIS2MDLSensor_CHECK_BEFORE:
      *val = LIS2MDLSensor_CHECK_BEFORE;
      break;
    case LIS2MDLSensor_CHECK_AFTER:
      *val = LIS2MDLSensor_CHECK_AFTER;
      break;
    default:
      *val = LIS2MDLSensor_CHECK_BEFORE;
      break;
  }
  return ret;
}

/**
  * @brief  Data-ready signal on INT_DRDY pin.[set]
  *
  * @param  ctx   read / write interface definitions.(ptr)
  * @param  val   change the values of drdy_on_pin in reg CFG_REG_C
  * @retval       interface status.(MANDATORY: return 0 -> no Error)
  *
  */
int32_t LIS2MDLSensor_drdy_on_pin_set(uint8_t val)
{
  LIS2MDLSensor_cfg_reg_c_t reg;
  int32_t ret;

  ret = LIS2MDLSensor_read_reg(LIS2MDLSensor_CFG_REG_C, (uint8_t*)&reg, 1);
  
  if(ret == 0){
    reg.drdy_on_pin = val;
    ret = LIS2MDLSensor_write_reg(LIS2MDLSensor_CFG_REG_C, (uint8_t*)&reg, 1);
  }
  
  return ret;
}

/**
  * @brief  Data-ready signal on INT_DRDY pin.[get]
  *
  * @param  ctx   read / write interface definitions.(ptr)
  * @param  val   change the values of drdy_on_pin in reg CFG_REG_C.(ptr)
  * @retval       interface status.(MANDATORY: return 0 -> no Error)
  *
  */
int32_t LIS2MDLSensor_drdy_on_pin_get(uint8_t *val)
{
  LIS2MDLSensor_cfg_reg_c_t reg;
  int32_t ret;

  ret = LIS2MDLSensor_read_reg(LIS2MDLSensor_CFG_REG_C, (uint8_t*)&reg, 1);
  *val = reg.drdy_on_pin;

  return ret;
}

/**
  * @brief  Interrupt signal on INT_DRDY pin.[set]
  *
  * @param  ctx   read / write interface definitions.(ptr)
  * @param  val   change the values of int_on_pin in reg CFG_REG_C
  * @retval       interface status.(MANDATORY: return 0 -> no Error)
  *
  */
int32_t LIS2MDLSensor_int_on_pin_set(uint8_t val)
{
  LIS2MDLSensor_cfg_reg_c_t reg;
  int32_t ret;

  ret = LIS2MDLSensor_read_reg(LIS2MDLSensor_CFG_REG_C, (uint8_t*)&reg, 1);
  
  if(ret == 0){
    reg.int_on_pin = val;
    ret = LIS2MDLSensor_write_reg(LIS2MDLSensor_CFG_REG_C, (uint8_t*)&reg, 1);
  }
  
  return ret;
}

/**
  * @brief  Interrupt signal on INT_DRDY pin.[get]
  *
  * @param  ctx   read / write interface definitions.(ptr)
  * @param  val   change the values of int_on_pin in reg CFG_REG_C.(ptr)
  * @retval       interface status.(MANDATORY: return 0 -> no Error)
  *
  */
int32_t LIS2MDLSensor_int_on_pin_get(uint8_t *val)
{
  LIS2MDLSensor_cfg_reg_c_t reg;
  int32_t ret;

  ret = LIS2MDLSensor_read_reg(LIS2MDLSensor_CFG_REG_C, (uint8_t*)&reg, 1);
  *val = reg.int_on_pin;

  return ret;
}

/**
  * @brief  Interrupt generator configuration register.[set]
  *
  * @param  ctx   read / write interface definitions.(ptr)
  * @param  val   registers INT_CRTL_REG.(ptr)
  * @retval       interface status.(MANDATORY: return 0 -> no Error)
  *
  */
int32_t LIS2MDLSensor_int_gen_conf_set(LIS2MDLSensor_int_crtl_reg_t *val)
{
  int32_t ret;
  ret = LIS2MDLSensor_write_reg(LIS2MDLSensor_INT_CRTL_REG, (uint8_t*) val, 1);
  return ret;
}

/**
  * @brief  Interrupt generator configuration register.[get]
  *
  * @param  ctx   read / write interface definitions.(ptr)
  * @param  val   registers INT_CRTL_REG.(ptr)
  * @retval       interface status.(MANDATORY: return 0 -> no Error)
  *
  */
int32_t LIS2MDLSensor_int_gen_conf_get(LIS2MDLSensor_int_crtl_reg_t *val)
{
  int32_t ret;
  ret = LIS2MDLSensor_read_reg(LIS2MDLSensor_INT_CRTL_REG, (uint8_t*) val, 1);
  return ret;
}

/**
  * @brief  Interrupt generator source register.[get]
  *
  * @param  ctx   read / write interface definitions.(ptr)
  * @param  val   registers INT_SOURCE_REG.(ptr)
  * @retval       interface status.(MANDATORY: return 0 -> no Error)
  *
  */
int32_t LIS2MDLSensor_int_gen_source_get(LIS2MDLSensor_int_source_reg_t *val)
{
  int32_t ret;
  ret = LIS2MDLSensor_read_reg(LIS2MDLSensor_INT_SOURCE_REG, (uint8_t*) val, 1);
  return ret;
}

/**
  * @brief  User-defined threshold value for xl interrupt event on generator.
  *         Data format is the same of output data raw: two’s complement with
  *         1LSb = 1.5mG.[set]
  *
  * @param  ctx   read / write interface definitions.(ptr)
  * @param  buff  that contains data to write
  * @retval       interface status.(MANDATORY: return 0 -> no Error)
  *
  */
int32_t LIS2MDLSensor_int_gen_treshold_set(uint8_t *buff)
{
  int32_t ret;
  ret = LIS2MDLSensor_write_reg(LIS2MDLSensor_INT_THS_L_REG, buff, 2);
  return ret;
}

/**
  * @brief  User-defined threshold value for xl interrupt event on generator.
  *         Data format is the same of output data raw: two’s complement with
  *         1LSb = 1.5mG.[get]
  *
  * @param  ctx   read / write interface definitions.(ptr)
  * @param  buff  that stores data read
  * @retval       interface status.(MANDATORY: return 0 -> no Error)
  *
  */
int32_t LIS2MDLSensor_int_gen_treshold_get(uint8_t *buff)
{
  int32_t ret;
  ret = LIS2MDLSensor_read_reg(LIS2MDLSensor_INT_THS_L_REG, buff, 2);
  return ret;
}

/**
  * @}
  *
  */

/**
  * @defgroup    LIS2MDLSensor_serial_interface
  * @brief       This section group all the functions concerning serial
  *              interface management
  * @{
  *
  */

/**
  * @brief  Enable/Disable I2C interface.[set]
  *
  * @param  ctx   read / write interface definitions.(ptr)
  * @param  val   change the values of i2c_dis in reg CFG_REG_C
  * @retval       interface status.(MANDATORY: return 0 -> no Error)
  *
  */
int32_t LIS2MDLSensor_i2c_interface_set(LIS2MDLSensor_i2c_dis_t val)
{
  LIS2MDLSensor_cfg_reg_c_t reg;
  int32_t ret;

  ret = LIS2MDLSensor_read_reg(LIS2MDLSensor_CFG_REG_C, (uint8_t*)&reg, 1);
  
  if(ret == 0){
    reg.i2c_dis = (uint8_t)val;
    ret = LIS2MDLSensor_write_reg(LIS2MDLSensor_CFG_REG_C, (uint8_t*)&reg, 1);
  }
  
  return ret;
}

/**
  * @brief  Enable/Disable I2C interface.[get]
  *
  * @param  ctx   read / write interface definitions.(ptr)
  * @param  val   Get the values of i2c_dis in reg CFG_REG_C.(ptr)
  * @retval       interface status.(MANDATORY: return 0 -> no Error)
  *
  */
int32_t LIS2MDLSensor_i2c_interface_get(LIS2MDLSensor_i2c_dis_t *val)
{
  LIS2MDLSensor_cfg_reg_c_t reg;
  int32_t ret;

  ret = LIS2MDLSensor_read_reg(LIS2MDLSensor_CFG_REG_C, (uint8_t*)&reg, 1);
  switch (reg.i2c_dis){
    case LIS2MDLSensor_I2C_ENABLE:
      *val = LIS2MDLSensor_I2C_ENABLE;
      break;
    case LIS2MDLSensor_I2C_DISABLE:
      *val = LIS2MDLSensor_I2C_DISABLE;
      break;
    default:
      *val = LIS2MDLSensor_I2C_ENABLE;
      break;
  }
  return ret;
}

/**
  * @}
  *
  */

/************************ (C) COPYRIGHT STMicroelectronics *****END OF FILE****/
