vrbadev/Gloves-Equipped-with-Motion-Sensors-Bachelor-Project-HW-FW-SW/Firmware/uVision/BlueNRG1_it.c

/**
  ******************************************************************************
  * @file    BlueNRG1_it.c
  * @author  RF Application Team
  * @version V1.0.0
  * @date    September-2015
  * @brief   Main Interrupt Service Routines.
  *          This file provides template for all exceptions handler and
  *          peripherals interrupt service routine.
  ******************************************************************************
  * @attention
  *
  * THE PRESENT FIRMWARE WHICH IS FOR GUIDANCE ONLY AIMS AT PROVIDING CUSTOMERS
  * WITH CODING INFORMATION REGARDING THEIR PRODUCTS IN ORDER FOR THEM TO SAVE
  * TIME. AS A RESULT, STMICROELECTRONICS SHALL NOT BE HELD LIABLE FOR ANY
  * DIRECT, INDIRECT OR CONSEQUENTIAL DAMAGES WITH RESPECT TO ANY CLAIMS ARISING
  * FROM THE CONTENT OF SUCH FIRMWARE AND/OR THE USE MADE BY CUSTOMERS OF THE
  * CODING INFORMATION CONTAINED HEREIN IN CONNECTION WITH THEIR PRODUCTS.
  *
  * <h2><center>&copy; COPYRIGHT 2015 STMicroelectronics</center></h2>
  ******************************************************************************
  */

/* Includes ------------------------------------------------------------------*/
#include "BlueNRG_x_device.h"
#include "crash_handler.h"
#include "miscutil.h"
#include "bluenrg1_stack.h"

/** @addtogroup BlueNRG1_StdPeriph_Examples
  * @{
  */

/** @addtogroup Micro_Examples Micro Examples
  * @{
  */

/** @addtogroup Micro_HelloWorld Micro HelloWorld Example
  * @{
  */
/* Private typedef -----------------------------------------------------------*/
/* Private define ------------------------------------------------------------*/
/* Private macro -------------------------------------------------------------*/
/* Private variables ---------------------------------------------------------*/
/* Private function prototypes -----------------------------------------------*/
/* Private functions ---------------------------------------------------------*/

/******************************************************************************/
/*            Cortex-M0 Processor Exceptions Handlers                         */
/******************************************************************************/

/**
  * @brief  This function handles NMI exception.
  */
NOSTACK_FUNCTION(NORETURN_FUNCTION(void NMI_Handler(void)))
{
  HAL_CrashHandler(__get_MSP(), NMI_SIGNATURE);
  /* Go to infinite loop when NMI exception occurs */
  while (1)
  {}
}

/**
  * @brief  This function handles Hard Fault exception.
  */
NOSTACK_FUNCTION(NORETURN_FUNCTION(void HardFault_Handler(void)))
{
  HAL_CrashHandler(__get_MSP(), HARD_FAULT_SIGNATURE);
  /* Go to infinite loop when Hard Fault exception occurs */
  while (1)
  {}
}

/**
  * @brief  This function handles SVCall exception.
  */
void SVC_Handler(void)
{
}


///**
//  * @brief  This function handles SysTick Handler.
//  */
//void SysTick_Handler(void)
//{
//  
//}


/******************************************************************************/
/*                 BlueNRG-1 Peripherals Interrupt Handlers                   */
/*  Add here the Interrupt Handler for the used peripheral(s) (PPP), for the  */
/*  available peripheral interrupt handler's name please refer to the startup */
/*  file (system_bluenrg1.c).                                               */
/******************************************************************************/

/**
  * @brief  This function handles DMA Handler.
  */
void DMA_Handler(void)
{
  
  
}

void Blue_Handler(void)
{
   // Call RAL_Isr
   RAL_Isr();
}

/**
  * @}
  */ 

/**
  * @}
  */ 

/**
  * @}
  */ 

/******************* (C) COPYRIGHT 2014 STMicroelectronics *****END OF FILE****/
