vrbadev/Gloves-Equipped-with-Motion-Sensors-Bachelor-Project-HW-FW-SW/Firmware/uVision/inc/delay.h

#ifndef DELAY_H__
#define DELAY_H__

#include "BlueNRG1_conf.h"

void systick_init(void);
void delay_ms(uint32_t delay);
uint32_t get_ms(void);

void mft_init(void);
void delay_us(uint16_t delay);

#endif
